marukitano/BEP3.0/BEP31/Foto_bestückter_Print.jpg

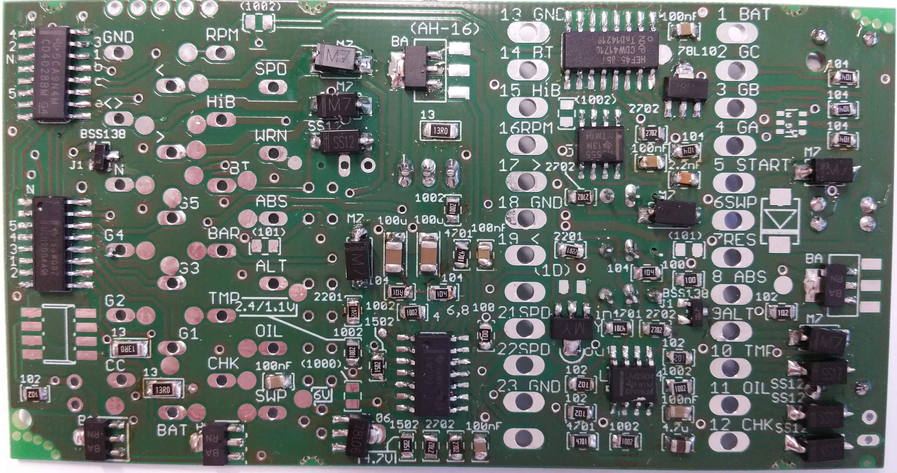
BEP31/Foto_bestückter_Print.jpg
