marukitano/BEP3.0/Liste verbessungen BEP3.pdf

Liste verbessungen BEP3.1 zu BEP3.2:

- ABS abschaltbar machen (zusätzlicher switch)
- Für das neue gehäuse 1mm kürzen (dann passt es ins alte und ins neue gehäuse, siehe bild )

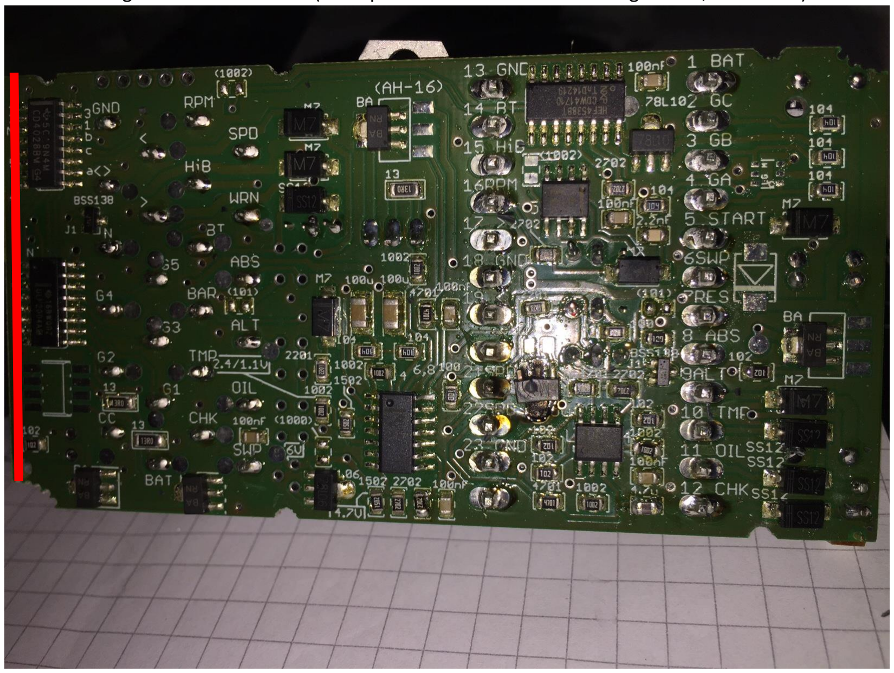
[picture p6: figure]

- Aussparung für Schraube auch an oberer Ecke anbringen (damit passts in beide gehäuse, siehe bild 2). Dafür müsste der 4028 ein stück versetzt werden.
- Beschriftung der schalter vervollständigen

- Stencil bestellen, der die aussparung für die Schutzdiode NICHT hat. Oft sind die Pads gebrückt nach den Lötofen und das gibt kurriose Fehler…

- Abstand Lödpads vergrössern zwischen switch und diode (häufiger fehler nach den Lötofen, siehe bild)
