marukitano/BEP3.0/BEP2 final/BMW_Gerberview.pdf

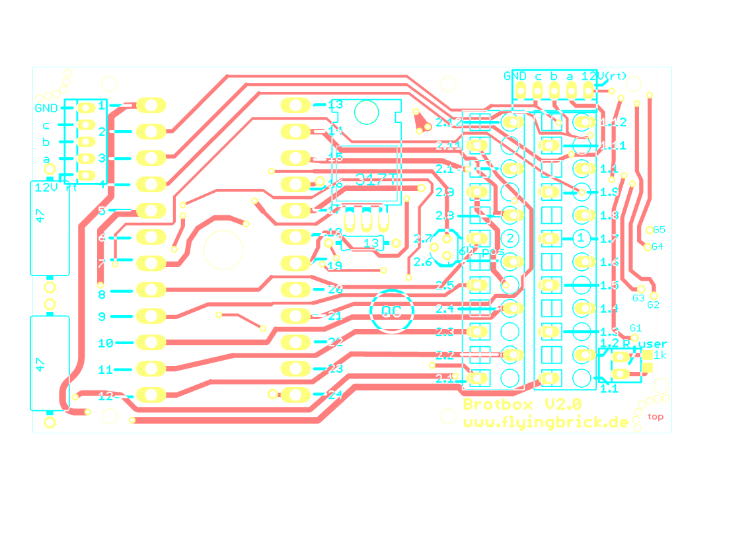
[picture p7: figure]

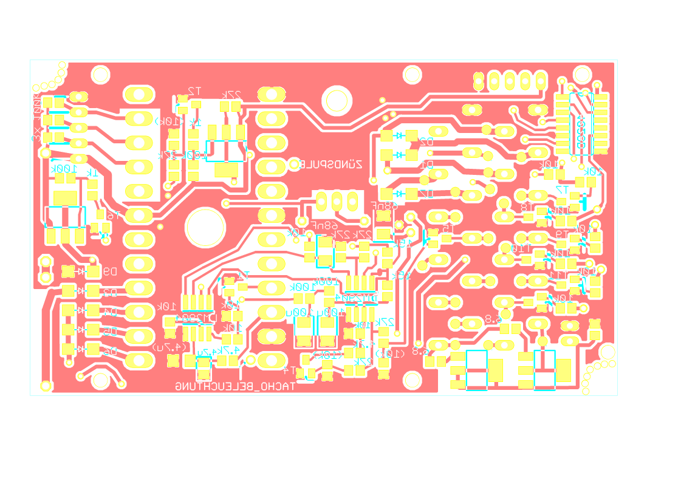
[picture p8: figure]
