marukitano/BEP3.0/BEP2 final/Board und Case BMW.pdf

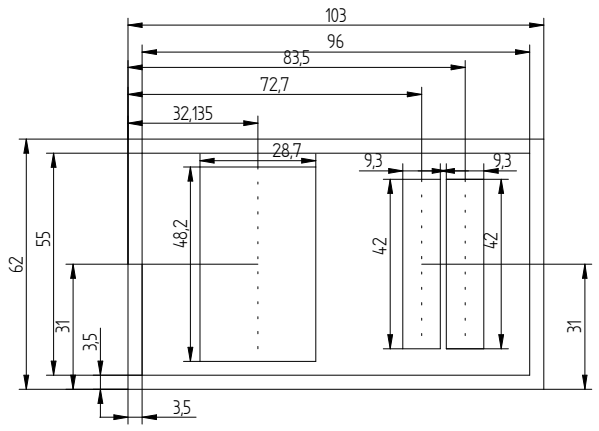
[picture p9: figure]
