marukitano/BEP3.0/BEP2 final/BMW_final_image.png

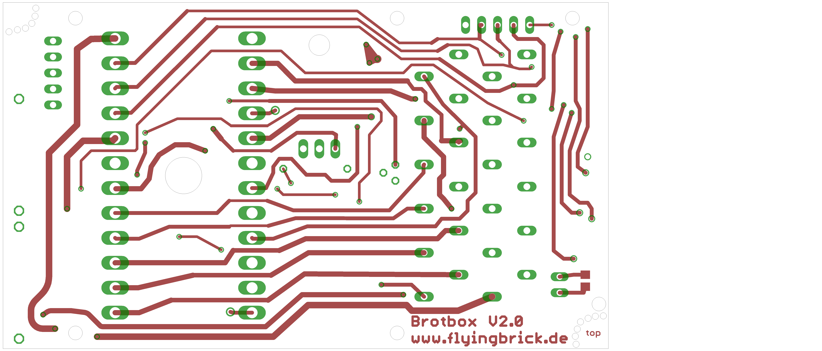
BEP2 final/BMW_final_image.png
