marukitano/BEP3.0/BEP2rev1/BEPrev1_BestückungAnsicht.png

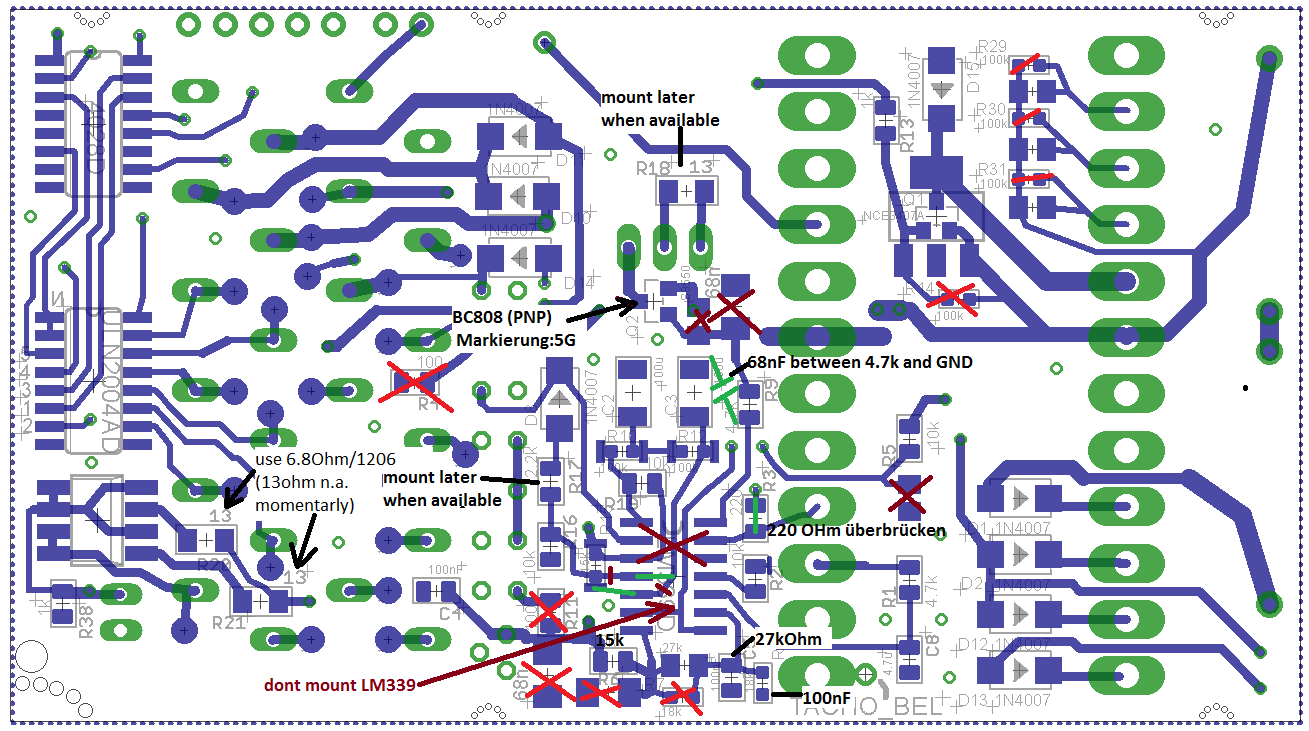
BEP2rev1/BEPrev1_BestückungAnsicht.png
