marukitano/BEP3.0/BEP2rev1/BEPrev_bot.png

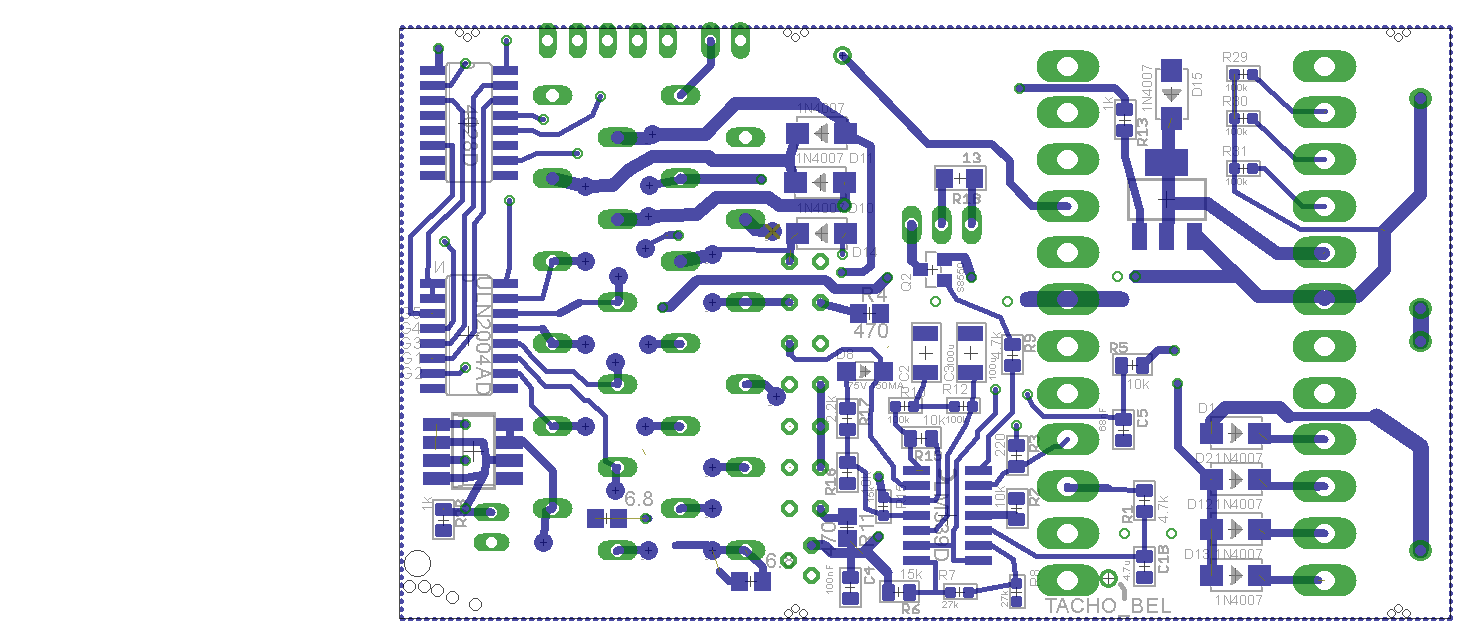
BEP2rev1/BEPrev_bot.png
