marukitano/BEP3.0/BEP2rev1/BEPrev_top.png

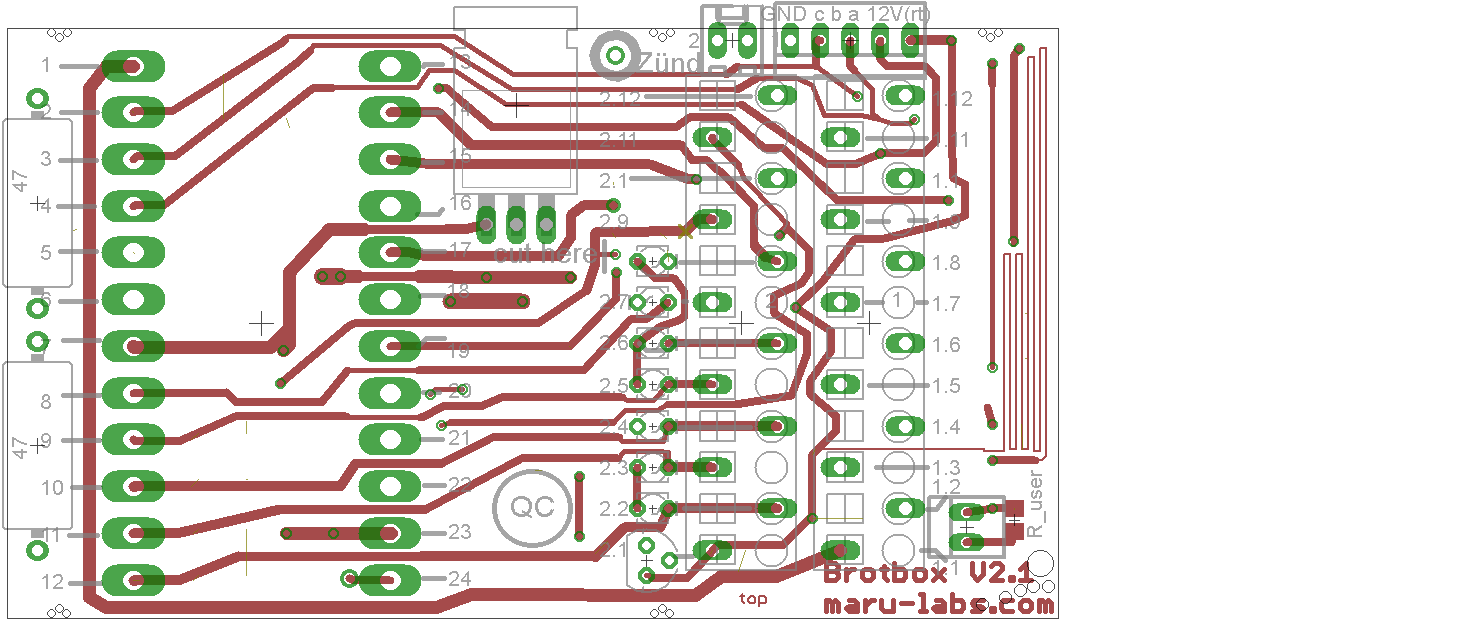
BEP2rev1/BEPrev_top.png
