marukitano/BEP3.0/BEP3/BEP3 Bestückung (weisser Hintergrund).png

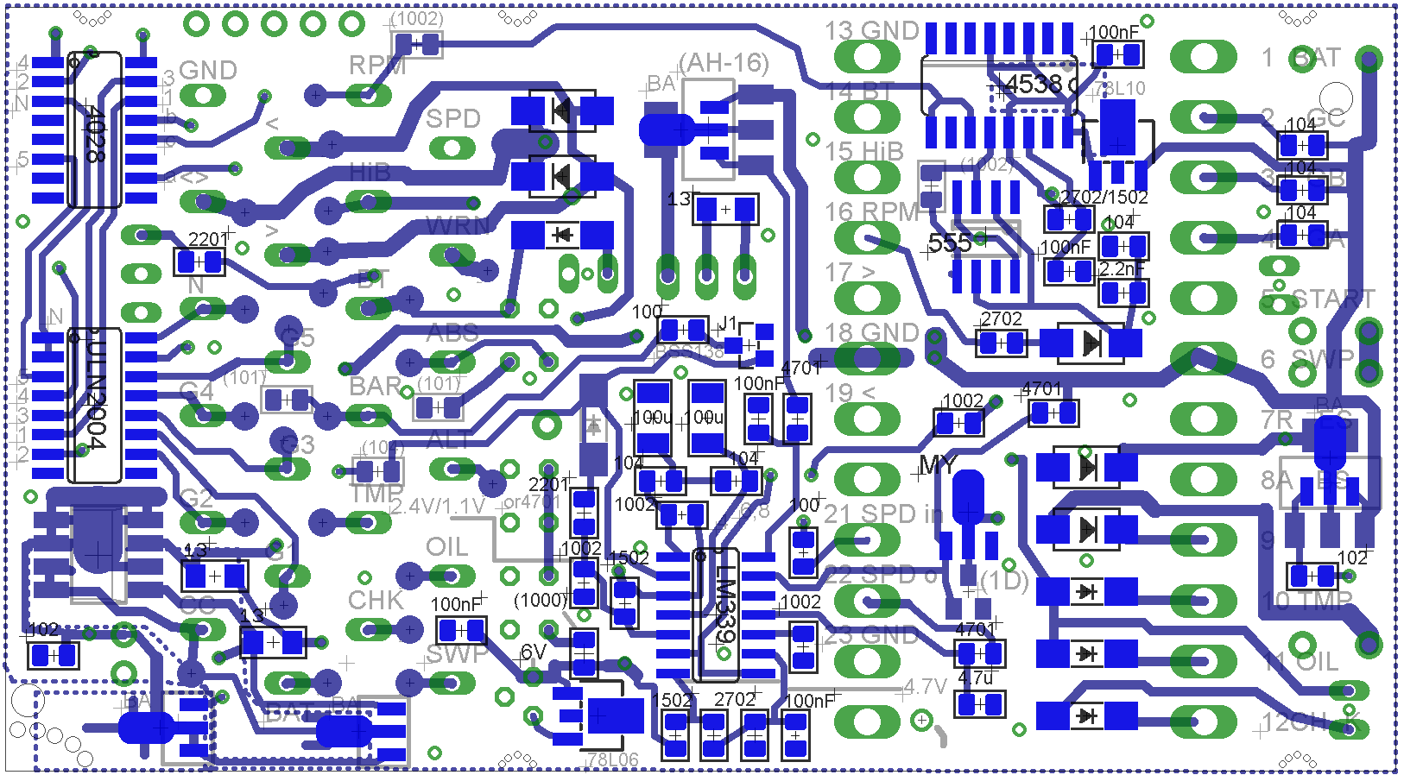
BEP3/BEP3 Bestückung (weisser Hintergrund).png
