marukitano/BEP3.0/BEP3/BEP3 Bestückung.png

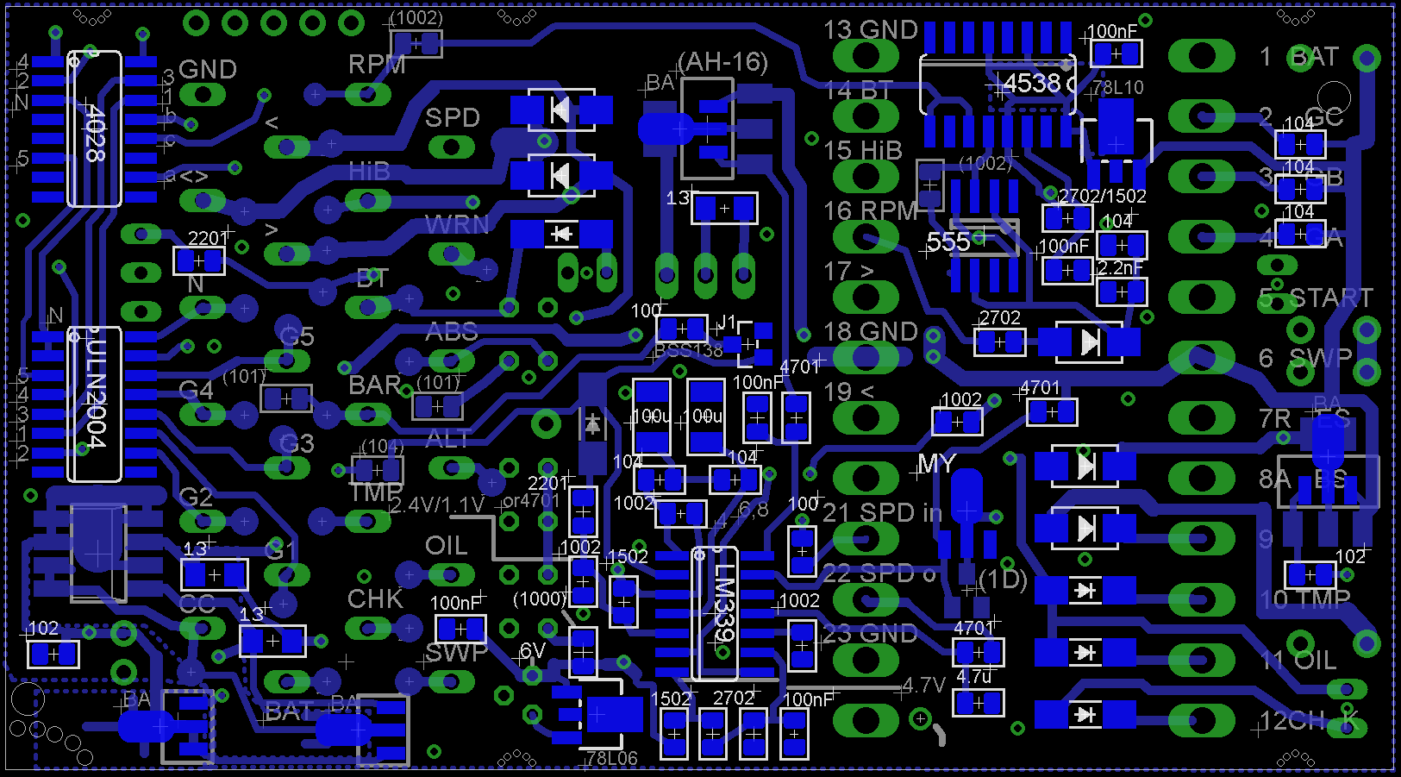
BEP3/BEP3 Bestückung.png
