marukitano/BEP3.0/BEP3/bot.png

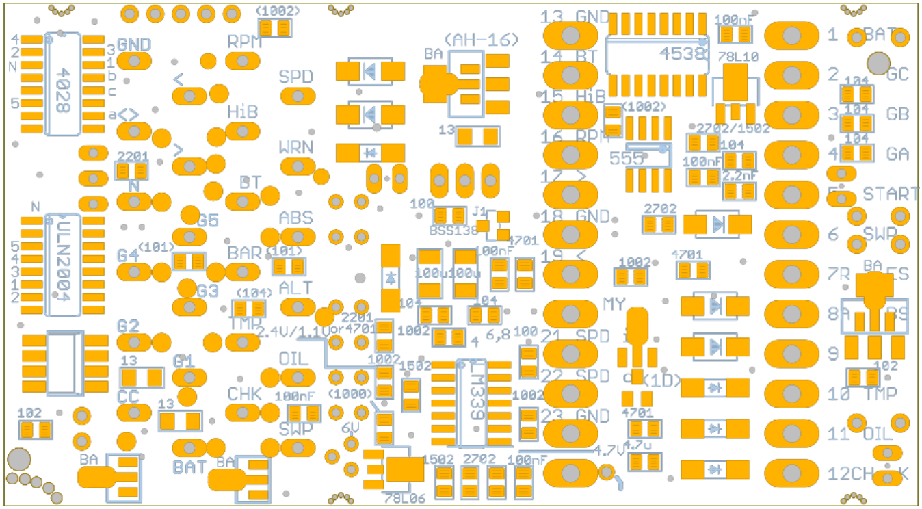
BEP3/bot.png
