marukitano/BEP3.0/BEP3/Schema Bep3.png

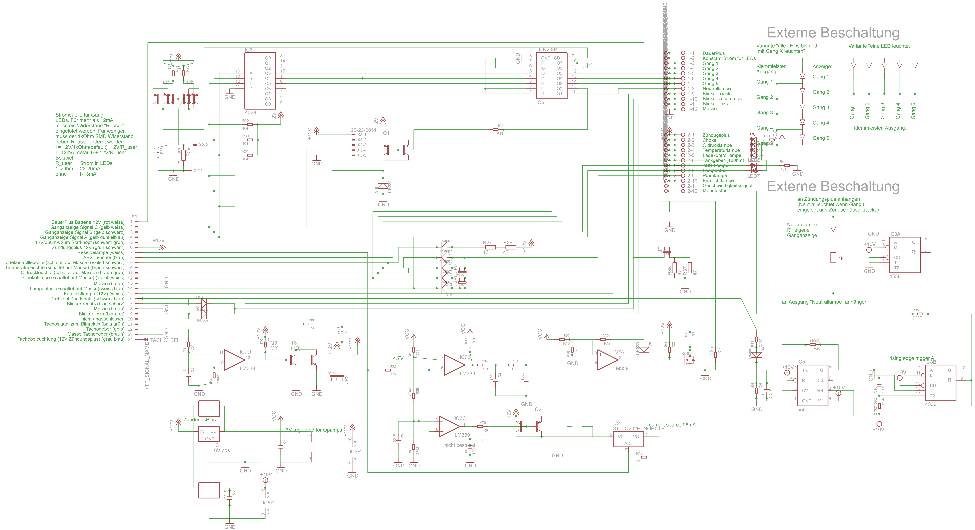
BEP3/Schema Bep3.png
