marukitano/BEP3.0/BEP3/top.png

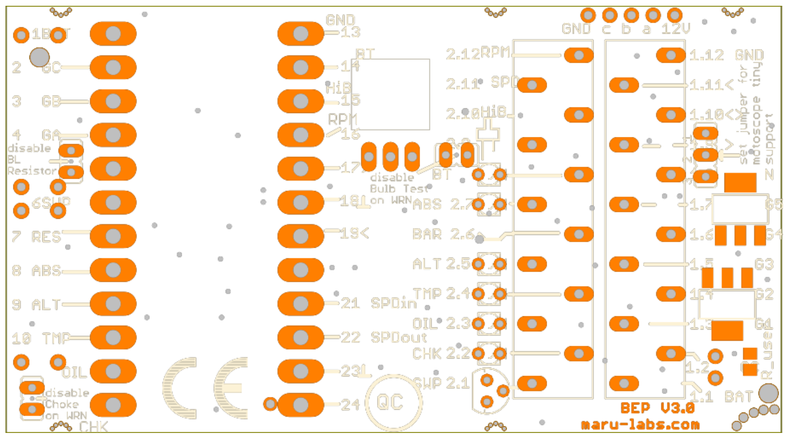
BEP3/top.png
