marukitano/BEP3.0/BEP31/Bestückungs-Plan(gimp)/Leiterbahnen mit SMD.png

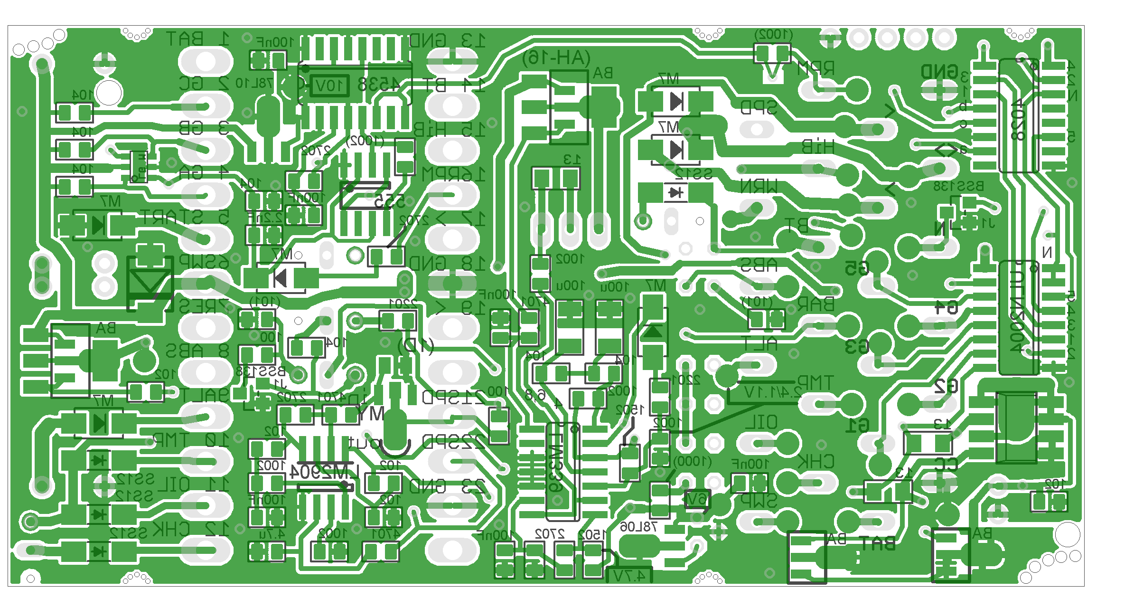
BEP31/Bestückungs-Plan(gimp)/Leiterbahnen mit SMD.png
