marukitano/BEP3.0/BEP31/Bestückungs-Plan(gimp)/SMD Teile.png

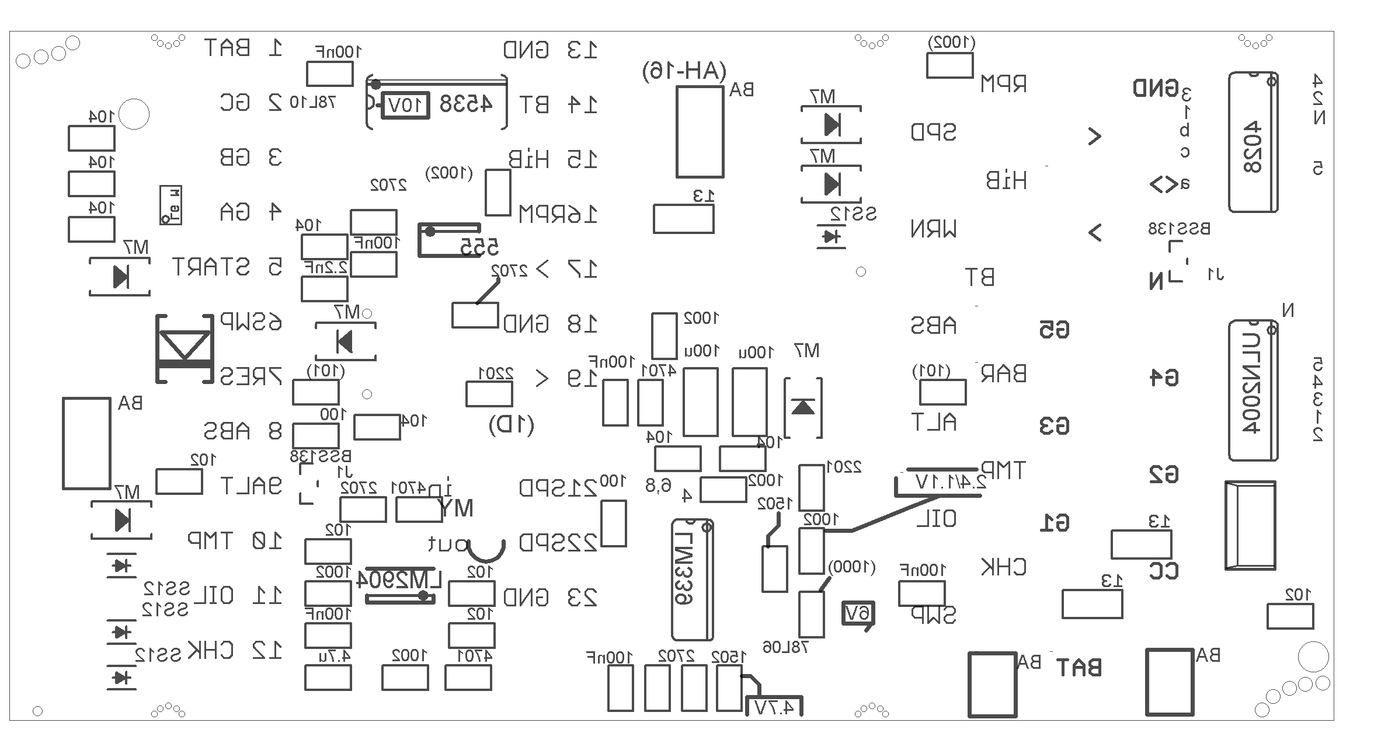
BEP31/Bestückungs-Plan(gimp)/SMD Teile.png
