marukitano/BEP3.0/BEP32/BEP32_6panel_Milling Layer 46 + Vcuts Layer 20 Eagle screenshot.png

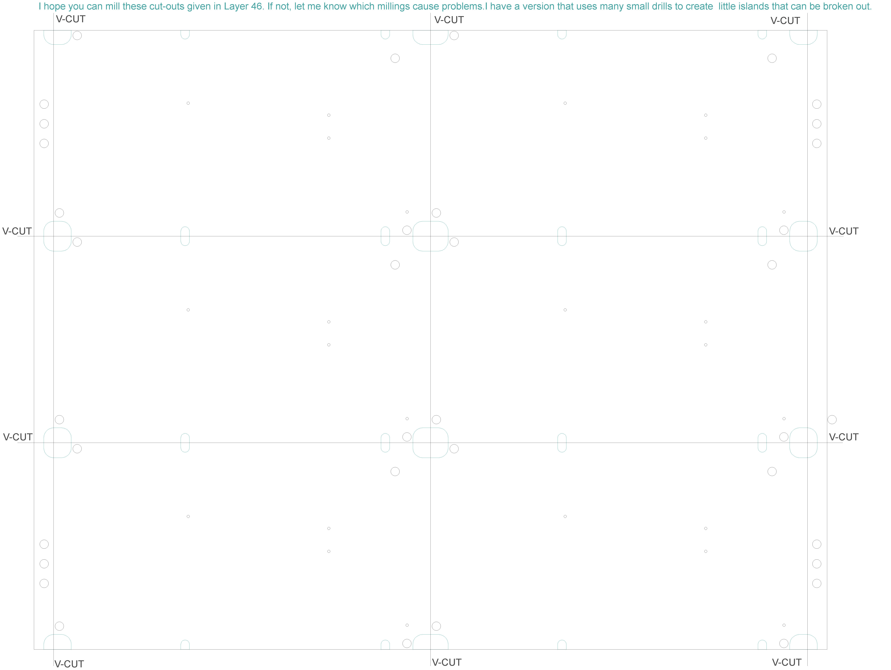
BEP32/BEP32_6panel_Milling Layer 46 + Vcuts Layer 20 Eagle screenshot.png
