marukitano/BEP3.0/BEP32/BEP32_Bestückungsdruck.PNG

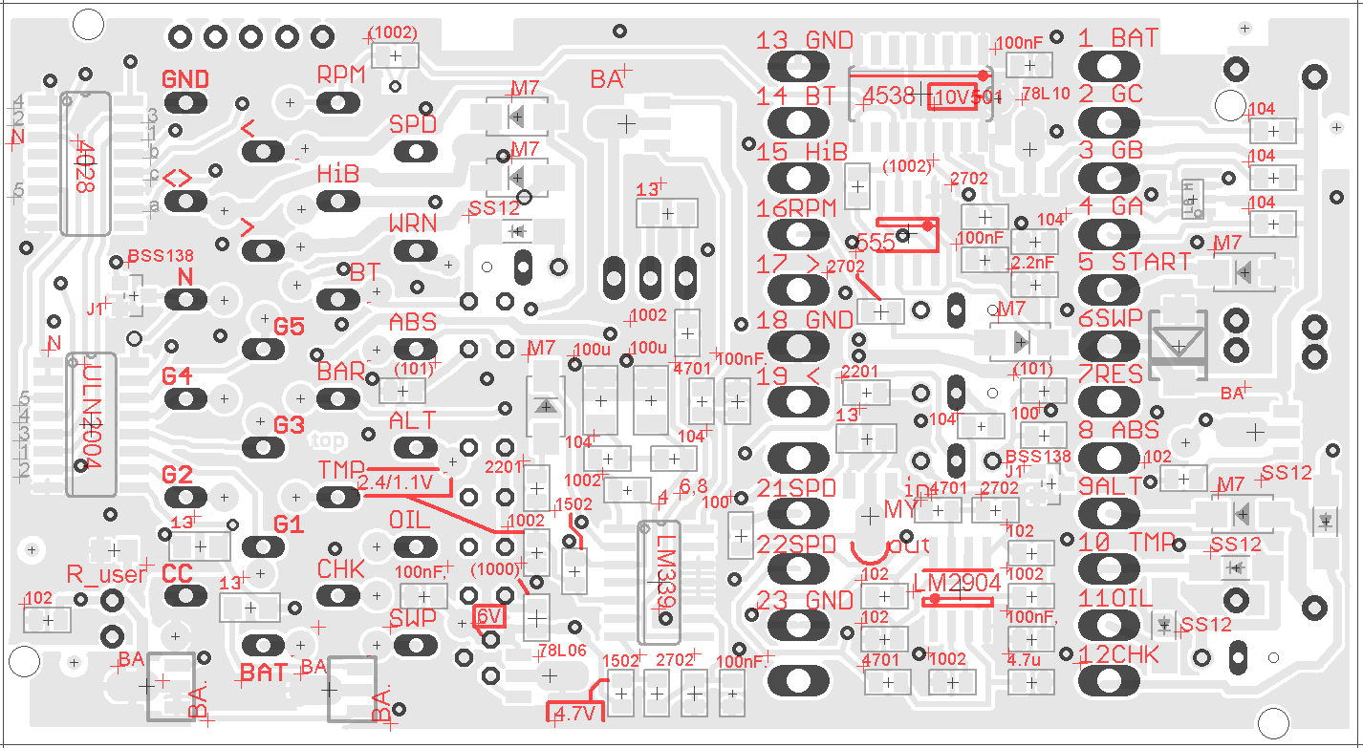
BEP32/BEP32_Bestückungsdruck.PNG
