marukitano/BEP3.0/BEP32/BEP32_Schalterbeschriftung.png

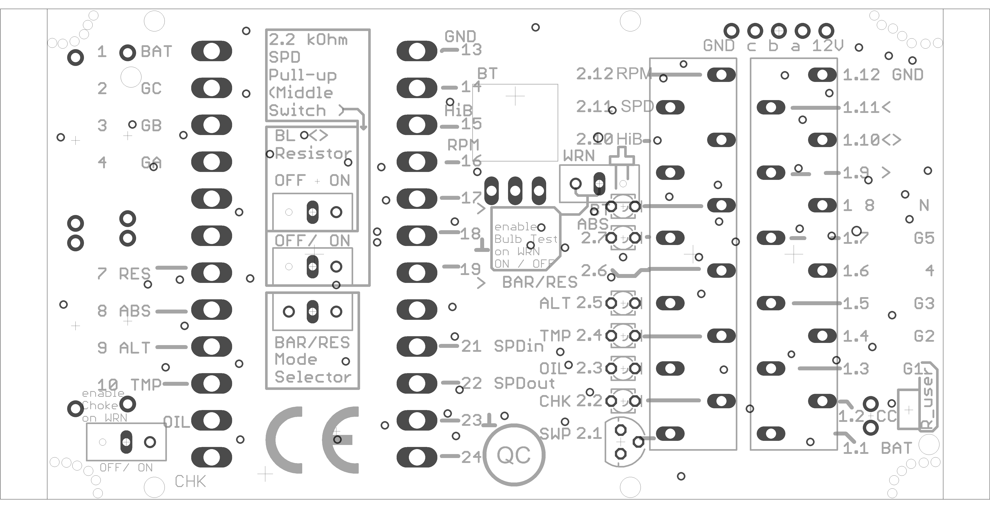
BEP32/BEP32_Schalterbeschriftung.png
