marukitano/BEP3.0/BEP33/BEP33 cream direkt export.png

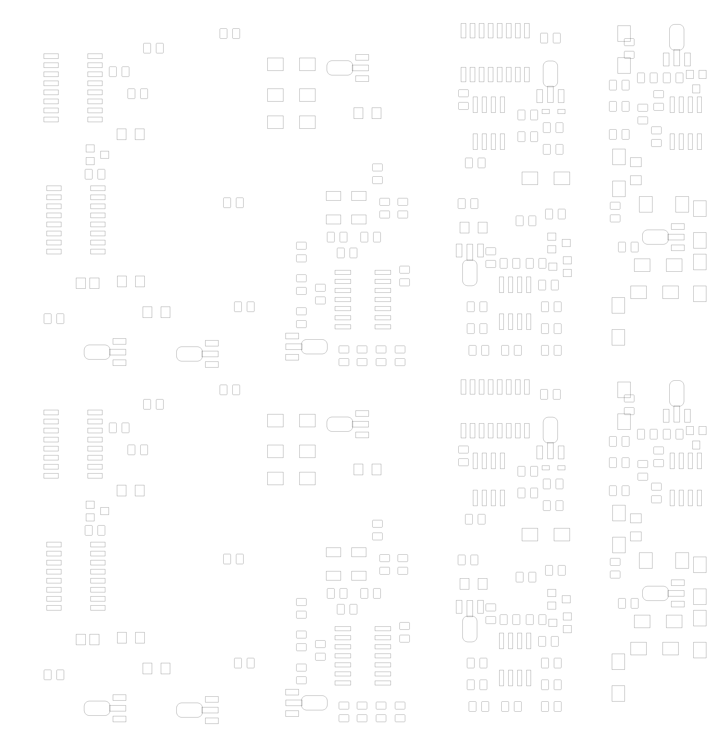
BEP33/BEP33 cream direkt export.png
