marukitano/BEP3.0/BEP33/sht31.png

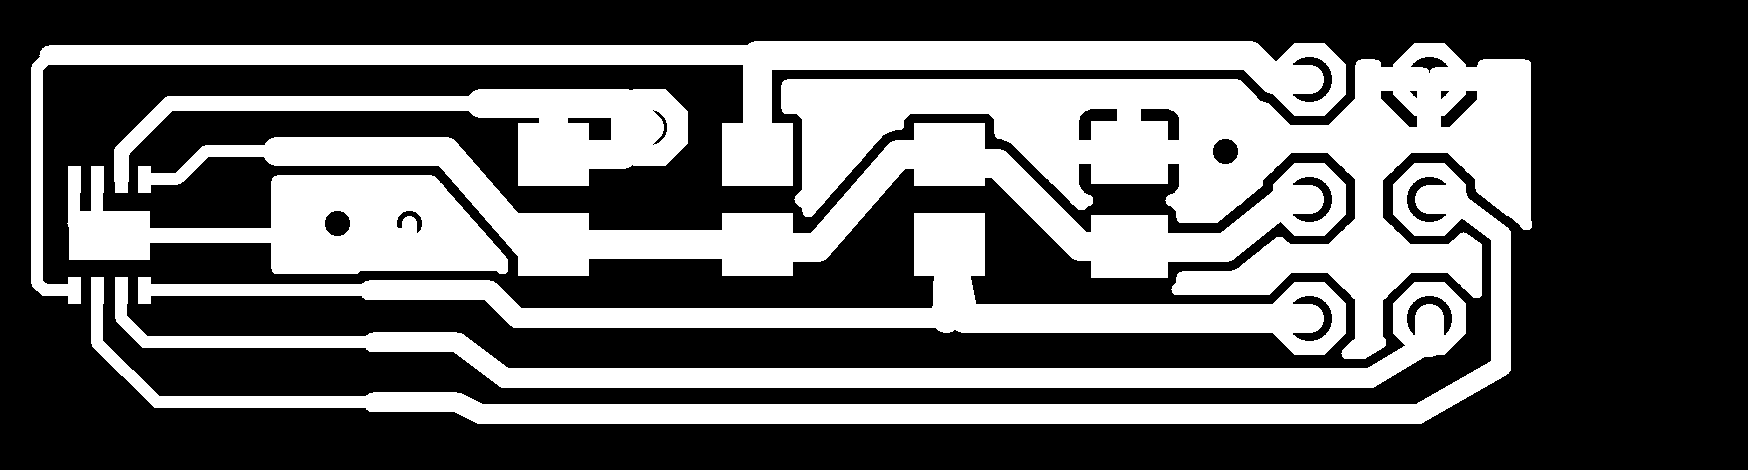
BEP33/sht31.png
