marukitano/BEP3.0/Brotbox original/Ganganzeige/Ganganzeige_nutzen_maske_bearb.png

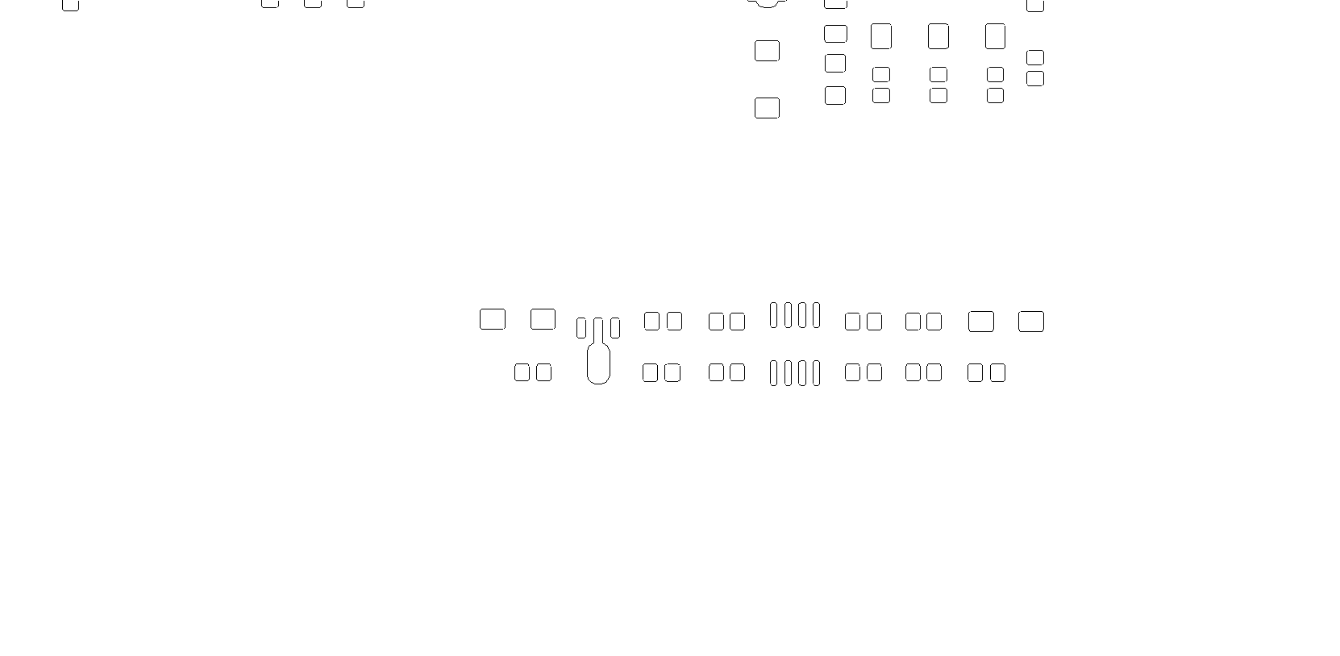
Brotbox original/Ganganzeige/Ganganzeige_nutzen_maske_bearb.png
