marukitano/BEP3.0/Kdiag/Board2.png

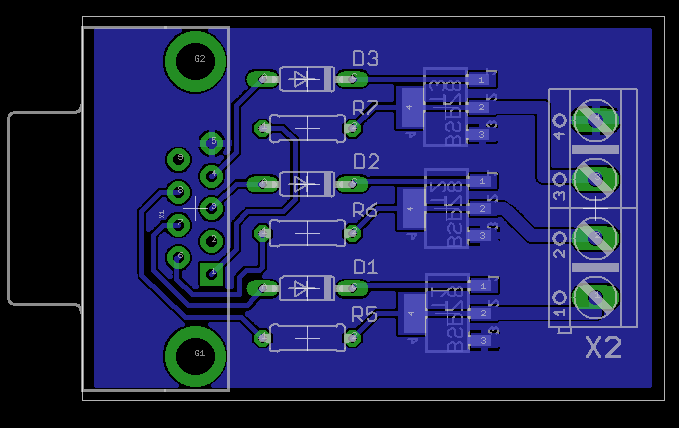
Kdiag/Board2.png
