marukitano/BEP3.0/BEP31/BEP31_final_BOM_ELON-MUSK_Jul-18-161850-2017_Conflict.xlsx

Dimensionen:
Board: | 96mmx50mm. FR4 1.6mm, HASL verzinnt (lead free)
Stückzahl | 500 und 1000
BOM:
SMD Bauteile auf Rückseite:
Qty | Value | Package | Device | Parts | Description |  |  | Farnell | Aliexpress | Preis/Stück in US$ | bei Stück-zahl | Bedarf f.500 Prints | Stock Marulabs | auf Rolle bei Marulabs vorhanden | techn. Anforderung für Alternative | Bemerkung
6 | 100nF | C0805 | CERAMIC-100NF-50V-10%-X7R(0805) | C4, C5, C7, C9, C10, C11 |  |  |  | ? | ? | 0.01 |  | 3000 | 0 | nein | ≥20V | ev. 0603
1 | 2.2nF | C0805 | CERAMIC-100NF-50V-10%-X7R(0805) | C1 |  |  |  |  | 32375506423 (https://www.aliexpress.com/item/Free-shipping-0805-SMD-capacitor-2200P-2-2nf-50V-222K-100PCS/32375506423.html) | 0.0045 | 200 | 500 | 0 | nein | ≥50V | ev. 0603
1 | 4.7u | C0805 | CERAMIC-4.7UF-25V-10%-X5R(0805) | C8 |  |  |  |  | 32376068362 (https://www.aliexpress.com/item/Free-shipping-0805-SMD-capacitor-4-7uf-50V-475Z-100PCS/32376068362.html) | 0.0059 | 200 | 500 | 0 | nein | ≥16V | ev. 0603
2 | 100u | C1206 | CERAMIC-100UF-6.3V-20%-X5R(1206) | C2, C3 |  |  |  |  | 32376068793 (https://www.aliexpress.com/item/Free-shipping-1206-SMD-capacitor-100uf-16V-107Z-100PCS/32376068793.html) | 0.041 | 100 | 1000 | 0 | nein | ≥6V | ev. 0805
6 | 1N4007 | DO-214AC | DIODE-GEN-PURPOSE-1KV-1A(DO-214AC) | D1, D3, D8, D10, D11, D15 |  |  |  |  | 32687291008 (https://www.aliexpress.com/item/3000PCS-1N4007-M7-SMA-DO-214AC-1A-1000-V-SMD-Rectifler-diodos/32687291008.html) | 0.008533333333 | 3000 | 3000 | 4000 | ja(Rolle=2000) | ≥1A,≥100V
4 | 1N5817 | DO-214AC | Schottky Diode | D2, D12, D13, D14 |  |  |  |  | 2024887597 (https://www.aliexpress.com/item/Free-Shipping-1000PCS-SS12-1N5817-1A-20V-SMA-Schottky-diode/2024887597.html) | 0.01 | 1000 | 2000 | ca. 1900 | ja(Rolle=2000) | ≥1A,≥20V | Flussspannung muss <0.25V sein bei 0.19mA Strom
1 | NE555D | SO08 | NE555D | IC5 | TIMER |  |  |  | 32686681723 (https://www.aliexpress.com/item/500PCS-NE555DR-NE555D-NE555-IC-555-SMD-assurance-NEW/32686681723.html) | 0.0264 | 500 | 500 | 0 | nein(Rolle=2500?)
1 | LM2904 | SO08 | LM2904 | IC10 | OP AMP also LM158; LM258; LM2904 |  |  |  | 32518015605 (https://www.aliexpress.com/item/500PCS-LM2904-LM2904DR-LM2904D-SOP-8/32518015605.html) | 0.03 | 500 | 500 | 0 | nein(Rolle=2500?) |  | Alternativ LM358/258/158
1 | LM339 | SO14 | LM339D | IC7 | Low Power Quad Comparators |  |  |  | 1245879199 (https://www.aliexpress.com/item/Free-Shipping-100PCS-LOT-Original-Integrated-circuit-ics-LM339-LM339DR/1245879199.html) | 0.047 | 100 | 500 | 0 | nein(Rolle=2500?) |  | Alternativ LM2901,LM239/139
1 | 4028 | SO16 | 4028D | IC3 | BCD to decimal DECODER |  |  | 2342417RL (http://ch.farnell.com/webapp/wcs/stores/servlet/ProductDisplay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) |  | 0.134 | 1000 | 500 | 500 Freihand | nein(Rolle=?) |  | CD4028BM
1 | 4538 | SO16 | 4538D | IC8 | Dual monostable MULTIVIBRATOR |  |  |  | 32694256723 (https://www.aliexpress.com/item/HEF4538-HEF4538BT-digital-logic-circuit-SOP16-imported-new-original-MHBX2/32694256723.html) | 0.14 | 100 | 500 | 0 | nein(Rolle=2500?) |  | CD14538BM alternativ
1 | ULN2004 | SO16 | ULN2004AD | IC6 | DRIVER ARRAY |  |  |  | 32667261685 (https://www.aliexpress.com/item/Free-shipping-500pcs-lot-ULN2004-ULN2004A-ULN2004ADR-SOP-16/32667261685.html) | 0.1 | 500 | 500 | 0 | nein(Rolle=2500?)
2 | BSS-138 | SOT-23 | SMD-MOSFET-N-CH-50V-200MA-BSS138W-7-F(SOT-23) | Q10, Q11 | BSS138W-7-F |  |  |  | 32316697150 (https://www.aliexpress.com/item/1000-PCS-LBSS138LT1G-SOT-23-BSS138-J1-Power-MOSFET-200-mAmps-50-Volts-N-hannel-SOT/32316697150.html) | 0.011 | 1000 | 1000 | 0 | nein(Rolle=3000) | RDS<6Ω | alternativ anderer SOT89 N Mosfet (Kleinsignal)
4 | BA | SOT89 | PNP-TRANSISTOR_SOT89 | Q1, Q2, Q7, Q8 | PNP TRANSISTOR 2SB1132 1A 32V |  |  |  | 32390023505 (https://www.aliexpress.com/item/Free-shopping-1000-PCS-2SB1132-SOT-89-B1132-PNP-1A-32V/32390023505.html) | 0.02 | 1000 | 2000 | 0 | nein | ≥1A,≥20V,HFE>100 bei 500mA | Exot! Ersatz muss gefunden werden oder wir kaufen mehr bei Aliexpress
1 | MY | SOT89 | NPN-TRANSISTOR_SOT89 | Q9 | NPN TRANSISTOR 2SC2873 2A 50V |  |  |  | 32590988708 (https://www.aliexpress.com/item/2SC2873-Y-2SC2873-MY-SOT89-NPN-Transistor-IC-x-1000PCS/32590988708.html) | 0.022 | 1000 | 500 | 0 | nein | ≥500mA,≥20V | Exot! Ersatz muss gefunden werden oder wir kaufen mehr bei Aliexpress. SOT89 N Mosfet wäre auch möglich
1 | 10V pos | SOT89 | 78L10 | IC2 | VOLTAGE REGULATOR |  |  |  | 32714846870 (https://www.aliexpress.com/item/500pcs-lot-in-stock-CJ78L10-78L10-10V-SOT-89/32714846870.html) | 0.04 | 500 | 500 | 500 | nein(Rolle=1000) |  | vorhande 500 Teile könnten wir auf leere Rolle spannen
1 | 6V pos | SOT89 | 78L06 | IC1 | VOLTAGE REGULATOR |  |  |  | 32716599879 (https://www.aliexpress.com/item/1000PCS-in-stock-78L06-6V-SOT-89/32716599879.html) | 0.02 | 1000 | 500 | 1000 | ja(Rolle=1000)
7 | 104 | R0805 | 100k | R10, R12, R22, R24, R29, R30, R31 |  |  |  | 2498052 (http://ch.farnell.com/walsin/wr08x1003ftl/dicksch-widerstand-100k-1-150v/dp/2498052) |  | 0.0013 | 5000 | 3500 | 5000 | ja |  | durch Zollner Standard 0603 ersetzen ausser zwei 1kOhm Widerständen (144mW Last ist zuviel für 0603)
5 | 2702 | R0805 | 27k | R8, R25, R44,R33,R34 |  |  |  | 2498084 (http://ch.farnell.com/walsin/wr08x2702ftl/dicksch-widerstand-27k-1-150v/dp/2498084) |  | 0.0013 | 5000 | 2500 | 5000 | ja
2 | 1502 | R0805 | 15k | R6, R15 |  |  |  | 2498062 (http://ch.farnell.com/walsin/wr08x1502ftl/dicksch-widerstand-15k-1-150v/dp/2498062) |  | 0.0013 | 5000 | 1000 | 5000 | ja
5 | 1002 | R0805 | 10k | R2, R5, R16, R19, R42 |  |  |  | 2498051 (http://ch.farnell.com/walsin/wr08x1002ftl/dicksch-widerstand-10k-1-150v/dp/2498051) |  | 0.0013 | 5000 | 2500 | 5000 | ja
3 | 4701 | R0805 | 4k7 | R1, R9, R32 |  |  |  | 2498105 (http://ch.farnell.com/walsin/wr08x4701ftl/dicksch-widerstand-4k7-1-150v/dp/2498105) |  | 0.0013 | 5000 | 1500 | 5000 | ja
2 | 2201 | R0805 | 2k2 | R17, R23 |  |  |  | 2498077 (http://ch.farnell.com/webapp/wcs/stores/servlet/ProductDisplay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) |  | 0.0013 | 5000 | 1000 | 5000 | ja
5 | 102 | R0805 | 1k | R13, R38, R43, R45, R46 |  |  |  | 2498050 (http://ch.farnell.com/walsin/wr08x1001ftl/dicksch-widerstand-1k-1-150v-0805/dp/2498050) |  | 0.0013 | 5000 | 2500 | 5000 | ja | >144mW (2 Stück)
2 | 100 | R0805 | 10R | R3,R7 |  |  |  | 2498048 (http://ch.farnell.com/walsin/wr08x10r0ftl/dicksch-widerstand-10r-1-150v/dp/2498048) |  | 0.0013 | 5000 | 1000 | 5000 | ja
3 | 13 | R1206 | 13R | R18, R20, R21 |  |  |  | 2497996 (http://ch.farnell.com/webapp/wcs/stores/servlet/ProductDisplay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) |  | 0.0021 | 5000 | 1500 | 5000 | ja | >120mW | ev 0805 jedoch besser 1206 (therm. Last ist 120mW und krit. Bauteil)
Zwischentotal: |  |  |  |  |  |  |  |  |  | 0.6596
Gehäuse und Platine
1 |  |  |  |  | Gehäuse |  |  |  | Reichelt SP+2000+SW (http://www.reichelt.de/SP-2000-SW/3/index.html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) | 2.343 | 1
1 |  |  |  |  | Platine |  |  |  | Seedstudio | 0.8 | 350
Zwischentotal: |  |  |  |  |  |  |  |  |  | 3.143
THT Bauteile auf vorderseite (wird voraussichtlich von Marulabs bestückt)
1 | LM317 | TO220 |  |  | Spannungsregler |  |  |  | 1246203110 (https://www.aliexpress.com/item/Free-Shipping-50PCS-POWER-TRANSISTORS-LM317-LM317T-TO-220-ST/1246203110.html) | 0.095 | 100
4 | 47 |  |  |  | 2W Leistungswiderstand bedrahtet |  |  |  | 32523580839 (https://www.aliexpress.com/item/Free-Shipping-200pcs-DIP-Resistors-carbon-Resisters-2W-47ohm-5-Carbon-Film-Resistor/32523580839.html) | 0.0375 | 200
2 | 3.96mm Pitch 12P |  |  |  | BMW Pfostenstecker |  |  |  | 888918208 (https://www.aliexpress.com/item/Free-shipping-100Pcs-lot-Wholesale-3-96mm-Pitch-12-Pins-PCB-Male-Box-Header-Bar-Connector/888918208.html) | 0.1728 | 100
5 | L8.5*W3.5MM 3P 2T mini toggle |  |  |  | ON/OFF Umschalter |  |  |  | 1800702995 (https://www.aliexpress.com/item/Free-shipping-1000PCS-L8-5-W3-5MM-3P-2T-mini-toggle-slide-switch-Handle-high-3mm/1800702995.html) | 0.0228 | 1000
2 | WAGO 2081-1132 |  |  |  | Wago Klemmleiste |  |  |  | Wago Schweiz | 2.1 | 500
Zwischentotal: |  |  |  |  |  |  |  |  |  | 4.9046
Optionale Teile (ev. für EMV Verträglichkeit notwendig)
1 | NUP4304SOT457_R | SOT457R_PHILIPS | NUP4304SOT457_R | U$3 |  |  |  |  |  | 0
1 | SM6T | DO214AA | SM6T | D4 | Z DIODE |  |  |  |  | 0
1 | SM6T | DO214AA | SM6T | D5 | Z DIODE |  |  |  |  | 0
Zwischentotal: |  |  |  |  |  |  |  |  |  | 0
Total: |  |  |  |  |  |  |  |  |  | 8.7072
BOM Zusammenfassung (nur SMD Komponenten):
 | Anzahl Bauteile | Anzahl unterschiedliche Werte | Package | Anzahl Pads/Bauteil | totale Anzahl Pads
Resistors | 31 | 8 | 805 | 2 | 62
 | 3 | 1 | 1206 | 2 | 6
Kond | 10 | 4 | 0805/1206 | 2 | 20
Diodes | 10 | 2 | DO-214AC | 2 | 20
IC | 2 | 2 | SO08 | 8 | 16
 | 1 | 1 | SO14 | 14 | 14
 | 3 | 3 | SO16 | 16 | 48
Transistors | 2 | 1 | SOT-23 | 3 | 6
& Regler | 7 | 4 | SOT89 | 4 | 28
Total count | 69 | 26 | 8 |  | 220
optional | 1 | 1 | SOT457 | 6 | 6
 | 1 | 1 | DO214AA | 2 | 2
 | 1 | 1 | DO214AA | 2 | 2
Total count | 3 | 3 | 2 |  | 10
BOM Zusammenfassung (nur SMD Komponenten):
 | Anzahl Bauteile | Anzahl unterschiedliche Werte | Package | 8mm Reel | 12mm Reel | 16mm Reel | Anzahl Pads/Bauteil | totale Anzahl Pads
Resistors | 31 | 8 | 805 | 8 |  |  | 2 | 62
 | 3 | 1 | 1206 | 1 |  |  | 2 | 6
Kond | 10 | 4 | 0805/1206 | 4 |  |  | 2 | 20
Diodes | 10 | 2 | DO-214AC |  | 2 |  | 2 | 20
IC | 2 | 2 | SO08 |  | 2 |  | 8 | 16
 | 1 | 1 | SO14 |  |  | 1 | 14 | 14
 | 3 | 3 | SO16 |  |  | 3 | 16 | 48
Transistors | 2 | 1 | SOT-23 | 1 |  |  | 3 | 6
& Regler | 7 | 4 | SOT89 |  | 4 |  | 4 | 28
Total count | 69 | 26 | 8 | 14 | 8 | 4 |  | 220
optional | 1 | 1 | SOT457 |  | 1 |  | 6 | 6
 | 1 | 1 | DO214AA |  | 1 |  | 2 | 2
 | 1 | 1 | DO214AA |  | 1 |  | 2 | 2
Total count | 3 | 3 | 2 | 0 | 3 | 0 |  | 10
momentan bestellt TVM802B |  |  |  | 25 | 12 | 5
 |  |  |  | 20 | 14 | 6
