marukitano/BEP3.0/BEP2 testboard/BMW_testboard.csv

Qty | Value | Device | Package | Parts | Description | MF | MPN | OC_FARNELL | OC_NEWARK | T | TP_SIGNAL_NAME
3 |  | MMBTA42LT1-NPN-SOT23-BEC | SOT23-BEC | T1, T2, T3 | NPN Transistror |  |  |  |  | SMBTA42
1 | 0 | R-EU_0207/12 | 0207/12 | R27 | RESISTOR, European symbol
1 | 100 | R-EU_0207/12 | 0207/12 | R22 | RESISTOR, European symbol
2 | 10k | R-EU_0207/12 | 0207/12 | R13, R32 | RESISTOR, European symbol
1 | 10k | R-EU_0207/15 | 0207/15 | R33 | RESISTOR, European symbol
6 | 10k | R-EU_R0805 | R0805 | R8, R9, R10, R12, R17, R23 | RESISTOR, European symbol
1 | 10n | C-EU025-024X044 | C025-024X044 | C3 | CAPACITOR, European symbol
2 | 10u | C-EU025-024X044 | C025-024X044 | C1, C2 | CAPACITOR, European symbol
1 | 20k | R-EU_0207/12 | 0207/12 | R14 | RESISTOR, European symbol
1 | 39 | R-EU_0207/12 | 0207/12 | R21 | RESISTOR, European symbol
17 | 390 | R-EU_R0805 | R0805 | R1, R2, R3, R4, R5, R6, R7, R11, R15, R16, R18, R19, R20, R28, R29, R30, R31 | RESISTOR, European symbol
1 | 4020N | 4020N | DIL16 | IC1 | 14-stage binary/ripple COUNTER
1 | BTS141 | BTS141 | TO220-3-45 | IC5 | Smart High-Side Power Switch
4 | DTE6K | DTE6K | DTE6K | S1, S2, S3, S4 | ITT SWITCH
1 | NE555 | NE555 | DIL-08 | IC2 | General purpose bipolar Timer | Arrow Electronics | NE555N | 1467742 | 89K1486
23 | TLLY4400 | TLLY4400 | LED3MM | öLDRUCK_SW2, ABS_BLINK, BEIDE, CHOKE_SW1, DAUERPLUS, FERNLICHT_BLK, GANG_1, GANG_2, GANG_3, GANG_4, GANG_5, GESCHW_WAGO_BLK, LADEKONTROL_BLK, LAMPENTEST_SW4, LINKS, NEUTRAL, RECHT, START/NEUTRAL, TACHSIG_REL_BLK, TANKGEB_SW1-4, TEMP...SW3, WARNLAMPE_SW4, ZüNDUNGSPLUS | Low Current (2mA) LED 3 mm Tinted Diffused Package color YELLOW | VISHAY SEMICONDUCTOR |  | 1612439
44 | TPSPAD1-1.5MM | TPSPAD1-1.5MM | P1-13 | 12V, 12V_, BL, BL-GR, BL-RT, BL-SW, BR, BR-GR, BR-SW, BR_, GB-SW, GB-WS, GE-BL, GND_, GR, GR-SW, SW-GR, TP12, TP13, TP14, TP15, TP20, TP27, TP28, TP29, TP31, TP32, TP33, TP34, TP35, TP36, TP37, TP38, TP39, TP40, TP41, TP42, TP43, TP44, VI-SW, VI-WS, WS, WS-BL, WS_ | TEST PIN
 | davon 22 gefederte Prüfspitzen
