marukitano/BEP3.0/BEP2 final/BEP2 - Ausgaben 2.xlsx

BEP Auslagen
Artikel | Preis | Marcus | Philipp | Richard
Reichelt Januar 2015 | 60 € | 60 €
CNC Juni 2015 | 650 € | 50 € | 600 €
Prüfspitzen August 2015 | 45 € | 45 €
Reichelt August 2015 | 25 € | 25 €
IMBUS M2 Schrauben 1000stk | 55 € | 55 €
Spacer 5mm (Bügelperlen schwarz) | 8 € |  |  | 8 €
EstlCAM (CNC-Software) | 39 € | 39 €
Karton zum Verschicken | 79 € | 79 €
Distrelec 3 Rollen SMD | 34 € |  | 34 €
Reichelt Grossbestellung Aug 2015 | 1095 € |  | 1095 €
Reichelt Verzollung 1. Lieferung | 60 € |  | 60 €
Reichelt Verzollung Nachlieferung
Finierfräser 5 stk | 18 € | 18 €
Filament 3D-Drucker | 100 € | 100 €
Bürklin Stecker Teil 1 | 65 € | 65 €
Bürklin Stecker Teil 2 | 180 € |  | 180 €
Stativ | 89 € | 89 €
Finierfräser 15 stk | 40 € | 40 €
Farnell Ics Sept 2015 | 150 € |  | 150 €
Multi CB Leiterplatten 250 Stück Sept 2015 | 440 € |  | 440 €
 | 3232 € | 665 € | 2559 € | 8 €
