marukitano/BEP3.0/BEP2 final/BEP2 - Ausgaben.xlsx

BEP Auslagen
Artikel | Preis | Marcus | Philipp | Richard
Reichelt Januar 2015 | 60 € | 60 €
CNC Juni 2015 | 650 € | 50 € | 600 €
Prüfspitzen August 2015 | 45 € | 45 €
Reichelt August 2015 | 25 € | 25 €
IMBUS M2 Schrauben 1000stk | 55 € | 55 €
Spacer 5mm (Bügelperlen schwarz) | 8 € |  |  | 8 €
315 grüne BMW-stecker | 220 € | 220 €
EstlCAM (Software) | 39 € | 39 €
AGP-Grafikkarte 512MB | 35 € | 35 €
Karton zum Verschicken | 79 € | 79 €
Distrelec 3 Rollen SMD | 34 € |  | 34 €
Reichelt Grossbestellung | 1095 € |  | 1095 €
Farnell Ics | 150 € |  | 150 €
 | 2495 € | 608 € | 1879 € | 8 €
