marukitano/BEP3.0/BMW_libraries/OPL_eagle_library/Seeed_OPL_List_download-20160229.xlsx

Sheet: OPL on sale list
OPL on sale list. 20160131
Seeed SKU | MPN | Description | Category | Package | Manufacturer | Datasheet | Price（$）/pcs | Pieces/set | Solder points Qty | Assem.Cost/pcs（$） | Image URL | Distributor-URL
306010055 | FC-135 | SMD Crystal 32.768KHz-7pF-20ppm-70k | Crystal Oscillator | 2P-L3.2*W1.5mm | Xinhunjing | http://www.seeedstudio.com/wiki/images/7/78/306010055.pdf | 0.391 | 5 | 4 | 0.40 |  | http://www.seeedstudio.com/depot/OPLopen-parts-library-catalog-c-136_138/#306010055
306010037 | 49S/18PF | DIP Crystal 16MHz-18pF-30ppm-50R | Crystal Oscillator | HC49/US | Xinhunjing | http://www.seeedstudio.com/wiki/images/5/57/306010037.pdf | 0.131 | 10 | 2 | 0.20 |  | http://www.seeedstudio.com/depot/OPLopen-parts-library-catalog-c-136_138/#306010037
306010054 | X053201602002 | SMD Crystal 16MHz-8pF-20ppm-40R | Crystal Oscillator | 2P-SMD-5.0X3.2 | JINGPENGYUAN | http://www.seeedstudio.com/wiki/images/9/9f/0500290P1.pdf | 0.430 | 5 | 2 | 0.20 |  | http://www.seeedstudio.com/depot/OPLopen-parts-library-catalog-c-136_138/#0500290P1
306010047 | 5032/2P | SMD Crystal 12MHz-20pF-20ppm-40R | Crystal Oscillator | 2P-L5.0*W3.2mm | Xinhunjing | http://www.seeedstudio.com/wiki/images/c/c7/306010047.pdf | 0.449 | 5 | 2 | 0.20 |  | http://www.seeedstudio.com/depot/OPLopen-parts-library-catalog-c-136_138/#306010047
305030028 | 2N7002,215 | SMD MOSFET N-CH 60V 300mA | Transistor | SOT-23 | NXP | http://www.seeedstudio.com/wiki/images/c/c6/305030028.pdf | 0.037 | 30 | 3 | 0.30 |  | http://www.seeedstudio.com/depot/OPLopen-parts-library-catalog-c-136_138/#305030028
305030015 | CJ2302 | SMD MOSFET N-CH 20V 2.1A | Transistor | SOT23 | JCET | http://www.seeedstudio.com/wiki/images/e/e7/0440200P1.pdf | 0.090 | 10 | 3 | 0.30 |  | http://www.seeedstudio.com/depot/OPLopen-parts-library-catalog-c-136_138/#0440200P1
305030014 | CJ2305 | SMD MOSFET P-CH 8V 4.1A | Transistor | SOT-23 | JCET | http://www.seeedstudio.com/wiki/images/a/ac/0440210P1.pdf | 0.078 | 10 | 3 | 0.30 |  | http://www.seeedstudio.com/depot/OPLopen-parts-library-catalog-c-136_138/#0440210P1
305010018 | S9013 | SMD Transistors NPN 25V 500mA | Transistor | SOT-23 | JCET | http://www.seeedstudio.com/wiki/images/6/67/0400000P1.pdf | 0.023 | 50 | 3 | 0.30 |  | http://www.seeedstudio.com/depot/OPLopen-parts-library-catalog-c-136_138/#0400000P1
305020006 | S8550 | SMD Transistors PNP 25V 500mA | Transistor | SOT-23 |  | http://www.seeedstudio.com/wiki/images/e/e5/0410030P1.pdf | 0.023 | 50 | 3 | 0.30 |  | http://www.seeedstudio.com/depot/OPLopen-parts-library-catalog-c-136_138/#0410030P1
305010017 | S8050 | SMD Transistors NPN 25V 500mW | Transistor | SOT-23 | JCET | http://www.seeedstudio.com/wiki/images/b/ba/305010017.pdf | 0.023 | 50 | 3 | 0.30 |  | http://www.seeedstudio.com/depot/OPLopen-parts-library-catalog-c-136_138/#305010017
312010004 | KS-12065D03YA | DIP Buzzer 3V/30mA;2700±300Hz | Audio product | 2P-7.6-D12*H6.5mm | Guangjixing | http://www.seeedstudio.com/wiki/images/c/cb/312020003.pdf | 0.504 | 5 | 2 | 0.20 |  | http://www.seeedstudio.com/depot/OPLopen-parts-library-catalog-c-136_138/#312010004
302020027 | TAJD477M006RNJ | SMD CAP Tantalum 470uF-6.3V;D | Capacitor | AVX-D | AVX |  | 0.918 | 5 | 2 | 0.20 |  | http://www.seeedstudio.com/depot/OPLopen-parts-library-catalog-c-136_138/#302020027
302030031 |  | DIP CAP Aluminum 100uF-16V | Capacitor | Radial-D5.0*H7.0mm | JWCO | http://www.seeedstudio.com/wiki/images/1/14/302030031.pdf | 0.015 | 50 | 2 | 0.20 |  | http://www.seeedstudio.com/depot/OPLopen-parts-library-catalog-c-136_138/#302030031
302020025 | TAJC107K010RNJ | SMD CAP Tantalum 100uF-10V 10% | Capacitor | AVX-C | AVX | http://www.seeedstudio.com/wiki/images/a/ae/0130170P1.pdf | 0.281 | 10 | 2 | 0.20 |  | http://www.seeedstudio.com/depot/OPLopen-parts-library-catalog-c-136_138/#0130170P1
302020022 | TAJC476K016RNJ | SMD CAP Tantalum 47uF-16V | Capacitor | AVX-C | AVX | http://www.seeedstudio.com/wiki/images/c/c7/302020022.pdf | 0.300 | 10 | 2 | 0.20 |  | http://www.seeedstudio.com/depot/OPLopen-parts-library-catalog-c-136_138/#302020022
302020020 | TAJB476K010RNJ | SMD CAP Tantalum 47uF-10V 10% | Capacitor | AVX-B | AVX | http://www.seeedstudio.com/wiki/images/f/fb/0130180P1.pdf | 0.157 | 10 | 2 | 0.20 |  | http://www.seeedstudio.com/depot/OPLopen-parts-library-catalog-c-136_138/#0130180P1
302020005 | TAJC476K006RNJ | SMD CAP Tantalum 47uF-6.3V | Capacitor | AVX-A | AVX |  | 0.109 | 20 | 2 | 0.20 |  | http://www.seeedstudio.com/depot/OPLopen-parts-library-catalog-c-136_138/#302020005
302020021 | TAJB226K010RNJ | SMD CAP Tantalum 22uF-10V 10% | Capacitor | AVX-B | AVX | http://www.seeedstudio.com/wiki/images/8/82/0130240P1.pdf | 0.125 | 20 | 2 | 0.20 |  | http://www.seeedstudio.com/depot/OPLopen-parts-library-catalog-c-136_138/#0130240P1
302010171 | CC0805MKX5R5BB226 | SMD CAP Ceramic 22uF-6.3V-20%-X5R; | Capacitor | 0805 | YAGEO |  | 0.055 | 50 | 2 | 0.20 |  | http://www.seeedstudio.com/depot/OPLopen-parts-library-catalog-c-136_138/#302010171
302010181 | CC1206KKX5R8BB106 | SMD CAP Ceramic 10uF-25V-10%-X5R | Capacitor | 1206 | YAGEO |  | 0.091 | 20 | 2 | 0.20 |  | http://www.seeedstudio.com/depot/OPLopen-parts-library-catalog-c-136_138/#302010181
302010178 | CC0805KKX5R8BB106 | SMD CAP Ceramic 10uF-25V-10%-X5R | Capacitor | 0805 | YAGEO | http://www.seeedstudio.com/wiki/images/2/20/0100080P1.pdf | 0.055 | 50 | 2 | 0.20 |  | http://www.seeedstudio.com/depot/OPLopen-parts-library-catalog-c-136_138/#0100080P1
302020019 | TAJB106K016RNJ | SMD CAP Tantalum 10uF-16V 10% | Capacitor | AVX-B | AVX | http://www.seeedstudio.com/wiki/images/f/f6/0130120P1.pdf | 0.109 | 20 | 2 | 0.20 |  | http://www.seeedstudio.com/depot/OPLopen-parts-library-catalog-c-136_138/#0130120P1
302020002 | TAJA106K016RNJ | SMD CAP Tantalum 10uF-16V 10% | Capacitor | AVX-A | AVX | http://www.seeedstudio.com/wiki/images/1/1b/0130050P1.pdf | 0.098 | 20 | 2 | 0.20 |  | http://www.seeedstudio.com/depot/OPLopen-parts-library-catalog-c-136_138/#0130050P1
302020011 | TAJA106K010RNJ | SMD CAP Tantalum 10uF-10V 10% | Capacitor | AVX-A | AVX | http://www.seeedstudio.com/wiki/images/5/59/0130040P1.pdf (http://www.seeedstudio.com/wiki/images/0/0d/302010146.pdf) | 0.105 | 20 | 2 | 0.20 |  | http://www.seeedstudio.com/depot/OPLopen-parts-library-catalog-c-136_138/#0130040P1
302010146 | CC0805KKX5R8BB475 | SMD CAP Ceramic 4.7uF-25V-10%-X5R;0805 | Capacitor | C0805 | YAGEO | http://www.seeedstudio.com/wiki/images/0/0d/302010146.pdf | 0.041 | 50 | 2 | 0.20 |  | http://www.seeedstudio.com/depot/OPLopen-parts-library-catalog-c-136_138/#302010146
302010111 | CC0603KRX5R6BB475 | SMD CAP Ceramic 4.7uF-10V-10%-X5R; | Capacitor | 0603 | YAGEO |  | 0.023 | 50 | 2 | 0.20 |  | http://www.seeedstudio.com/depot/OPLopen-parts-library-catalog-c-136_138/#302010111
302010019 | CC0402MRX5R5BB475 | SMD CAP Ceramic 4.7uF-6.3V-20%-X5R | Capacitor | 0402 | YAGEO |  | 0.016 | 10 | 2 | 0.20 |  | http://www.seeedstudio.com/depot/OPLopen-parts-library-catalog-c-136_138/#302010019
302010148 | CC0805KKX7R8BB225 | SMD CAP Ceramic 2.2uF-25V-10%-X7R;0805 | Capacitor | C0805 | YAGEO | http://www.seeedstudio.com/wiki/images/a/ac/302010056.pdf | 0.042 | 50 | 2 | 0.20 |  | http://www.seeedstudio.com/depot/OPLopen-parts-library-catalog-c-136_138/#302010148
302010179 | CC0805KKX7R8BB105 | SMD CAP Ceramic 1uF-25V-10%-X7R | Capacitor | 0805 | YAGEO | http://www.seeedstudio.com/wiki/images/8/89/0100440P1.pdf (http://www.seeedstudio.com/wiki/images/a/ac/302010056.pdf) | 0.014 | 50 | 2 | 0.20 |  | http://www.seeedstudio.com/depot/OPLopen-parts-library-catalog-c-136_138/#0100440P1
302010139 | CC0603KRX7R8BB105 | SMD CAP Ceramic 1uF-25V-10%-X7R | Capacitor | 0603 | YAGEO | http://www.seeedstudio.com/wiki/images/a/af/0100340P1.pdf (http://www.seeedstudio.com/wiki/File:302010056.pdf) | 0.010 | 100 | 2 | 0.20 |  | http://www.seeedstudio.com/depot/OPLopen-parts-library-catalog-c-136_138/#0100340P1
302010040 | CC0402KRX5R6BB105 | SMD CAP Ceramic 1uF-10V-10%-X5R | Capacitor | 0402 | YAGEO |  | 0.010 | 100 | 2 | 0.20 |  | http://www.seeedstudio.com/depot/OPLopen-parts-library-catalog-c-136_138/#302010040
302010073 | CC0603KRX7R8BB224 | SMD CAP Ceramic 220nF-25V-10%-X7R;0603 | Capacitor | 0603 | YAGEO | http://www.seeedstudio.com/wiki/images/a/ac/302010056.pdf | 0.014 | 100 | 2 | 0.20 |  | http://www.seeedstudio.com/depot/OPLopen-parts-library-catalog-c-136_138/#302010073
302010165 | CC0805KRX7R9BB104 | SMD CAP Ceramic 100nF-50V-10%-X7R; | Capacitor | 0805 | YAGEO | http://www.seeedstudio.com/wiki/File:302010056.pdf (http://www.seeedstudio.com/wiki/images/a/ac/302010056.pdf) | 0.010 | 100 | 2 | 0.20 |  | http://www.seeedstudio.com/depot/OPLopen-parts-library-catalog-c-136_138/#302010165
302010138 | CC0603KRX7R9BB104 | SMD CAP Ceramic 100nF-50V-10%-X7R | Capacitor | 0603 | YAGEO | http://www.seeedstudio.com/wiki/images/3/35/0100020P1.pdf | 0.010 | 100 | 2 | 0.20 |  | http://www.seeedstudio.com/depot/OPLopen-parts-library-catalog-c-136_138/#0100020P1
302010024 | CC0402KRX7R8BB104 | SMD CAP Ceramic 100nF-25V-10%-X7R | Capacitor | 0402 | YAGEO | http://www.seeedstudio.com/wiki/images/a/ac/302010056.pdf | 0.010 | 100 | 2 | 0.20 |  | http://www.seeedstudio.com/depot/OPLopen-parts-library-catalog-c-136_138/#302010024
302010002 | CC0402KRX7R8BB473 | SMD CAP Ceramic 47nF-25V-10%-X7R; | Capacitor | 0402 | YAGEO |  | 0.010 | 100 | 2 | 0.20 |  | http://www.seeedstudio.com/depot/OPLopen-parts-library-catalog-c-136_138/#302010002
302010088 | CC0603KRX7R9BB333 | SMD CAP Ceramic 33nF-50V-10%-X7R;0603 | Capacitor | 0603 | YAGEO | http://www.seeedstudio.com/wiki/images/a/ac/302010056.pdf | 0.010 | 100 | 2 | 0.20 |  | http://www.seeedstudio.com/depot/OPLopen-parts-library-catalog-c-136_138/#302010088
302010095 | CC0603KRX7R9BB223 | SMD CAP Ceramic 22nF-50V-10%-X7R;0603 | Capacitor | C0603 | YAGEO | http://www.seeedstudio.com/wiki/images/a/ac/302010056.pdf | 0.010 | 100 | 2 | 0.20 |  | http://www.seeedstudio.com/depot/OPLopen-parts-library-catalog-c-136_138/#302010095
302010202 |  | DIP CAP Ceramic Disc 10nF-50V-Y5V | Capacitor | Radial-Disc-2.5-D4.0mm |  |  | 0.020 | 100 | 2 | 0.20 |  | http://www.seeedstudio.com/depot/OPLopen-parts-library-catalog-c-136_138/#302010202
302010140 | CC0603KRX7R9BB103 | SMD CAP Ceramic 10nF-50V-10%-X7R | Capacitor | 0603 | YAGEO | http://www.seeedstudio.com/wiki/images/e/eb/0100350P1.pdf (http://www.seeedstudio.com/wiki/images/f/f0/302010067.pdf%20302010094) | 0.010 | 100 | 2 | 0.20 |  | http://www.seeedstudio.com/depot/OPLopen-parts-library-catalog-c-136_138/#0100350P1
302010006 | CC0402KRX7R9BB103 | SMD CAP Ceramic 10nF-50V-10%-X7R | Capacitor | 0402 | YAGEO | http://www.seeedstudio.com/wiki/images/f/f0/302010067.pdf | 0.010 | 100 | 2 | 0.20 |  | http://www.seeedstudio.com/depot/OPLopen-parts-library-catalog-c-136_138/#302010006
302010144 | CC0603KRX7R9BB472 | SMD CAP Ceramic 4.7nF-50V-10%-X7R | Capacitor | 0603 | YAGEO | http://www.seeedstudio.com/wiki/images/f/fd/0130360P1.pdf | 0.010 | 100 | 2 | 0.20 |  | http://www.seeedstudio.com/depot/OPLopen-parts-library-catalog-c-136_138/#0100850P1
302010141 | CC0603KRX7R9BB102 | SMD CAP Ceramic 1nF-50V-10%-X7R | Capacitor | 0603 | YAGEO | http://www.seeedstudio.com/wiki/images/c/cf/0100370P1.pdf | 0.010 | 100 | 2 | 0.20 |  | http://www.seeedstudio.com/depot/OPLopen-parts-library-catalog-c-136_138/#0100370P1
302010005 | CC0402KRX7R9BB102 | SMD CAP Ceramic 1nF-50V-10%-X7R; | Capacitor | 0402 | YAGEO |  | 0.010 | 50 | 2 | 0.20 |  | http://www.seeedstudio.com/depot/OPLopen-parts-library-catalog-c-136_138/#302010005
302010013 | CC0402JRNPO9BN221 | SMD CAP Ceramic 220pF-50V-5%-NPO | Capacitor | 0402 | YAGEO | http://www.seeedstudio.com/wiki/images/f/f0/302010067.pdf | 0.012 | 50 | 2 | 0.20 |  | http://www.seeedstudio.com/depot/OPLopen-parts-library-catalog-c-136_138/#302010013
302010076 | CC0603JRNPO9BN101 | SMD CAP Ceramic 100pF-50V-5%-NPO;0603 | Capacitor | 0603 | YAGEO | http://www.seeedstudio.com/wiki/images/f/f0/302010067.pdf | 0.010 | 100 | 2 | 0.20 |  | http://www.seeedstudio.com/depot/OPLopen-parts-library-catalog-c-136_138/#302010076
302010126 | CC0603JRNPO9BN390 | SMD CAP Ceramic 39pF-50V-5%-NPO;0603 | Capacitor | C0603 | YAGEO | http://www.seeedstudio.com/wiki/images/f/f0/302010067.pdf (http://www.seeedstudio.com/wiki/images/0/03/0100230P1.pdf) | 0.010 | 100 | 2 | 0.20 |  | http://www.seeedstudio.com/depot/OPLopen-parts-library-catalog-c-136_138/#302010126
302010142 | CC0603JRNPO9BN270 | SMD CAP Ceramic 27pF-50V-5%-NPO | Capacitor | 0603 | YAGEO | http://www.seeedstudio.com/wiki/images/0/01/0100410P1.pdf (http://www.seeedstudio.com/wiki/images/b/be/320020004.png) | 0.010 | 100 | 2 | 0.20 |  | http://www.seeedstudio.com/depot/OPLopen-parts-library-catalog-c-136_138/#0100410P1
302010027 | CC0402JRNPO9BN270 | SMD CAP Ceramic 27pF-50V-5%-NPO | Capacitor | 0402 | YAGEO | http://www.seeedstudio.com/wiki/images/b/be/320020004.png | 0.010 | 100 | 2 | 0.20 |  | http://www.seeedstudio.com/depot/OPLopen-parts-library-catalog-c-136_138/#302010027
302010143 | CC0603JRNPO9BN220 | SMD CAP Ceramic 22pF-50V-5%-NPO | Capacitor | 0603 | YAGEO | http://www.seeedstudio.com/wiki/images/7/73/0100620P1.pdf | 0.010 | 100 | 2 | 0.20 |  | http://www.seeedstudio.com/depot/OPLopen-parts-library-catalog-c-136_138/#0100620P1
302010018 | CC0402JRNPO9BN220 | SMD CAP Ceramic 22pF-50V-5%-NPO | Capacitor | 0402 | YAGEO | http://www.seeedstudio.com/wiki/File:302010067.pdf (http://www.seeedstudio.com/wiki/images/b/be/320020004.png) | 0.010 | 100 | 2 | 0.20 |  | http://www.seeedstudio.com/depot/OPLopen-parts-library-catalog-c-136_138/#302010018
302010016 | CC0402JRNPO9BN180 | SMD CAP Ceramic 18pF-50V-5%-NPO | Capacitor | 0402 | YAGEO |  | 0.010 | 100 | 2 | 0.20 |  | http://www.seeedstudio.com/depot/OPLopen-parts-library-catalog-c-136_138/#302010016
302010067 | CC0603JRNPO9BN120 | SMD CAP Ceramic 12pF-50V-5%-NP0 | Capacitor | 0603 | YAGEO | http://www.seeedstudio.com/wiki/images/f/f0/302010067.pdf | 0.010 | 100 | 2 | 0.20 |  | http://www.seeedstudio.com/depot/OPLopen-parts-library-catalog-c-136_138/#302010067
302010097 | CC0603JRNPO9BN100 | SMD CAP Ceramic 10pF-50V-5%-NPO | Capacitor | 0603 | YAGEO | http://www.seeedstudio.com/wiki/images/b/be/320020004.png | 0.010 | 100 | 2 | 0.20 |  | http://www.seeedstudio.com/depot/OPLopen-parts-library-catalog-c-136_138/#302010097
302010001 | CC0402JRNPO9BN100 | SMD CAP Ceramic 10pF-50V-5%-NPO | Capacitor | 0402 | YAGEO |  | 0.010 | 100 | 2 | 0.20 |  | http://www.seeedstudio.com/depot/OPLopen-parts-library-catalog-c-136_138/#302010001
302010223 | CC0402CRNPO9BN2R2 | SMD CAP Ceramic 2.2pF-50V-0.25PF-NPO | Capacitor | 0402 | YAGEO | http://www.seeedstudio.com/wiki/images/b/be/320020004.png | 0.010 | 100 | 2 | 0.20 |  | http://www.seeedstudio.com/depot/OPLopen-parts-library-catalog-c-136_138/#302010223
320020037 | P125-1102A0BS116A3 | DIP White Male Header VERT | Connector | 1*2P-2.54-2.54-11.6/3.0mm | YXCON | http://www.seeedstudio.com/wiki/images/b/be/320020004.png (http://www.seeedstudio.com/wiki/images/c/cb/320020019.png) | 0.013 | 20 | 2 | 0.20 |  | http://www.seeedstudio.com/depot/OPLopen-parts-library-catalog-c-136_138/#320020037
320020016 | P125-1102A0BS116A1 | DIP Black Male Header VERT | Connector | 1*2P-2.54-2.54-11.6/3.0mm | YXCON | http://www.seeedstudio.com/wiki/images/b/be/320020004.png | 0.010 | 20 | 2 | 0.20 |  | http://www.seeedstudio.com/depot/OPLopen-parts-library-catalog-c-136_138/#320020016
320020079 |  | DIP Black Male Header VERT | Connector | 1X3P-2.54-2.54-11.6/3.0 | YXCON | http://www.seeedstudio.com/wiki/images/0/02/3460810P1.pdf (http://www.seeedstudio.com/wiki/images/b/be/320020004.png) | 0.019 | 20 | 3 | 0.30 |  | http://www.seeedstudio.com/depot/OPLopen-parts-library-catalog-c-136_138/#3460810P1
320020061 | P125-1103A0BR138A1 | DIP Black Male Header R/A | Connector | 1*3P-2.54-2.54-6.0mm-90D-1 | YXCON |  | 0.039 | 20 | 3 | 0.30 |  | http://www.seeedstudio.com/depot/OPLopen-parts-library-catalog-c-136_138/#320020061
320020077 | P125-12A1BS116A1 | SMD Crystal 32.768KHz-7pF-20ppm-70k | Connector | 2X3P-2.54-2.54-11.6/3.0 | YXCON | http://www.seeedstudio.com/wiki/images/7/72/3460180P1.pdf (http://www.seeedstudio.com/wiki/images/8/8b/320020018.png) | 0.059 | 20 | 6 | 0.60 |  | http://www.seeedstudio.com/depot/OPLopen-parts-library-catalog-c-136_138/#3460180P1
320020027 | P125-1203A0BS116A2 | DIP Yellow Male Header VERT | Connector | 2*3P-2.54-2.54-11.6/3.0mm | YXCON | http://www.seeedstudio.com/wiki/images/7/77/320020027.png | 0.086 | 20 | 6 | 0.60 |  | http://www.seeedstudio.com/depot/OPLopen-parts-library-catalog-c-136_138/#320020027
320020017 | P125-1104A0BS116A1 | DIP Black Male Header VERT | Connector | 1*4P-2.54-2.54-11.6/3.0mm | YXCON | http://www.seeedstudio.com/wiki/images/f/fb/320020089.png | 0.026 | 20 | 4 | 0.40 |  | http://www.seeedstudio.com/depot/OPLopen-parts-library-catalog-c-136_138/#320020017
320020078 | P125-1106A1BS116A1 | SMD Crystal 32.768KHz-7pF-20ppm-70k | Connector | 1X6P-2.54-2.54-11.6/3.0mm | YXCON | http://www.seeedstudio.com/wiki/images/2/2d/3460650P1.pdf | 0.026 | 20 | 6 | 0.60 |  | http://www.seeedstudio.com/depot/OPLopen-parts-library-catalog-c-136_138/#3460650P1
320020019 | P125-1106A0BR138A1 | DIP Black Short Male Header R/A | Connector | 1X6P-2.54-2.54-6.0mm-90D-1 | YXCON | http://www.seeedstudio.com/wiki/images/c/cb/320020019.png (http://www.seeedstudio.com/wiki/images/a/a7/320030035.png) | 0.035 | 20 | 6 | 0.60 |  | http://www.seeedstudio.com/depot/OPLopen-parts-library-catalog-c-136_138/#320020019
320020080 | P125-1108A1BS116A1 | DIP Black Male Header VERT | Connector | 1X8P-2.54-2.54-11.6/3.0 | YXCON | http://www.seeedstudio.com/wiki/images/b/b5/3461050P1.pdf (http://www.seeedstudio.com/wiki/images/0/0d/320030039.pdf) | 0.034 | 20 | 8 | 0.80 |  | http://www.seeedstudio.com/depot/OPLopen-parts-library-catalog-c-136_138/#3461050P1
320020010 |  | DIP Black Male Header VERT | Connector | 1*40P-2.54-2.54-11.6/3.0mm | YXCON | http://www.seeedstudio.com/wiki/images/2/25/320020010.pdf | 0.172 | 5 | 40 | 4.00 |  | http://www.seeedstudio.com/depot/OPLopen-parts-library-catalog-c-136_138/#320020010
320030017 | F185-1104A1BSYA1 | DIP Black Female Header VERT | Connector | 1*4P-2.54-8.5mm | YXCON | http://www.seeedstudio.com/wiki/images/0/0d/320030039.pdf (http://www.seeedstudio.com/wiki/images/c/c9/320030076.png) | 0.084 | 10 | 4 | 0.40 |  | http://www.seeedstudio.com/depot/OPLopen-parts-library-catalog-c-136_138/#320030017
320030066 |  | DIP Long Blue Female Header | Connector | 2X3P-2.54-8.5+1.5-12.3 | YXCON | http://www.seeedstudio.com/wiki/images/0/01/3461240P1.pdf (http://www.seeedstudio.com/wiki/images/7/70/320030001.pdf) | 0.208 | 10 | 6 | 0.60 |  | http://www.seeedstudio.com/depot/OPLopen-parts-library-catalog-c-136_138/#3461240P1
320030019 | F185-1106A1BSYA3 | DIP Yellow Female Header VERT | Connector | 1*6P-2.54-8.5mm | YXCON | http://www.seeedstudio.com/wiki/images/0/0d/320030039.pdf | 0.168 | 10 | 6 | 0.60 |  | http://www.seeedstudio.com/depot/OPLopen-parts-library-catalog-c-136_138/#320030019
320030012 | F185-1106A1BSYA2 | DIP Long Black Female Header VERT | Connector | 1*6P-2.54-8.5mm | YXCON | http://www.seeedstudio.com/wiki/images/0/0d/320030039.pdf (http://www.seeedstudio.com/wiki/images/f/f2/3460170P1.pdf) | 0.202 | 10 | 6 | 0.60 |  | http://www.seeedstudio.com/depot/OPLopen-parts-library-catalog-c-136_138/#320030012
320030060 | F185-1106A1BSYC1 | DIP Black Female Header VERT | Connector | 1X6P-2.54-8.5 | YXCON | http://www.seeedstudio.com/wiki/images/b/b1/3460270P1.pdf (http://www.seeedstudio.com/wiki/images/6/6e/320030009.png) | 0.101 | 20 | 6 | 0.60 |  | http://www.seeedstudio.com/depot/OPLopen-parts-library-catalog-c-136_138/#3460270P1
320030067 |  | DIP Long Blue Female Header | Connector | 1X6P-2.54-8.5+2.5-12.3 | YXCON | http://www.seeedstudio.com/wiki/images/0/0d/3461250P1.pdf | 0.184 | 10 | 6 | 0.60 |  | http://www.seeedstudio.com/depot/OPLopen-parts-library-catalog-c-136_138/#3461250P1
320030068 |  | DIP Long Blue Female Header | Connector | 1X8P-2.54-8.5+2.5-12.3 | YXCON | http://www.seeedstudio.com/wiki/images/4/49/3461260P1.pdf (http://www.seeedstudio.com/wiki/images/5/5d/320070002%26320070007.pdf) | 0.245 | 10 | 8 | 0.80 |  | http://www.seeedstudio.com/depot/OPLopen-parts-library-catalog-c-136_138/#3461260P1
320030065 | F185-1108A1BSYC1 | DIP Yellow Female Header | Connector | 1X8P-2.54-8.5 | YXCON | http://www.seeedstudio.com/wiki/images/1/18/3460590P1.pdf (http://www.seeedstudio.com/wiki/images/5/5d/320070002%26320070007.pdf) | 0.202 | 10 | 8 | 0.80 |  | http://www.seeedstudio.com/depot/OPLopen-parts-library-catalog-c-136_138/#3460590P1
320030061 | F185-1108A1BSYC1 | DIP Black Female Header VERT | Connector | 1X8P-2.54-8.5 | YXCON | http://www.seeedstudio.com/wiki/images/2/27/3460290P1.pdf | 0.143 | 10 | 8 | 0.80 |  | http://www.seeedstudio.com/depot/OPLopen-parts-library-catalog-c-136_138/#3460290P1
320030013 | F185-2108A1BSYA1 | DIP Long Black Female Header VERT | Connector | 1*8P-2.54-(8.5+1.5)mm-10.5 | YXCON | http://www.seeedstudio.com/wiki/images/2/2d/320030013.png | 0.269 | 10 | 8 | 0.80 |  | http://www.seeedstudio.com/depot/OPLopen-parts-library-catalog-c-136_138/#320030013
320030001 | F185-2110A0ASYA1 | DIP Long Blue Female Header | Connector | 1*10P-2.54-8.5+2.5-12.3mm | YAGEO | http://www.seeedstudio.com/wiki/images/7/70/320030001.pdf | 0.283 | 10 | 10 | 1.00 |  | http://www.seeedstudio.com/depot/OPLopen-parts-library-catalog-c-136_138/#320030001
320030039 | F185-1110A1BSYA1 | DIP Long Black Female Header VERT | Connector | 1*10P-2.54-8.5mm | YAGEO | http://www.seeedstudio.com/wiki/images/0/0d/320030039.pdf | 0.337 | 10 | 10 | 1.00 |  | http://www.seeedstudio.com/depot/OPLopen-parts-library-catalog-c-136_138/#320030039
320030059 | F185-1110A1BSYC1 | DIP Yellow Female Header VERT | Connector | 1*10P-2.54-8.5mm | YXCON | http://www.seeedstudio.com/wiki/images/f/f2/3460170P1.pdf | 0.211 | 10 | 10 | 1.00 |  | http://www.seeedstudio.com/depot/OPLopen-parts-library-catalog-c-136_138/#320030059
320030009 | F243-1110A1BSUA1 | DIP Black Female Header VERT; | Connector | 1*10P-2.0-4.3mm | YXCON | http://www.seeedstudio.com/wiki/images/6/6e/320030009.png | 0.253 | 10 | 10 | 1.00 |  | http://www.seeedstudio.com/depot/OPLopen-parts-library-catalog-c-136_138/#320030009
320190003 |  | DIP Black Jumper;2P-2.54 | Connector | 2P-2.54 | TAIFENG | http://www.seeedstudio.com/wiki/images/e/ee/3460440P1.pdf | 0.010 | 50 | 0 | 0.00 |  | http://www.seeedstudio.com/depot/OPLopen-parts-library-catalog-c-136_138/#3460440P1
320090000 | ST-TF-003A | SMD Micro SD Card Socket | Connector | 9P-SMD-W/-RING | SUNTECH | http://www.seeedstudio.com/wiki/images/3/3e/3300060P1.PDF | 0.508 | 10 | 13 | 1.30 |  | http://www.seeedstudio.com/depot/OPLopen-parts-library-catalog-c-136_138/#3300060P1
320090008 |  | SMD Micro SD Card Socket | Connector | TF-01 | BEST | http://www.seeedstudio.com/wiki/images/2/22/320090008.pdf | 0.246 | 10 | 10 | 1.00 |  | http://www.seeedstudio.com/depot/OPLopen-parts-library-catalog-c-136_138/#320090008
320010007 | ST-USB-003A | DIP USB-A-Famale | Connector | 4P-2.0-90D | suntech |  | 0.207 | 10 | 4 | 0.40 |  | http://www.seeedstudio.com/depot/OPLopen-parts-library-catalog-c-136_138/#320010007
320010000 | ST-USB-001G | SMD Micro USB-B-W/P | Connector | 5+4-0.65-L7.4*W5.0*H2.35mm | SUNTECH |  | 0.265 | 10 | 8 | 0.80 |  | http://www.seeedstudio.com/depot/OPLopen-parts-library-catalog-c-136_138/#320010000
320010014 | ST-USB-013A | DIP Mini USB-B | Connector | MINI-B-5P-SMD | SUNTECH | http://www.seeedstudio.com/wiki/images/6/68/3400030P1.pdf | 0.177 | 10 | 9 | 0.90 |  | http://www.seeedstudio.com/depot/OPLopen-parts-library-catalog-c-136_138/#3400030P1
320110031 |  | DIP Green Screw Terminal;2P-5.0 | Connector | 2P-5.0 | GOOSVN | http://www.seeedstudio.com/wiki/images/e/ee/3470110P1.pdf (http://www.seeedstudio.com/wiki/images/c/c0/320140010.pdf) | 0.155 | 10 | 2 | 0.20 |  | http://www.seeedstudio.com/depot/OPLopen-parts-library-catalog-c-136_138/#3470110P1
320110028 |  | DIP Green Screw Terminal;2P-3.5 | Connector | 2P-3.5 | GOOSVN | http://www.seeedstudio.com/wiki/images/4/49/3470070P1.pdf | 0.155 | 10 | 2 | 0.20 |  | http://www.seeedstudio.com/depot/OPLopen-parts-library-catalog-c-136_138/#3470070P1
320110029 |  | DIP Green Screw Terminal;3P-5.0 | Connector | 3P-5.0 | GOOSVN | http://www.seeedstudio.com/wiki/images/f/f0/3470080P1.pdf | 0.232 | 10 | 3 | 0.30 |  | http://www.seeedstudio.com/depot/OPLopen-parts-library-catalog-c-136_138/#3470080P1
320120003 | DC-005 | DIP Black DC Jack;2.1MM | Connector | PW-3P-2.1 | BEST | http://www.seeedstudio.com/wiki/images/1/15/3410020P1.pdf | 0.107 | 10 | 3 | 0.30 |  | http://www.seeedstudio.com/depot/OPLopen-parts-library-catalog-c-136_138/#3410020P1
320120002 |  | DIP Black DC Jack;2.1MM; | Connector | PW-3P-2.1 | BEST | http://www.seeedstudio.com/wiki/images/c/c0/3410010P1.pdf (http://www.seeedstudio.com/wiki/images/5/5a/304090041.pdf) | 0.206 | 10 | 3 | 0.30 |  | http://www.seeedstudio.com/depot/OPLopen-parts-library-catalog-c-136_138/#3410010P1
320110027 |  | DIP White Male JST connector;2P-2.0 | Connector | 2P-2.0-90D |  | http://www.seeedstudio.com/wiki/images/e/e8/3410070P1.pdf (http://www.seeedstudio.com/wiki/images/5/5d/304090059.pdf) | 0.013 | 50 | 2 | 0.20 |  | http://www.seeedstudio.com/depot/OPLopen-parts-library-catalog-c-136_138/#3410070P1
320110026 |  | SMD White Male JST connector;2P-2.0 | Connector | 2P-SMD-2.0-90D |  | http://www.seeedstudio.com/wiki/images/f/f3/3410050P1.pdf (http://www.seeedstudio.com/wiki/images/5/56/304090057.pdf) | 0.109 | 20 | 2 | 0.20 |  | http://www.seeedstudio.com/depot/OPLopen-parts-library-catalog-c-136_138/#3410050P1
320110030 | 1125S-SMT-4P | SMD White Male Header VERT;4Pin-2.0 | Connector | 4P-SMD-2.0 | TAIFENG | http://www.seeedstudio.com/wiki/images/d/d5/3470090P1.pdf | 0.209 | 10 | 4 | 0.40 |  | http://www.seeedstudio.com/depot/OPLopen-parts-library-catalog-c-136_138/#3470090P1
320110032 | 1125R-SMT-4P | SMD White Male Header VERT;4Pin-2.0 | Connector | 4P-SMD-2.0-90D | TAIFENG | http://www.seeedstudio.com/wiki/images/e/e0/3470120P1.pdf (http://www.seeedstudio.com/wiki/images/d/d1/304090040.pdf) | 0.183 | 10 | 4 | 0.40 |  | http://www.seeedstudio.com/depot/OPLopen-parts-library-catalog-c-136_138/#3470120P1
320110034 | 1125R-4P | DIP White Male Header 90D;4Pin-2.0 | Connector | 4P-2.0-90D | TAIFENG | http://www.seeedstudio.com/wiki/images/4/40/3470140P1.pdf (http://www.seeedstudio.com/wiki/images/8/87/304090038.pdf) | 0.028 | 30 | 4 | 0.40 |  | http://www.seeedstudio.com/depot/OPLopen-parts-library-catalog-c-136_138/#3470140P1
320110033 | 1125S-4P | DIP White Male Header VERT;4Pin-2.0 | Connector | 4P-2.0 | TAIFENG | http://www.seeedstudio.com/wiki/images/6/69/3470130P1.pdf (http://www.seeedstudio.com/wiki/images/5/53/304090039.pdf) | 0.024 | 30 | 4 | 0.40 |  | http://www.seeedstudio.com/depot/OPLopen-parts-library-catalog-c-136_138/#3470130P1
320110048 |  | SMD I-PEX MFH1 Connector | Connector | U-FL | I-PEX | http://www.seeedstudio.com/wiki/images/e/ee/3450020P1.pdf | 0.410 | 10 | 4 | 0.40 |  | http://www.seeedstudio.com/depot/OPLopen-parts-library-catalog-c-136_138/#3450020P1
320140004 | MJ88-BX11-RVSL2 | DIP RJ45 Connector;8P-R/A-With LED | Connector | 8P-R/A | Heling Electronic | http://www.seeedstudio.com/wiki/images/f/f7/3420050P1.pdf | 0.927 | 3 | 14 | 1.40 |  | http://www.seeedstudio.com/depot/OPLopen-parts-library-catalog-c-136_138/#3420050P1
304090042 | 19-217-R6C-AL1M2VY-3T | LED-SMD Red Diffused | LED | 0603 | Everlight | http://www.seeedstudio.com/wiki/images/e/ef/0330020P1.pdf (http://www.seeedstudio.com/wiki/images/1/15/304090054.pdf) | 0.031 | 50 | 2 | 0.20 |  | http://www.seeedstudio.com/depot/OPLopen-parts-library-catalog-c-136_138/#0330020P1
304090046 | 17-215SURC/S530-A2/TR8 | SMD LED Clear-Red | LED | 0805 | Everlight | http://www.seeedstudio.com/wiki/images/1/13/304090046.pdf (http://www.seeedstudio.com/wiki/images/7/72/304090016.pdf) | 0.059 | 25 | 2 | 0.20 |  | http://www.seeedstudio.com/depot/OPLopen-parts-library-catalog-c-136_138/#304090046
304090041 |  | DIP LED Red-Red | LED | Radial-2P-2.54-3mm | Chengguangxing | http://www.seeedstudio.com/wiki/images/5/5a/304090041.pdf (http://www.seeedstudio.com/wiki/File:304090051.pdf) | 0.034 | 50 | 2 | 0.20 |  | http://www.seeedstudio.com/depot/OPLopen-parts-library-catalog-c-136_138/#304090041
304090059 | UR502DC | DIP LED Vaporous-Red-Red | LED | Radial-2P-2.54-5mm | Chengguangxing | http://www.seeedstudio.com/wiki/images/5/5d/304090059.pdf | 0.039 | 30 | 2 | 0.20 |  | http://www.seeedstudio.com/depot/OPLopen-parts-library-catalog-c-136_138/#304090059
304090057 | 17-215SYGC/S530-E2/TR8 | SMD LED Clear-Green | LED | 0805 | Everlight | http://www.seeedstudio.com/wiki/images/5/56/304090057.pdf (http://www.seeedstudio.com/wiki/images/0/05/304090053.pdf) | 0.059 | 25 | 2 | 0.20 |  | http://www.seeedstudio.com/depot/OPLopen-parts-library-catalog-c-136_138/#304090057
304090043 | 19-217-G7C-AN1P2-3T | SMD LED Clear-Green | LED | 0603 | Everlight | http://www.seeedstudio.com/wiki/images/f/f9/0330010P1.pdf | 0.031 | 50 | 2 | 0.20 |  | http://www.seeedstudio.com/depot/OPLopen-parts-library-catalog-c-136_138/#0330010P1
304090040 |  | DIP LED Green-Green | LED | Radial-2P-2.54-3.0mm | Chengguangxing | http://www.seeedstudio.com/wiki/images/d/d1/304090040.pdf | 0.037 | 50 | 3 | 0.30 |  | http://www.seeedstudio.com/depot/OPLopen-parts-library-catalog-c-136_138/#304090040
304090038 | G502DC | DIP LED Green-Green | LED | Radial-2P-2.54-5mm | Chengguangxing | http://www.seeedstudio.com/wiki/images/8/87/304090038.pdf (http://www.seeedstudio.com/wiki/images/4/4d/304060001.pdf) | 0.041 | 30 | 4 | 0.40 |  | http://www.seeedstudio.com/depot/OPLopen-parts-library-catalog-c-136_138/#304090038
304090039 | 17-215UYC/S530-A3/TR8 | SMD LED Clear-Yellow | LED | 0805 | Everlight | http://www.seeedstudio.com/wiki/images/5/53/304090039.pdf (http://www.seeedstudio.com/wiki/images/0/06/304060003.pdf) | 0.059 | 25 | 2 | 0.20 |  | http://www.seeedstudio.com/depot/OPLopen-parts-library-catalog-c-136_138/#304090039
304090044 | 19-217-Y5C-AM1N1VY-3T | SMD LED Clear-Yellow | LED | 0603 | Everlight | http://www.seeedstudio.com/wiki/File:0330050P1.PDF | 0.031 | 50 | 2 | 0.20 |  | http://www.seeedstudio.com/depot/OPLopen-parts-library-catalog-c-136_138/#0330050P1
304090071 | ADL-0603W | SMD LED Yellow-White | LED | 0603 | Chengguangxing | http://www.seeedstudio.com/wiki/images/9/9b/304090071.pdf | 0.107 | 25 | 2 | 0.20 |  | http://www.seeedstudio.com/depot/OPLopen-parts-library-catalog-c-136_138/#304090071
304090065 | CZXR-80RGB03-A | DIP LED RGB Common Anode | LED | Radial-4P-2.0-8mm | Chengguangxing | http://www.seeedstudio.com/wiki/images/3/3a/304090065.pdf (http://www.seeedstudio.com/wiki/images/0/08/304050003.pdf) | 0.339 | 10 | 4 | 0.40 |  | http://www.seeedstudio.com/depot/OPLopen-parts-library-catalog-c-136_138/#304090065
304090045 | 19-217-BHC-ZL1M2RY-3T | SMD LED Clear-Blue | LED | 0603 | Everlight | http://www.seeedstudio.com/wiki/images/1/1b/0330060P1.pdf (http://www.seeedstudio.com/wiki/images/2/20/304020016.pdf) | 0.031 | 50 | 2 | 0.20 |  | http://www.seeedstudio.com/depot/OPLopen-parts-library-catalog-c-136_138/#0330060P1
304090075 | BL-HB337A-AV-TRB | SMD LED Clear-Blue | LED | 0402 | Bright | http://www.seeedstudio.com/wiki/images/a/a0/304090075.pdf (http://www.seeedstudio.com/wiki/images/e/ed/304020028.pdf) | 0.066 | 25 | 2 | 0.20 |  | http://www.seeedstudio.com/depot/OPLopen-parts-library-catalog-c-136_138/#304090075
304090062 | 504BW | DIP LED Blue-Blue | LED | Radial-2P-2.54-5mm |  | http://www.seeedstudio.com/wiki/images/b/ba/304020034.pdf | 0.073 | 30 | 2 | 0.20 |  | http://www.seeedstudio.com/depot/OPLopen-parts-library-catalog-c-136_138/#304090062
304090016 | 16-219A/T2D-AR2T1QY/3T | SMD LED Yellow-Diffused-Pure White | LED | 0402 | Everlight | http://www.seeedstudio.com/wiki/images/7/72/304090016.pdf (http://www.seeedstudio.com/wiki/File:0310130P1.pdf) | 0.102 | 25 | 2 | 0.20 |  | http://www.seeedstudio.com/depot/OPLopen-parts-library-catalog-c-136_138/#304090016
304090058 | 504WC | DIP LED Transparent-White | LED | Radial-2P-2.54-5mm | Chengguangxing | http://www.seeedstudio.com/wiki/images/5/55/304090058.pdf | 0.059 | 30 | 2 | 0.20 |  | http://www.seeedstudio.com/depot/OPLopen-parts-library-catalog-c-136_138/#304090058
304060001 | CESD5V0D1 | SMD Diode ESD 6.2V-250mW | Diode | SOD-123 | JCET | http://www.seeedstudio.com/wiki/images/4/4d/304060001.pdf (http://www.seeedstudio.com/wiki/images/f/ff/307010010.pdf) | 0.039 | 50 | 2 | 0.20 |  | http://www.seeedstudio.com/depot/OPLopen-parts-library-catalog-c-136_138/#304060001
304010008 | 1N4004 | DIP Diode Rectifier 400V-1A | Diode | DO-41 | MIC |  | 0.015 | 100 | 2 | 0.20 |  | http://www.seeedstudio.com/depot/OPLopen-parts-library-catalog-c-136_138/#304010008
304040011 | LL4148ST | SMD Diode Switching 75V-200mA | Diode | LL-34 | ST | http://www.seeedstudio.com/wiki/images/7/7f/1030060P1.pdf | 0.011 | 100 | 2 | 0.20 |  | http://www.seeedstudio.com/depot/OPLopen-parts-library-catalog-c-136_138/#304040011
304050003 | CESD5V0AP | SMD Diode TVS 5V-225mW | Diode | SOT-23 | JCET | http://www.seeedstudio.com/wiki/images/0/08/304050003.pdf | 0.072 | 25 | 3 | 0.30 |  | http://www.seeedstudio.com/depot/OPLopen-parts-library-catalog-c-136_138/#304050003
304020028 | MBR0520LT1G | SMD Diode Schottky 20V-500mA | Diode | SOD-123 | ON Semiconductor | http://www.seeedstudio.com/wiki/images/e/ed/304020028.pdf | 0.066 | 25 | 2 | 0.20 |  | http://www.seeedstudio.com/depot/OPLopen-parts-library-catalog-c-136_138/#304020028
304020034 | B5819W | SMD Diode Schottky 20V-1A | Diode | SOD-123 | Micro Commercial Components | http://www.seeedstudio.com/wiki/images/b/ba/304020034.pdf (http://www.seeedstudio.com/wiki/images/4/42/310010023.pdf) | 0.053 | 25 | 2 | 0.20 |  | http://www.seeedstudio.com/depot/OPLopen-parts-library-catalog-c-136_138/#304020034
304020027 | 1N5819 | SMD Diode Schottky 40V-1A | Diode | DO-214AC |  | http://www.seeedstudio.com/wiki/images/4/45/0300070P1.pdf (http://www.seeedstudio.com/wiki/images/c/c1/310010053.pdf) | 0.028 | 50 | 2 | 0.20 |  | http://www.seeedstudio.com/depot/OPLopen-parts-library-catalog-c-136_138/#0300070P1
304020021 | SS54B | SMD Diode Schottky 28V-5A | Diode | SMB | JCET | http://www.seeedstudio.com/wiki/File:0310130P1.pdf (http://www.seeedstudio.com/wiki/images/0/0b/310030121.pdf) | 0.293 | 10 | 2 | 0.20 |  | http://www.seeedstudio.com/depot/OPLopen-parts-library-catalog-c-136_138/#0310130P1
304010013 | 1N4007 | SMD Diode Rectifier 1KV-1A | Diode | DO-214AC | JCET | http://www.seeedstudio.com/wiki/images/2/24/0300040P1.PDF (http://www.seeedstudio.com/wiki/images/6/69/310030009.pdf) | 0.020 | 100 | 2 | 0.20 |  | http://www.seeedstudio.com/depot/OPLopen-parts-library-catalog-c-136_138/#0300040P1
304040016 | 1N4148 | SMD Diode Switching 53V-300mA | Diode | LL-34 | JCET | http://www.seeedstudio.com/wiki/images/6/67/0300060P1.pdf | 0.011 | 100 | 2 | 0.20 |  | http://www.seeedstudio.com/depot/OPLopen-parts-library-catalog-c-136_138/#0300060P1
304020032 | SS0520-7-F | SMD Diode Schottky 20V-500mA | Diode | SOD-123 |  | http://www.seeedstudio.com/wiki/images/b/bb/0390030P1.pdf | 0.123 | 20 | 2 | 0.20 |  | http://www.seeedstudio.com/depot/OPLopen-parts-library-catalog-c-136_138/#0390030P1
307010001 | KT8-1000SMD1206 | SMD PPTC 1A-15V | Fuse | 1206 | TIANRUI | http://www.seeedstudio.com/wiki/images/0/0c/0900020P1.pdf (http://www.seeedstudio.com/wiki/images/d/d3/1310480P1.pdf) | 0.102 | 20 | 2 | 0.20 |  | http://www.seeedstudio.com/depot/OPLopen-parts-library-catalog-c-136_138/#0900020P1
307010013 | KT13-0750SMD | SMD PPTC 750mA-13.2V | Fuse | 1206 | Bourns | http://www.seeedstudio.com/wiki/images/3/30/307010013.pdf (http://www.seeedstudio.com/wiki/images/a/a7/310030006.pdf) | 0.109 | 10 | 2 | 0.20 |  | http://www.seeedstudio.com/depot/OPLopen-parts-library-catalog-c-136_138/#307010013
307010002 |  | SMD PPTC 750mA-16V | Fuse | 1206 | TIANRUI | http://www.seeedstudio.com/wiki/images/5/51/0900030P1.pdf (http://www.seeedstudio.com/wiki/images/9/99/1310170P1.pdf) | 0.113 | 20 | 2 | 0.20 |  | http://www.seeedstudio.com/depot/OPLopen-parts-library-catalog-c-136_138/#0900030P1
310010049 | ATMEGA328P-AU | SMD IC MCU;AVR;8-Bit;32KB;16MHz;1.8-5.5V | IC | 32-TQFP | Atmel | http://www.seeedstudio.com/wiki/images/7/7f/1030060P1.pdf | 2.500 | 1 | 32 | 3.20 |  | http://www.seeedstudio.com/depot/OPLopen-parts-library-catalog-c-136_138/#1030060P1
310010051 | ATMEGA328P-PU | DIP IC MCU;AVR;8-Bit;32KB;16MHz;1.8-5.5V | IC | 28-DIP | Atmel | http://www.seeedstudio.com/wiki/images/0/0e/1030050P1.pdf | 3.000 | 1 | 28 | 2.80 |  | http://www.seeedstudio.com/depot/OPLopen-parts-library-catalog-c-136_138/#1030050P1
310010010 | ATMEGA32U4-AU | SMD IC MCU;AVR;USB;8-Bit;32KB;16MHz;1.8-5.5V | IC | TQFP-44 | Atmel | http://www.seeedstudio.com/wiki/images/f/f7/310010010.pdf (http://www.seeedstudio.com/wiki/File:1320040P1.pdf) | 5.400 | 1 | 10 | 1.00 |  | http://www.seeedstudio.com/depot/OPLopen-parts-library-catalog-c-136_138/#310010010
310010006 | ATMEGA2560-16AU | SMD IC MCU;AVR;8-Bit;256KB;16MHz;1.8-5.5V | IC | TQFP-100 | Atmel | http://www.seeedstudio.com/wiki/images/e/e3/310010006.pdf | 12.000 | 1 | 25 | 2.50 |  | http://www.seeedstudio.com/depot/OPLopen-parts-library-catalog-c-136_138/#310010006
310010053 | LPC11U35FHI33/501 | SMD IC MCU;ARM MCU 32Bit;Cortex-M0 64KB;3.3V | IC | HVQFN-32 | NXP | http://www.seeedstudio.com/wiki/images/c/c1/310010053.pdf (http://www.seeedstudio.com/wiki/images/0/04/310050042.pdf) | 4.000 | 1 | 10 | 1.00 |  | http://www.seeedstudio.com/depot/OPLopen-parts-library-catalog-c-136_138/#310010053
310030121 | MP1496DJ | SMD PMIC;DC-DC;Vin 4.5-16V;Adj;2A;500K;N-Sync;Buck;1-Ch | IC | TSOT23-8 | Monolithic Power Systems | http://www.seeedstudio.com/wiki/images/0/0b/310030121.pdf (http://www.seeedstudio.com/wiki/images/9/93/310040002.pdf) | 0.500 | 5 | 8 | 0.80 |  | http://www.seeedstudio.com/depot/OPLopen-parts-library-catalog-c-136_138/#310030121
310030009 | XC6206P302MR | SMD PMIC;LDO;Vin 6V;3.0V;200mA;Without En;1-Ch | IC | SOT-23 | Torex | http://www.seeedstudio.com/wiki/images/6/69/310030009.pdf (http://www.seeedstudio.com/wiki/images/4/4d/310040021.pdf) | 0.150 | 10 | 3 | 0.30 |  | http://www.seeedstudio.com/depot/OPLopen-parts-library-catalog-c-136_138/#310030009
310030014 | XC6206P252MR-G | SMD PMIC;LDO;Vin 6V;2.5V;200mA;Without En;1-Ch | IC | SOT-23 | Torex | http://www.seeedstudio.com/wiki/images/6/69/310030009.pdf | 0.150 | 10 | 3 | 0.30 |  | http://www.seeedstudio.com/depot/OPLopen-parts-library-catalog-c-136_138/#310030014
310030099 | XC6206P332MR-G | SMD PMIC;LDO;Vin 6V;3.3V;200mA;Without En;1-Ch | IC | SOT-23 | TOREX | http://www.seeedstudio.com/wiki/images/7/71/1300260P1.pdf | 0.120 | 20 | 3 | 0.30 |  | http://www.seeedstudio.com/depot/OPLopen-parts-library-catalog-c-136_138/#1300260P1
310030046 | XC6204B332MR | SMD PMIC;LDO;Vin 10V;3.3V;150mA;With En;1-Ch | IC | SOT-25 | Torex Semiconductor Ltd | http://www.seeedstudio.com/wiki/images/d/d3/1310480P1.pdf | 0.160 | 10 | 5 | 0.50 |  | http://www.seeedstudio.com/depot/OPLopen-parts-library-catalog-c-136_138/#131048001
310030148 | ETA3406S2F-T | SMD PMIC;DC-DC;Vin 2.6-6V;Adj;1.2A;1.5M;Sync;Buck;1-Ch | IC | SOT23-5 | ETA solution | http://www.seeedstudio.com/wiki/images/4/4f/310030148.pdf (http://www.seeedstudio.com/wiki/images/f/f4/310020016.pdf) | 0.150 | 10 | 5 | 0.50 |  | http://www.seeedstudio.com/depot/OPLopen-parts-library-catalog-c-136_138/#310030148
310030104 | AIC1896GG | SMD PMIC;DC-DC;Vin 2.5-10V;Adj;200mA;1.4M;Boost;1-Ch | IC | SOT23-6 | AIC | http://www.seeedstudio.com/wiki/images/c/ca/310020015.pdf | 0.500 | 3 | 3 | 0.30 |  | http://www.seeedstudio.com/depot/OPLopen-parts-library-catalog-c-136_138/#310030104
310030096 | CJT1117-5.0 | SMD PMIC; LDO;Vin 7V;5V;1A;Without En;1-Ch | IC | SOT-223 | JCET | http://www.seeedstudio.com/wiki/images/9/99/1310170P1.pdf (http://www.seeedstudio.com/wiki/images/1/15/310070024.pdf) | 0.150 | 10 | 4 | 0.40 |  | http://www.seeedstudio.com/depot/OPLopen-parts-library-catalog-c-136_138/#1310170P1
310030097 | CJT1117-3.3 | SMD PMIC; LDO;Vin 5V;3.3V;1A;Without En;1-Ch | IC | SOT-223 | JCET | http://www.seeedstudio.com/wiki/images/a/a5/1310190P1.pdf (http://www.seeedstudio.com/wiki/images/c/ca/310070025.pdf) | 0.150 | 10 | 4 | 0.40 |  | http://www.seeedstudio.com/depot/OPLopen-parts-library-catalog-c-136_138/#1310190P1
310030095 | CJA1117B-3.3 | SMD PMIC; LDO;Vin 5.3V;3.3V;1A;Without En;1-Ch | IC | SOT-89 | JCET | http://www.seeedstudio.com/wiki/images/b/b9/1310120P1.pdf (http://www.seeedstudio.com/wiki/images/4/46/1720010P1.pdf) | 0.150 | 10 | 4 | 0.40 |  | http://www.seeedstudio.com/depot/OPLopen-parts-library-catalog-c-136_138/#1310120P1
310030101 | CN3065 | SMD PMIC;Liner;Li-Ion/Pol;Charge;4.2V;1-cell | IC | 8-DFN | CONSONANCE | http://www.seeedstudio.com/wiki/File:1320040P1.pdf | 0.700 | 3 | 16 | 1.60 |  | http://www.seeedstudio.com/depot/OPLopen-parts-library-catalog-c-136_138/#1320040P1
310030100 | CJ78M05 | SMD PMIC;LDO;Vin 25V;5V;0.5A;Without En;1-Ch | IC | TO-252 | JCET | http://www.seeedstudio.com/wiki/images/a/a7/1300040P1.pdf (http://www.seeedstudio.com/wiki/images/1/1d/310110008.pdf) | 0.150 | 10 | 3 | 0.30 |  | http://www.seeedstudio.com/depot/OPLopen-parts-library-catalog-c-136_138/#1300040P1
310050042 | 74VHC125MTCX | SMD IC Logic;4-bit CMOS Buffer;VCC 2V-6V | IC | TSSOP-14 | Fairchild | http://www.seeedstudio.com/wiki/images/0/04/310050042.pdf | 0.200 | 10 | 5 | 0.50 |  | http://www.seeedstudio.com/depot/OPLopen-parts-library-catalog-c-136_138/#310050042
310040018 | L298P | SMD IC Driver;Motor Driver;2-CH;VM≤46V;Imout 4A;VC 1.5V-7V | IC | PowerSO-20 | ST | http://www.seeedstudio.com/wiki/images/6/66/310040018.pdf (http://www.seeedstudio.com/wiki/images/d/d4/315030000.pdf) | 5.000 | 1 | 10 | 1.00 |  | http://www.seeedstudio.com/depot/OPLopen-parts-library-catalog-c-136_138/#310040018
310020021 | LM358DR | SMD IC Amplifier;2-CH;GBW 1MHz;Io 30mA;3V-32V;±1V-18V | IC | 8-SOIC | Texas Instruments | http://www.seeedstudio.com/wiki/images/1/1a/1110010P1.pdf (http://www.seeedstudio.com/wiki/images/0/06/301010000.pdf) | 0.160 | 20 | 8 | 0.80 |  | http://www.seeedstudio.com/depot/OPLopen-parts-library-catalog-c-136_138/#1110010P1
310020002 | LMV358ID | SMD IC Amplifier;DUAL;1MHz;2.7 V-5.5 V | IC | SOIC-8 | TI | http://www.seeedstudio.com/wiki/images/e/e3/310020002.pdf (http://www.seeedstudio.com/wiki/images/0/06/301010000.pdf) | 0.250 | 10 | 3 | 0.30 |  | http://www.seeedstudio.com/depot/OPLopen-parts-library-catalog-c-136_138/#310020002
310020016 | LM293D | SMD IC Amplifier;2-CH;2V-36V;±1V-18V | IC | SOIC-8 | TI | http://www.seeedstudio.com/wiki/images/f/f4/310020016.pdf (http://www.seeedstudio.com/wiki/images/2/28/301010113.pdf) | 0.180 | 10 | 3 | 0.30 |  | http://www.seeedstudio.com/depot/OPLopen-parts-library-catalog-c-136_138/#310020016
310020015 | LM2904DR | SMD IC Amplifier;2-CH;GPW 0.7MHz;Io 30mA;3V-26V;±1.5V-13V | IC | SOIC-8 | TI | http://www.seeedstudio.com/wiki/images/c/ca/310020015.pdf (http://www.seeedstudio.com/wiki/images/2/28/301010113.pdf) | 0.230 | 10 | 3 | 0.30 |  | http://www.seeedstudio.com/depot/OPLopen-parts-library-catalog-c-136_138/#310020015
310070022 | FT232RL | SMD IC Interface;USB to UART;Speed 300b-3Mbaud;VCC 1.8V-5.25V | IC | 28-SSOP | FTDI | http://www.seeedstudio.com/wiki/images/4/46/1720010P1.pdf | 3.500 | 1 | 28 | 2.80 |  | http://www.seeedstudio.com/depot/OPLopen-parts-library-catalog-c-136_138/#1720010P1
303010016 | CSAB0630-100M | SMD Inductor 10uH-20%-5A | Inductor | SMD-2P-L6.0*W6.0*H3.0mm | CODACA | http://www.seeedstudio.com/wiki/images/8/81/303010016.pdf (http://www.seeedstudio.com/wiki/images/6/63/PYu-RC0805_51_RoHS_L_v5.pdf) | 0.447 | 5 | 2 | 0.20 |  | http://www.seeedstudio.com/depot/OPLopen-parts-library-catalog-c-136_138/#303010016
303030001 | BLM18AG121SN1D | SMD FERRITE CHIP 120R 500mA | Inductor | 0603 | Murata | http://www.seeedstudio.com/wiki/images/e/ea/0900120P1.pdf | 0.016 | 100 | 2 | 0.20 |  | http://www.seeedstudio.com/depot/OPLopen-parts-library-catalog-c-136_138/#0900120P1
315030000 | HLS8L-DC5V-S-C | DIP Power Relay 5V-7A | Relay | 5P-L19.0*W15.0*H15.0mm | HELISHUN | http://www.seeedstudio.com/wiki/images/d/d4/315030000.pdf (http://www.seeedstudio.com/wiki/images/6/63/PYu-RC0805_51_RoHS_L_v5.pdf) | 0.547 | 5 | 8 | 0.80 |  | http://www.seeedstudio.com/depot/OPLopen-parts-library-catalog-c-136_138/#315030000
301010292 | RC0603JR-070RL | SMD RES 0R-5%-1/10W | Resistor | 0603 | YAGEO | http://www.seeedstudio.com/wiki/images/0/01/0010070P1.pdf | 0.010 | 100 | 2 | 0.20 |  | http://www.seeedstudio.com/depot/OPLopen-parts-library-catalog-c-136_138/#0010070P1
301010000 | RC0402JR-070RL | SMD RES 0R-5%-1/16W | Resistor | 0402 | YAGEO | http://www.seeedstudio.com/wiki/images/0/06/301010000.pdf | 0.010 | 100 | 2 | 0.20 |  | http://www.seeedstudio.com/depot/OPLopen-parts-library-catalog-c-136_138/#301010000
301010096 | RC0603JR-0710RL | SMD RES 10R-5%-1/10W | Resistor | 0603 | YAGEO | http://www.seeedstudio.com/wiki/images/2/28/301010113.pdf (http://www.seeedstudio.com/wiki/images/6/63/PYu-RC0805_51_RoHS_L_v5.pdf) | 0.010 | 50 | 2 | 0.20 |  | http://www.seeedstudio.com/depot/OPLopen-parts-library-catalog-c-136_138/#301010096
301010185 | RC0603FR-0710RL | SMD RES 10R-1%-1/10W | Resistor | 0603 | YAGEO | http://www.seeedstudio.com/wiki/images/2/28/301010113.pdf | 0.010 | 100 | 2 | 0.20 |  | http://www.seeedstudio.com/depot/OPLopen-parts-library-catalog-c-136_138/#301010185
301010405 | RC1206JR-0713RL | SMD RES 13R-5%-1/4W | Resistor | 1206 | YAGEO | http://www.seeedstudio.com/wiki/images/6/67/301010405.pdf | 0.010 | 100 | 2 | 0.20 |  | http://www.seeedstudio.com/depot/OPLopen-parts-library-catalog-c-136_138/#301010405
301010289 | RC0603JR-0722RL | SMD RES 22R-5%-1/10W | Resistor | 0603 | YAGEO | http://www.seeedstudio.com/wiki/images/9/99/0010010P1.pdf | 0.010 | 100 | 2 | 0.20 |  | http://www.seeedstudio.com/depot/OPLopen-parts-library-catalog-c-136_138/#0010010P1
301010329 | RC0805JR-0722RL | SMD RES 22R-5%-1/8W | Resistor | 0805 | YAGEO | http://www.seeedstudio.com/wiki/images/6/63/PYu-RC0805_51_RoHS_L_v5.pdf | 0.010 | 100 | 2 | 0.20 |  | http://www.seeedstudio.com/depot/OPLopen-parts-library-catalog-c-136_138/#301010329
301010296 | RC0603FR-0749R9L | SMD RES 49.9R-1%-1/10W | Resistor | 0603 | YAGEO | http://www.seeedstudio.com/wiki/images/5/56/001057001.pdf (http://www.seeedstudio.com/wiki/images/2/28/301010113.pdf) | 0.010 | 100 | 2 | 0.20 |  | http://www.seeedstudio.com/depot/OPLopen-parts-library-catalog-c-136_138/#0010570P1
301010412 | RC1206JR-07100RL | SMD RES 100R-5%-1/4W | Resistor | 1206 | YAGEO | http://www.seeedstudio.com/wiki/images/f/f8/0030110P1.pdf (http://www.seeedstudio.com/wiki/images/0/06/301010000.pdf) | 0.010 | 100 | 2 | 0.20 |  | http://www.seeedstudio.com/depot/OPLopen-parts-library-catalog-c-136_138/#0030110P1
301010319 | RC0805JR-07100RL | SMD RES 100R-5%-1/8W | Resistor | 0805 | YAGEO | http://www.seeedstudio.com/wiki/images/6/63/PYu-RC0805_51_RoHS_L_v5.pdf (http://www.seeedstudio.com/wiki/images/3/38/301030012.pdf) | 0.010 | 100 | 2 | 0.20 |  | http://www.seeedstudio.com/depot/OPLopen-parts-library-catalog-c-136_138/#301010319
301010090 | RC0603JR-07100RL | SMD RES 100R-5%-1/10W | Resistor | 0603 | YAGEO | http://www.seeedstudio.com/wiki/images/a/a6/301040009.pdf | 0.010 | 100 | 2 | 0.20 |  | http://www.seeedstudio.com/depot/OPLopen-parts-library-catalog-c-136_138/#301010090
301010028 | RC0402JR-07100RL | SMD RES 100R-5%-1/16W | Resistor | 0402 | YAGEO | http://www.seeedstudio.com/wiki/images/0/06/301010000.pdf (http://www.seeedstudio.com/wiki/images/2/28/301010113.pdf) | 0.010 | 100 | 2 | 0.20 |  | http://www.seeedstudio.com/depot/OPLopen-parts-library-catalog-c-136_138/#301010028
301010315 | RC0805JR-07220RL | SMD RES 220R-5%-1/8W | Resistor | 0805 | YAGEO | http://www.seeedstudio.com/wiki/images/6/63/PYu-RC0805_51_RoHS_L_v5.pdf | 0.010 | 100 | 2 | 0.20 |  | http://www.seeedstudio.com/depot/OPLopen-parts-library-catalog-c-136_138/#301010315
301010163 | RC0603JR-07220RL | SMD RES 220R-5%-1/10W | Resistor | 0603 | YAGEO | http://www.seeedstudio.com/wiki/images/2/28/301010113.pdf | 0.010 | 100 | 2 | 0.20 |  | http://www.seeedstudio.com/depot/OPLopen-parts-library-catalog-c-136_138/#301010163
301010300 | RC0603FR-07330RL | SMD RES 330R-1%-1/10W | Resistor | 0603 | YAGEO | http://www.seeedstudio.com/wiki/images/0/03/001133001.pdf (http://www.seeedstudio.com/wiki/images/6/63/PYu-RC0805_51_RoHS_L_v5.pdf) | 0.010 | 100 | 2 | 0.20 |  | http://www.seeedstudio.com/depot/OPLopen-parts-library-catalog-c-136_138/#0011330P1
301010297 | RC0603JR-07390RL | SMD RES 390R-5%-1/10W | Resistor | 0603 | YAGEO | http://www.seeedstudio.com/wiki/images/2/23/001060001.pdf (http://www.seeedstudio.com/wiki/images/6/63/PYu-RC0805_51_RoHS_L_v5.pdf) | 0.010 | 100 | 2 | 0.20 |  | http://www.seeedstudio.com/depot/OPLopen-parts-library-catalog-c-136_138/#0010600P1
301010088 | RC0603JR-07470RL | SMD RES 470R-5%-1/10W;0603 | Resistor | 0603 | YAGEO | http://www.seeedstudio.com/wiki/images/6/63/PYu-RC0805_51_RoHS_L_v5.pdf | 0.010 | 100 | 2 | 0.20 |  | http://www.seeedstudio.com/depot/OPLopen-parts-library-catalog-c-136_138/#301010088
301010157 | RC0603JR-07510RL | SMD RES 510R-5%-1/10W | Resistor | 0603 | YAGEO | http://www.seeedstudio.com/wiki/images/2/28/301010113.pdf | 0.010 | 50 | 2 | 0.20 |  | http://www.seeedstudio.com/depot/OPLopen-parts-library-catalog-c-136_138/#301010157
301010210 | RC0603JR-07620RL | SMD RES 620R-5%-1/10W | Resistor | 0603 | YAGEO | http://www.seeedstudio.com/wiki/images/2/28/301010113.pdf (http://www.seeedstudio.com/wiki/images/6/63/PYu-RC0805_51_RoHS_L_v5.pdf) | 0.010 | 50 | 2 | 0.20 |  | http://www.seeedstudio.com/depot/OPLopen-parts-library-catalog-c-136_138/#301010210
301010311 | RC0805JR-071KL | SMD RES 1K-5%-1/8W | Resistor | 0805 | YAGEO | http://www.seeedstudio.com/wiki/images/6/63/PYu-RC0805_51_RoHS_L_v5.pdf (http://www.seeedstudio.com/wiki/images/2/28/301010113.pdf) | 0.010 | 100 | 2 | 0.20 |  | http://www.seeedstudio.com/depot/OPLopen-parts-library-catalog-c-136_138/#301010311
301010298 | RC0603FR-071KL | SMD RES 1K-1%-1/10W | Resistor | 0603 | YAGEO | http://www.seeedstudio.com/wiki/images/c/c7/001109001.pdf (http://www.seeedstudio.com/wiki/images/0/06/301010000.pdf) | 0.010 | 100 | 2 | 0.20 |  | http://www.seeedstudio.com/depot/OPLopen-parts-library-catalog-c-136_138/#0011090P1
301010006 | RC0402JR-071KL | SMD RES 1K-5%-1/16W | Resistor | 0402 | YAGEO | http://www.seeedstudio.com/wiki/images/0/06/301010000.pdf | 0.010 | 100 | 2 | 0.20 |  | http://www.seeedstudio.com/depot/OPLopen-parts-library-catalog-c-136_138/#301010006
301030012 | Chip Array Series 1%,5% | SMD RES Array 1k-4R | Resistor | 1206-8 | Royalohm | http://www.seeedstudio.com/wiki/images/3/38/301030012.pdf | 0.010 | 100 | 2 | 0.20 |  | http://www.seeedstudio.com/depot/OPLopen-parts-library-catalog-c-136_138/#301030012
301040014 | SX3362P | DIP VR Top Adj 1K-3362P | Resistor | 3P-L7.0*W7.0*H5.0mm | BEST | http://www.seeedstudio.com/wiki/images/a/a6/301040009.pdf (http://www.seeedstudio.com/wiki/images/6/63/PYu-RC0805_51_RoHS_L_v5.pdf) | 0.254 | 5 | 3 | 0.30 |  | http://www.seeedstudio.com/depot/OPLopen-parts-library-catalog-c-136_138/#301040014
301010189 | RC0603FR-071K5L | SMD RES 1.5K-1%-1/10W | Resistor | 0603 | YAGEO | http://www.seeedstudio.com/wiki/images/2/28/301010113.pdf (http://www.seeedstudio.com/wiki/images/6/63/PYu-RC0805_51_RoHS_L_v5.pdf) | 0.010 | 100 | 2 | 0.20 |  | http://www.seeedstudio.com/depot/OPLopen-parts-library-catalog-c-136_138/#301010189
301010254 | RC0603FR-071K8L | SMD RES 1.8K-1%-1/10W | Resistor | 0603 | YAGEO | http://www.seeedstudio.com/wiki/images/2/28/301010113.pdf (http://www.seeedstudio.com/wiki/images/0/06/301010000.pdf) | 0.010 | 100 | 2 | 0.20 |  | http://www.seeedstudio.com/depot/OPLopen-parts-library-catalog-c-136_138/#301010254
301010318 | RC0805JR-072KL | SMD RES 2K-5%-1/8W | Resistor | 0805 | YAGEO | http://www.seeedstudio.com/wiki/images/6/63/PYu-RC0805_51_RoHS_L_v5.pdf | 0.010 | 100 | 2 | 0.20 |  | http://www.seeedstudio.com/depot/OPLopen-parts-library-catalog-c-136_138/#301010318
301010333 | RC0805JR-072K2L | SMD RES 2.2K-5%-1/8W | Resistor | 0805 | YAGEO | http://www.seeedstudio.com/wiki/images/6/63/PYu-RC0805_51_RoHS_L_v5.pdf (http://www.seeedstudio.com/wiki/images/a/a6/301040009.pdf) | 0.010 | 100 | 2 | 0.20 |  | http://www.seeedstudio.com/depot/OPLopen-parts-library-catalog-c-136_138/#301010333
301010170 | RC0603FR-073KL | SMD RES 3K-1%-1/10W | Resistor | 0603 | YAGEO | http://www.seeedstudio.com/wiki/images/2/28/301010113.pdf | 0.010 | 100 | 2 | 0.20 |  | http://www.seeedstudio.com/depot/OPLopen-parts-library-catalog-c-136_138/#301010170
301010251 | RC0603FR-073K3L | SMD RES 3.3K-1%-1/10W;0603 | Resistor | 0603 | YAGEO | http://www.seeedstudio.com/wiki/images/2/28/301010113.pdf (http://www.seeedstudio.com/wiki/images/6/63/PYu-RC0805_51_RoHS_L_v5.pdf) | 0.010 | 100 | 2 | 0.20 |  | http://www.seeedstudio.com/depot/OPLopen-parts-library-catalog-c-136_138/#301010251
301010035 | RC0402JR-073K3L | SMD RES 3.3K-5%-1/16W | Resistor | 0402 | YAGEO | http://www.seeedstudio.com/wiki/images/0/06/301010000.pdf (http://www.seeedstudio.com/wiki/images/2/28/301010113.pdf) | 0.010 | 100 | 2 | 0.20 |  | http://www.seeedstudio.com/depot/OPLopen-parts-library-catalog-c-136_138/#301010035
301010101 | RC0603JR-073K9L | SMD RES 3.9K-5%-1/10W; | Resistor | 0603 | YAGEO | http://www.seeedstudio.com/wiki/images/2/28/301010113.pdf | 0.010 | 100 | 2 | 0.20 |  | http://www.seeedstudio.com/depot/OPLopen-parts-library-catalog-c-136_138/#301010101
301010290 | RC0603JR-074K7L | SMD RES 4.7K-5%-1/10W | Resistor | 0603 | YAGEO | http://www.seeedstudio.com/wiki/images/c/ce/0010030P1.pdf (http://www.seeedstudio.com/wiki/images/2/28/301010113.pdf) | 0.010 | 100 | 2 | 0.20 |  | http://www.seeedstudio.com/depot/OPLopen-parts-library-catalog-c-136_138/#0010030P1
301010306 | RC0805JR-074K7L | SMD RES 4.7K-5%-1/8W | Resistor | 0805 | YAGEO | http://www.seeedstudio.com/wiki/images/6/63/PYu-RC0805_51_RoHS_L_v5.pdf | 0.010 | 100 | 2 | 0.20 |  | http://www.seeedstudio.com/depot/OPLopen-parts-library-catalog-c-136_138/#301010306
301010361 | RC0805FR-0710KL | SMD RES 10K-1%-1/8W | Resistor | 0805 | YAGEO | http://www.seeedstudio.com/wiki/images/6/63/PYu-RC0805_51_RoHS_L_v5.pdf | 0.010 | 100 | 2 | 0.20 |  | http://www.seeedstudio.com/depot/OPLopen-parts-library-catalog-c-136_138/#301010361
301010299 | RC0603FR-0710KL | SMD RES 10K-1%-1/10W | Resistor | 0603 | YAGEO | http://www.seeedstudio.com/wiki/images/a/ad/001124001.pdf | 0.010 | 100 | 2 | 0.20 |  | http://www.seeedstudio.com/depot/OPLopen-parts-library-catalog-c-136_138/#0011240P1
301010004 | RC0402JR-0710KL | SMD RES 10K-5%-1/16W | Resistor | 0402 | YAGEO | http://www.seeedstudio.com/wiki/images/0/06/301010000.pdf (http://www.seeedstudio.com/wiki/images/2/28/301010113.pdf) | 0.010 | 100 | 2 | 0.20 |  | http://www.seeedstudio.com/depot/OPLopen-parts-library-catalog-c-136_138/#301010004
301040009 | SX3362P | DIP VR Top Adj 10K-3362P | Resistor | 3P-L7.0*W7.0*H5.0mm | BEST | http://www.seeedstudio.com/wiki/images/a/a6/301040009.pdf (http://www.seeedstudio.com/wiki/images/2/28/301010113.pdf) | 0.246 | 5 | 3 | 0.30 |  | http://www.seeedstudio.com/depot/OPLopen-parts-library-catalog-c-136_138/#301040009
301010102 | RC0603FR-0712KL | SMD RES 12K-1%-1/10W | Resistor | 0603 | YAGEO | http://www.seeedstudio.com/wiki/images/2/28/301010113.pdf | 0.010 | 100 | 2 | 0.20 |  | http://www.seeedstudio.com/depot/OPLopen-parts-library-catalog-c-136_138/#301010102
301010103 | RC0603JR-0715KL | SMD RES 15K-5%-1/10W | Resistor | 0603 | YAGEO | http://www.seeedstudio.com/wiki/images/2/28/301010113.pdf (http://www.seeedstudio.com/wiki/images/a/a6/301040009.pdf) | 0.010 | 50 | 2 | 0.20 |  | http://www.seeedstudio.com/depot/OPLopen-parts-library-catalog-c-136_138/#301010103
301010288 | RC0603FR-0720KL | SMD RES 20K-1%-1/10W | Resistor | 0603 | YAGEO | http://www.seeedstudio.com/wiki/images/2/28/301010113.pdf | 0.010 | 100 | 2 | 0.20 |  | http://www.seeedstudio.com/depot/OPLopen-parts-library-catalog-c-136_138/#301010288
301010132 | RC0603JR-0722KL | SMD RES 22K-5%-1/10W | Resistor | 0603 | YAGEO | http://www.seeedstudio.com/wiki/images/2/28/301010113.pdf (http://www.seeedstudio.com/wiki/images/f/f5/301040037.pdf) | 0.010 | 50 | 2 | 0.20 |  | http://www.seeedstudio.com/depot/OPLopen-parts-library-catalog-c-136_138/#301010132
301010202 | RC0603FR-0730KL | SMD RES 30K-1%-1/10W | Resistor | 0603 | YAGEO | http://www.seeedstudio.com/wiki/images/2/28/301010113.pdf | 0.010 | 100 | 2 | 0.20 |  | http://www.seeedstudio.com/depot/OPLopen-parts-library-catalog-c-136_138/#301010202
301010084 | RC0603JR-0747KL | SMD RES 47K-5%-1/10W | Resistor | 0603 | YAGEO | http://www.seeedstudio.com/wiki/images/2/28/301010113.pdf | 0.010 | 100 | 2 | 0.20 |  | http://www.seeedstudio.com/depot/OPLopen-parts-library-catalog-c-136_138/#301010084
301010145 | RC0603JR-0751KL | SMD RES 51K-5%-1/10W | Resistor | 0603 | YAGEO | http://www.seeedstudio.com/wiki/images/2/28/301010113.pdf | 0.010 | 50 | 2 | 0.20 |  | http://www.seeedstudio.com/depot/OPLopen-parts-library-catalog-c-136_138/#301010145
301010169 | RC0603FR-0768KL | SMD RES 68K-1%-1/10W | Resistor | 0603 | YAGEO | http://www.seeedstudio.com/wiki/images/2/28/301010113.pdf | 0.010 | 100 | 2 | 0.20 |  | http://www.seeedstudio.com/depot/OPLopen-parts-library-catalog-c-136_138/#301010169
301010196 | RC0603FR-07100KL | SMD RES 100K-1%-1/10W;0603 | Resistor | 0603 | YAGEO | http://www.seeedstudio.com/wiki/images/2/28/301010113.pdf | 0.010 | 100 | 2 | 0.20 |  | http://www.seeedstudio.com/depot/OPLopen-parts-library-catalog-c-136_138/#301010196
301010133 | RC0603JR-07150KL | SMD RES 150K-5%-1/10W | Resistor | 0603 | YAGEO | http://www.seeedstudio.com/wiki/images/2/28/301010113.pdf (http://www.seeedstudio.com/wiki/images/b/b4/314020024.pdf) | 0.010 | 50 | 2 | 0.20 |  | http://www.seeedstudio.com/depot/OPLopen-parts-library-catalog-c-136_138/#301010133
301010205 | RC0603FR-07150KL | SMD RES 150K-1%-1/10W;0603 | Resistor | 0603 | YAGEO | http://www.seeedstudio.com/wiki/images/2/28/301010113.pdf (http://www.seeedstudio.com/wiki/images/a/a8/314020023.pdf) | 0.010 | 100 | 2 | 0.20 |  | http://www.seeedstudio.com/depot/OPLopen-parts-library-catalog-c-136_138/#301010205
301010212 | RC0603JR-07200KL | SMD RES 200K-5%-1/10W;0603 | Resistor | 0603 | YAGEO | http://www.seeedstudio.com/wiki/images/2/28/301010113.pdf | 0.010 | 100 | 2 | 0.20 |  | http://www.seeedstudio.com/depot/OPLopen-parts-library-catalog-c-136_138/#301010212
301010151 | RC0603FR-071ML | SMD RES 1M-1%-1/10W;0603 | Resistor | 0603 | YAGEO | http://www.seeedstudio.com/wiki/images/2/28/301010113.pdf | 0.010 | 100 | 2 | 0.20 |  | http://www.seeedstudio.com/depot/OPLopen-parts-library-catalog-c-136_138/#301010151
301010154 | RC0603FR-072ML | SMD RES 2M-1%-1/10W;0603 | Resistor | 0603 | YAGEO | http://www.seeedstudio.com/wiki/images/2/28/301010113.pdf | 0.010 | 100 | 2 | 0.20 |  | http://www.seeedstudio.com/depot/OPLopen-parts-library-catalog-c-136_138/#301010154
301010213 | RC0603JR-074M7L | SMD RES 4.7M-5%-1/10W;0603 | Resistor | 0603 | YAGEO | http://www.seeedstudio.com/wiki/images/2/28/301010113.pdf | 0.010 | 100 | 2 | 0.20 |  | http://www.seeedstudio.com/depot/OPLopen-parts-library-catalog-c-136_138/#301010213
301010153 | RC0603FR-0710ML | SMD RES 10M-1%-1/10W;0603 | Resistor | 0603 | YAGEO | http://www.seeedstudio.com/wiki/images/2/28/301010113.pdf | 0.010 | 100 | 2 | 0.20 |  | http://www.seeedstudio.com/depot/OPLopen-parts-library-catalog-c-136_138/#301010153
314020017 | Photoresistor-5528 | DIP RES Photoresistor 10K;2P-3.0 | Sensor | 2P-3.0 | Keyue |  | 0.053 | 20 | 3 | 0.30 |  | http://www.seeedstudio.com/depot/OPLopen-parts-library-catalog-c-136_138/#314020017
314010001 | AM2302 | DIP Tem-Hum Sensor | Sensor | 4P-2.54 |  |  | 7.031 | 1 | 6 | 0.60 |  | http://www.seeedstudio.com/depot/OPLopen-parts-library-catalog-c-136_138/#314010001
314010000 | DHT11 | DIP Tem-Hum Sensor | Sensor | 4P-2.54-L15.5*W12.0*H5.5mm |  |  | 1.758 | 2 | 4 | 0.40 |  | http://www.seeedstudio.com/depot/OPLopen-parts-library-catalog-c-136_138/#314010000
314020022 | LTH1550-01 | DIP Optical Sensor | Sensor | 4P-L8.7*W4.5*H5.8mm | Lite-On Technology Corporation | http://www.seeedstudio.com/wiki/images/8/89/305010013.pdf | 0.594 | 3 | 6 | 0.60 |  | http://www.seeedstudio.com/depot/OPLopen-parts-library-catalog-c-136_138/#314020022
314020020 | TM2291 | SMD IC Sensor;PIR Motion Sensor processor;3V-5V | Sensor | SOP-16 | Titanmec | datasheet 是中文 (http://www.seeedstudio.com/wiki/images/1/1f/314080008.pdf) | 0.238 | 10 | 4 | 0.40 |  | http://www.seeedstudio.com/depot/OPLopen-parts-library-catalog-c-136_138/#314020020
314990002 | LHI778 | DIP PIR Motion Sensor | Sensor | 3P-D8.1X4.2Hmm | PreKinElmer | http://www.seeedstudio.com/wiki/images/6/66/314990002.pdf (http://www.seeedstudio.com/wiki/images/7/7f/310010001.pdf) | 1.182 | 2 | 3 | 0.30 |  | http://www.seeedstudio.com/depot/OPLopen-parts-library-catalog-c-136_138/#314990002
314110002 |  | DIP Thermistor-503;2P-2.54 | Resistor | 2P-2.54 | Shuoye |  | 0.058 | 20 | 3 | 0.30 |  | http://www.seeedstudio.com/depot/OPLopen-parts-library-catalog-c-136_138/#314110002
311030004 |  | DIP Toggle Switch;SPDT;200gf | Switch | 6P-2.54-L9.0*W3.5*H3.2mm |  |  | 0.153 | 20 | 6 | 0.60 |  | http://www.seeedstudio.com/depot/OPLopen-parts-library-catalog-c-136_138/#311030004
311030005 |  | SMD Switch ;SPDT;150gf | Switch | 6P-2.54-L7.0*W3.5*H1.5mm |  |  | 0.230 | 20 | 6 | 0.60 |  | http://www.seeedstudio.com/depot/OPLopen-parts-library-catalog-c-136_138/#311030005
311020025 | TS-1101F | DIP Button Side Plast;SPST;180gf | Switch | 2P-L6.0*W3.0*H4.3mm-90D | Baisite | http://www.seeedstudio.com/wiki/images/2/2c/311020025.pdf | 0.059 | 30 | 3 | 0.30 |  | http://www.seeedstudio.com/depot/OPLopen-parts-library-catalog-c-136_138/#311020025
311020023 | TS-1188E | SMD Button Side Plast;SPST;180gf | Switch | 4P-SMD-7.0X3.5X3.5H-90D | BEST | http://www.seeedstudio.com/wiki/images/0/08/3100060P1.pdf | 0.143 | 20 | 4 | 0.40 |  | http://www.seeedstudio.com/depot/OPLopen-parts-library-catalog-c-136_138/#3100060P1
311020004 | DTSM-62K-S-V-T/R(SN431) | SMD Button ;SPST;100gf | Switch | 4P-SMD-6.0X6.0X5.0H | DIPTRONICS | http://www.seeedstudio.com/wiki/images/d/d3/3100010P1.pdf | 0.114 | 20 | 4 | 0.40 |  | http://www.seeedstudio.com/depot/OPLopen-parts-library-catalog-c-136_138/#3100010P1
311020024 | TS-1109 | DIP Button;SPST;160gf | Switch | 4P-6.0X6.0X5.0H | BEST | http://www.seeedstudio.com/wiki/images/2/20/3110040P1.pdf | 0.035 | 30 | 4 | 0.40 |  | http://www.seeedstudio.com/depot/OPLopen-parts-library-catalog-c-136_138/#3110040P1
311010004 | MS-22D18 G2 ROHS | DIP Switch;SPDT;200gf | Switch | 6P-2CH-2.54-9.1X3.5X3.2+2H | Deyilong | http://www.seeedstudio.com/wiki/images/0/03/3010010P1.pdf | 0.131 | 20 | 6 | 0.60 |  | http://www.seeedstudio.com/depot/OPLopen-parts-library-catalog-c-136_138/#3010010P1
305010013 | MMBT3904LT1G | SMD Transistors NPN 40V 200mA | Transistor | SOT-23 | ON Semiconductor | http://www.seeedstudio.com/wiki/images/8/89/305010013.pdf | 0.020 | 50 | 2 | 0.20 |  | http://www.seeedstudio.com/depot/OPLopen-parts-library-catalog-c-136_138/#305010013
314080008 | ADXL345BCCZ-RL | SMD Digital 3-Axis-Accelerometers Sensor;±16g | Sensor | 14-LGA | Analog Devices Inc | http://www.seeedstudio.com/wiki/images/1/1f/314080008.pdf | 1.867 | 2 | 14 | 1.40 |  | http://www.seeedstudio.com/depot/OPLopen-parts-library-catalog-c-136_138/#314080008
315030009 | HLS8L-DC3V-S-C | DIP Power Relay 3V-7A | Relay | 5P-L19.0*W15.0*H15.0mm | HELISHUN |  | 0.508 | 5 | 5 | 0.50 |  | http://www.seeedstudio.com/depot/OPLopen-parts-library-catalog-c-136_138/#315030009
318020019 | 3020-1766 | PCB External 2.4 Antenna;With I-PEX Cable | Antenna | L40.5*W5.0*H1.2mm | FEIYUXIN |  | 0.859 | 3 | 8 | 0.80 |  | http://www.seeedstudio.com/depot/OPLopen-parts-library-catalog-c-136_138/#318020019
318020014 | IPEX-PCB-113-L42 | PCB External GSM Antenna;4-Band 850/900/1800/1900;With I-PEX Cable | Antenna | 18*40*42mm | FEIYUXIN |  | 1.094 | 3 | 0 | 0.00 |  | http://www.seeedstudio.com/depot/OPLopen-parts-library-catalog-c-136_138/#318020014
314110001 | NCP18WF104F03RC | SMD RES Thermistor NTC 100K-1%; | Resistor | 0603 | Murata |  | 0.050 | 20 | 2 | 0.20 |  | http://www.seeedstudio.com/depot/OPLopen-parts-library-catalog-c-136_138/#314110001
310070026 | CH340T | SMD IC Interface;USB to UART;Speed 2400b-112.5Kbps;VCC 3.3V-5V | IC | SSOP-20 | WCH |  | 0.600 | 5 | 8 | 0.80 |  | http://www.seeedstudio.com/depot/OPLopen-parts-library-catalog-c-136_138/#310070026
310060026 | nRF51822; | SMD IC RF;2.4G RF & Cortex M0 MCU;QFAA 256KB Flash;16KB RAM;VCC 1.8V-3.6V | IC | QFN-48 | Nordic Semiconductor |  | 3.000 | 1 | 12 | 1.20 |  | http://www.seeedstudio.com/depot/OPLopen-parts-library-catalog-c-136_138/#310060026
301010198 | RC0603FR-076K8L | SMD RES 6.8K-1%-1/10W | Resistor | 0603 | YAGEO |  | 0.010 | 100 | 2 | 0.20 |  | http://www.seeedstudio.com/depot/OPLopen-parts-library-catalog-c-136_138/#301010198
301010456 | RC0402FR-07100KL | SMD RES 100K-1%-1/16W | Resistor | 0402 | YAGEO |  | 0.010 | 100 | 2 | 0.20 |  | http://www.seeedstudio.com/depot/OPLopen-parts-library-catalog-c-136_138/#301010456
301010069 | RC0402FR-07470KL | SMD RES 470K-1%-1/16W | Resistor | 0402 | YAGEO |  | 0.010 | 100 | 2 | 0.20 |  | http://www.seeedstudio.com/depot/OPLopen-parts-library-catalog-c-136_138/#301010069
304090073 | Y502DC | DIP LED Yellow-Yellow | LED | Radial-2P-2.54-5mm | CHENGGUNAGXING |  | 0.043 | 30 | 1.5 | 0.20 |  | http://www.seeedstudio.com/depot/OPLopen-parts-library-catalog-c-136_138/#304090073
310070030 | FT230XS-R | SMD IC Interface;USB to UART;Speed 300b-3Mbaud;VCC 2.97V-5.5V | IC | SSOP-16 | FTDI |  | 3.500 | 1 | 16 | 1.60 |  | http://www.seeedstudio.com/depot/OPLopen-parts-library-catalog-c-136_138/#310070030
312030029 | EAO-9745-PFA-C1033-28-008 | DIP Analog microphone;SN58dB;SPL110dB;50-16KHZ | Microphones | 2P-ROUND-9.7*4.5mm | Guangjixing |  | 0.270 | 5 | 2 | 0.20 |  | http://www.seeedstudio.com/depot/OPLopen-parts-library-catalog-c-136_138/#312030029
304080005 | SYD3642ASR | LED Red 4-DIG 7-SEG Display | Display | 7-4-BYTE-SEG-2.54-30*14*7.3H | FANGZHOU |  | 0.687 | 3 | 12 | 1.20 |  | http://www.seeedstudio.com/depot/OPLopen-parts-library-catalog-c-136_138/#304080005
301040022 | WH09-2-103 | DIP VR Top Adj 10k; | Resistor | 3P-2.5-L20 | BAISITE |  | 0.174 | 10 | 2 | 0.20 |  | http://www.seeedstudio.com/depot/OPLopen-parts-library-catalog-c-136_138/#301040022
303010086 | LQM2MPN2R2MG0 | SMD Inductor;2.2uH-20%-1.2A | Inductor | 0805 | AVX |  | 0.117 | 10 | 2 | 0.20 |  | http://www.seeedstudio.com/depot/OPLopen-parts-library-catalog-c-136_138/#303010086
301010001 | RC0402JR-071K5L | SMD RES 1.5K-5%-1/16W | Resistor | 0402 | YAGEO |  | 0.010 | 100 | 2 | 0.20 |  | http://www.seeedstudio.com/depot/OPLopen-parts-library-catalog-c-136_138/#301010001
301010264 | RL0805JR-070R1L | SMD RES 0.1R-5%-1/8W | Resistor | 0805 | YAGEO |  | 0.010 | 50 | 2 | 0.20 |  | http://www.seeedstudio.com/depot/OPLopen-parts-library-catalog-c-136_138/#301010264
304090086 | 504RGBW-K | DIP LED Vaporous-RGB | LED | Radial-2P-2.54-5mm | chengguangxing |  | 0.086 | 20 | 2 | 0.20 |  | http://www.seeedstudio.com/depot/OPLopen-parts-library-catalog-c-136_138/#304090086
320170002 |  | DIP CR1220 Cell Battery Holder | Connector | Metal CR1220-D13.5*H5.0mm |  |  | 0.018 | 50 | 2 | 0.20 |  | http://www.seeedstudio.com/depot/OPLopen-parts-library-catalog-c-136_138/#320170002
323050000 |  | Folding Clasps | Connector | D11.5*H6.0mm | JJWJ |  | 0.032 | 50 | 1 | 0.10 |  | http://www.seeedstudio.com/depot/OPLopen-parts-library-catalog-c-136_138/#323050000
304080004 | SP400561N | LED 10 SEG Gauge Bar | Display | 33.02*15.24mm | SP400561N |  | 0.516 | 1 | 20 | 2.00 |  | http://www.seeedstudio.com/depot/OPLopen-parts-library-catalog-c-136_138/#304080004
320030097 | FBM1211-1001A01B1AF | SMD Black Female Header | Connector | 1*10P-2.0-L20.5*W2.5*H2.4-R/A | YXCON |  | 0.199 | 10 | 10 | 1.00 |  | http://www.seeedstudio.com/depot/OPLopen-parts-library-catalog-c-136_138/#320030097
310010016 | ATMEGA32U4-MUR | SMD IC MCU;AVR;USB;8-Bit;32KB;16MHz;1.8-5.5V | IC | VQFN-44 | Atmel |  | 6.500 | 1 | 44 | 4.40 |  | http://www.seeedstudio.com/depot/OPLopen-parts-library-catalog-c-136_138/#310010016
303030006 | BLM21PG331SN1D | SMD Ferrite Bead 330R-1500mA | Inductor | 0805 | Murata |  | 0.031 | 50 | 2 | 0.20 |  | http://www.seeedstudio.com/depot/OPLopen-parts-library-catalog-c-136_138/#303030006
310030105 | TD1410 | SMD IC PMIC;Vin 3.6V-20V;Vout 1.325V-18V;Iout 2A;With-EN | IC | SOP8 | Techcode |  | 0.400 | 5 | 8 | 0.80 |  | http://www.seeedstudio.com/depot/OPLopen-parts-library-catalog-c-136_138/#310030105
310030161 | ETA3410D2I-T | SMD PMIC;DC-DC;Vin 2.6-5.5V,Adj;2A;3MHz;Sync;Buck;1-Ch | IC | DFN(2*2)-8 | ETA |  | 0.300 | 5 | 8 | 0.80 |  | http://www.seeedstudio.com/depot/OPLopen-parts-library-catalog-c-136_138/#310030161
310030153 | ETA1036-50S2F-T | SMD PMIC;DC-DC;Vin 0.6-4.5V;3W;2MHz;Boost;1-Ch | IC | SOT23-5 | ETA |  | 0.350 | 5 | 5 | 0.50 |  | http://www.seeedstudio.com/depot/OPLopen-parts-library-catalog-c-136_138/#310030153
301020003 | FHCFR-1/4W-331J | DIP RES 330R-5%-1/4W;Axial-D2.3*L6.5mm | Resistor | Axial-D2.3*L6.5mm | Fenghua |  | 0.010 | 100 | 2 | 0.20 |  | http://www.seeedstudio.com/depot/OPLopen-parts-library-catalog-c-136_138/#301020003
301020029 | FHCFR-1/4W-471J | DIP RES 470R-5%-1/4W;Axial-D2.3*L6.5mm | Resistor | Axial-D2.3*L6.5mm | Fenghua |  | 0.010 | 100 | 2 | 0.20 |  | http://www.seeedstudio.com/depot/OPLopen-parts-library-catalog-c-136_138/#301020029
301020000 | FHCFR-1/4W-102J | DIP RES 1K-5%-1/4W;Axial-D2.3*L6.5mm | Resistor | Axial-D2.3*L6.5mm | Fenghua |  | 0.010 | 100 | 2 | 0.20 |  | http://www.seeedstudio.com/depot/OPLopen-parts-library-catalog-c-136_138/#301020000
301020001 | FHCFR-1/4W-103J | DIP RES 10K-5%-1/4W;Axial-D2.3*L6.5mm | Resistor | Axial-D2.3*L6.5mm | Fenghua |  | 0.010 | 100 | 2 | 0.20 |  | http://www.seeedstudio.com/depot/OPLopen-parts-library-catalog-c-136_138/#301020001
302010022 | CC0402KRX7R9BB222 | SMD CAP Ceramic 2.2nF-50V-10%-X7R | Capacitor | 0402 | YAGEO |  | 0.010 | 100 | 2 | 0.20 |  | http://www.seeedstudio.com/depot/OPLopen-parts-library-catalog-c-136_138/#302010022
301010466 | RC0402FR-07330RL | SMD RES 330R-1%-1/16W;0402 | Resistor | 0402 | YAGEO |  | 0.010 | 100 | 2 | 0.20 |  | http://www.seeedstudio.com/depot/OPLopen-parts-library-catalog-c-136_138/#301010466
301010052 | RC0402FR-0722RL | SMD RES 22R-1%-1/16W | Resistor | 0402 | YAGEO |  | 0.010 | 100 | 2 | 0.20 |  | http://www.seeedstudio.com/depot/OPLopen-parts-library-catalog-c-136_138/#301010052
301010010 | RC0402JR-074K7L | SMD RES 4.7K-5%-1/16W | Resistor | 0402 | YAGEO |  | 0.010 | 100 | 2 | 0.20 |  | http://www.seeedstudio.com/depot/OPLopen-parts-library-catalog-c-136_138/#301010010
301010005 | RC0402JR-0747KL | SMD RES 47K-5%-1/16W | Resistor | 0402 | YAGEO |  | 0.010 | 100 | 2 | 0.20 |  | http://www.seeedstudio.com/depot/OPLopen-parts-library-catalog-c-136_138/#301010005
314020026 | GUVA-S12SD | SMD UV Sensor | Sensor | SMD3528 | GENICOM |  | 3.180 | 1 | 4 | 0.40 |  | http://www.seeedstudio.com/depot/OPLopen-parts-library-catalog-c-136_138/#314020026
301010009 | RC0402JR-071ML | SMD RES 1M-5%-1/16W | Resistor | 0402 | YAGEO |  | 0.010 | 100 | 2 | 0.20 |  | http://www.seeedstudio.com/depot/OPLopen-parts-library-catalog-c-136_138/#301010009
301010124 | RC0603JR-072K2L | SMD RES 2.2K-5%-1/10W | Resistor | 0603 | YAGEO |  | 0.010 | 100 | 2 | 0.20 |  | http://www.seeedstudio.com/depot/OPLopen-parts-library-catalog-c-136_138/#301010124
301010158 | RC0603FR-0716KL | SMD RES 16K-1%-1/10W | Resistor | 0603 | YAGEO |  | 0.010 | 100 | 2 | 0.20 |  | http://www.seeedstudio.com/depot/OPLopen-parts-library-catalog-c-136_138/#301010158
301010221 | RC0603FR-072KL | SMD RES 2K-1%-1/10W | Resistor | 0603 | YAGEO |  | 0.010 | 100 | 2 | 0.20 |  | http://www.seeedstudio.com/depot/OPLopen-parts-library-catalog-c-136_138/#301010221
302010012 | CC0402JRNPO9BN101 | SMD CAP Ceramic 100pF-50V-5%-NPO | Capacitor | 0402 | YAGEO |  | 0.010 | 100 | 2 | 0.20 |  | http://www.seeedstudio.com/depot/OPLopen-parts-library-catalog-c-136_138/#302010012
302010021 | CC0402BRNPO9BN1R0 | SMD CAP Ceramic 1pF-50V-0.1pF-NPO | Capacitor | 0402 | YAGEO |  | 0.010 | 100 | 2 | 0.20 |  | http://www.seeedstudio.com/depot/OPLopen-parts-library-catalog-c-136_138/#302010021
302010023 | CC0402BRNPO9BN1R5 | SMD CAP Ceramic 1.5pF-50V-0.1pF-NPO | Capacitor | 0402 | YAGEO |  | 0.010 | 100 | 2 | 0.20 |  | http://www.seeedstudio.com/depot/OPLopen-parts-library-catalog-c-136_138/#302010023
302010041 | GRM1555C1H150JA01D | SMD CAP Ceramic 15pF-50V-5%-NPO | Capacitor | 0402 | Murata |  | 0.010 | 100 | 2 | 0.20 |  | http://www.seeedstudio.com/depot/OPLopen-parts-library-catalog-c-136_138/#302010041
302010049 | CC0402JRNPO9BN120 | SMD CAP Ceramic 12pF-50V-5%-NPO; | Capacitor | 0402 | YAGEO |  | 0.010 | 100 | 2 | 0.20 |  | http://www.seeedstudio.com/depot/OPLopen-parts-library-catalog-c-136_138/#302010049
302010054 | CC0603KRX7R6BB225 | SMD CAP Ceramic 2.2uF-10V-10%-X7R; | Capacitor | 0603 | YAGEO |  | 0.037 | 50 | 2 | 0.20 |  | http://www.seeedstudio.com/depot/OPLopen-parts-library-catalog-c-136_138/#302010054
302010103 | CC0603KRX5R6BB106 | SMD CAP Ceramic 10uF-10V-10%-X5R | Capacitor | 0603 | YAGEO |  | 0.101 | 20 | 2 | 0.20 |  | http://www.seeedstudio.com/depot/OPLopen-parts-library-catalog-c-136_138/#302010103
302010158 | CC0805ZKY5V6BB106 | SMD CAP Ceramic 10uF-10V-(-20%～+80%)-Y5V | Capacitor | 0805 | YAGEO; |  | 0.037 | 50 | 2 | 0.20 |  | http://www.seeedstudio.com/depot/OPLopen-parts-library-catalog-c-136_138/#302010158
302020006 | TAJA475K016RNJ | SMD CAP Tantalum 4.7uF-16V;A | Capacitor | AVX-A | AVX |  | 0.112 | 20 | 2 | 0.20 |  | http://www.seeedstudio.com/depot/OPLopen-parts-library-catalog-c-136_138/#302020006
302020008 | TAJA226K010RNJ | SMD CAP Tantalum 22uF-10V | Capacitor | AVX-A | AVX |  | 0.098 | 20 | 2 | 0.20 |  | http://www.seeedstudio.com/depot/OPLopen-parts-library-catalog-c-136_138/#302020008
302020013 | TAJB226K016RNJ | SMD CAP Tantalum 22uF-16V | Capacitor | AVX-B | AVX |  | 0.180 | 20 | 2 | 0.20 |  | http://www.seeedstudio.com/depot/OPLopen-parts-library-catalog-c-136_138/#302020013
302020015 | TAJB107M010RNJ | SMD CAP Tantalum 100uF-10V | Capacitor | AVX-B | AVX |  | 0.352 | 10 | 2 | 0.20 |  | http://www.seeedstudio.com/depot/OPLopen-parts-library-catalog-c-136_138/#302020015
302030053 | CS1E221M-CRE77 | SMD CAP Aluminum 220uF-16V; | Capacitor | D6.3*H7.7mm | SEMTECH |  | 0.061 | 20 | 2 | 0.20 |  | http://www.seeedstudio.com/depot/OPLopen-parts-library-catalog-c-136_138/#302030053
303010037 | LQG15HS4N7S02 | SMD Inductor 4.7nH-0.3nH-300mA | Inductor | 0402 | Murata |  | 0.010 | 100 | 2 | 0.20 |  | http://www.seeedstudio.com/depot/OPLopen-parts-library-catalog-c-136_138/#303010037
303030008 | WLB2012-471T20 | SMD Ferrite Bead 470R-2A | Inductor | 0805 | WELL |  | 0.012 | 100 | 2 | 0.20 |  | http://www.seeedstudio.com/depot/OPLopen-parts-library-catalog-c-136_138/#303030008
304020012 | B0540W | SMD Diode Schottky 40V-500mA | Diode | SOD-123 | JCET |  | 0.062 | 30 | 2 | 0.20 |  | http://www.seeedstudio.com/depot/OPLopen-parts-library-catalog-c-136_138/#304020012
306010020 | FC-12M | SMD Crystal 32.768KHz-12.5pF-20ppm-90k | Crystal Oscillator | 2P-L2.05*W1.2*H0.6mm | Epson |  | 0.742 | 3 | 2 | 0.20 |  | http://www.seeedstudio.com/depot/OPLopen-parts-library-catalog-c-136_138/#306010020
306010053 | CSTCE8M00G55-RO | SMD Crystal 8MHz-0.3%-150R | Crystal Oscillator | 3P-L3.2*W1.3mm | Murata |  | 0.430 | 5 | 2 | 0.20 |  | http://www.seeedstudio.com/depot/OPLopen-parts-library-catalog-c-136_138/#306010053
310020003 | OPA333AIDBVT | SMD IC Amplifier;1-CH;GBW 0.35MHz;Io 3mA;1.8V-5.5V;±0.9V-2.75V | IC | SOT-23-5 | TI |  | 1.800 | 2 | 2 | 0.20 |  | http://www.seeedstudio.com/depot/OPLopen-parts-library-catalog-c-136_138/#310020003
310030016 | XC6206P182MR | SMD PMIC;DC-DC;Vin 2.6-5.5V; Adj;2A;3MHz;Buck;1-Ch | IC | SOT-23 | Torex |  | 0.120 | 10 | 1 | 0.10 |  | http://www.seeedstudio.com/depot/OPLopen-parts-library-catalog-c-136_138/#310030016
310050026 | TXS0108EPWR | SMD IC Logic;8-bit noninverting;VCCA 1.2V-3.6V;VCCB 1.65V-5.5V;Iout 50mA | IC | TSSOP-20 | TI |  | 1.000 | 3 | 5 | 0.50 |  | http://www.seeedstudio.com/depot/OPLopen-parts-library-catalog-c-136_138/#310050026
320110049 | ZB2001-02 | DIP White JST;2Pin-2.0 | Connector | 2.0-2P | ZUANBAO |  | 0.010 | 100 | 2 | 0.20 |  | http://www.seeedstudio.com/depot/OPLopen-parts-library-catalog-c-136_138/#320110049
320110054 | JST 2P-1.0 | SMD White JST;2Pin-1.0 pitch | Connector | 2P-1.0-90D | ZUANBAO | 这部分空的 | 0.054 | 20 | 4 | 0.40 |  | http://www.seeedstudio.com/depot/OPLopen-parts-library-catalog-c-136_138/#320110054
326080002 | R3075 | Rivet;Black-Plastic-R3075 | Rivets | R3075 | HKWASI |  | 0.028 | 50 | 0 | 0.00 |  | http://www.seeedstudio.com/depot/OPLopen-parts-library-catalog-c-136_138/#326080002
326080011 | R2064 | Rivet;Black-Plastic-R2064 | Rivets | R2064 | HKWASI |  | 0.028 | 50 | 0 | 0.00 |  | http://www.seeedstudio.com/depot/OPLopen-parts-library-catalog-c-136_138/#326080011
301010113 | RC0603JR-072KL | SMD RES 2K-5%-1/10W | Resistor | 0603 | YAGEO |  | 0.010 | 100 | 2 | 0.20 |  | http://www.seeedstudio.com/depot/OPLopen-parts-library-catalog-c-136_138/#301010113
302010175 | CC0805JRX7R9BB103 | SMD CAP Ceramic 10nF-50V-5%-X7R | Capacitor | 0805 | YAGEO |  | 0.023 | 50 | 2 | 0.20 |  | http://www.seeedstudio.com/depot/OPLopen-parts-library-catalog-c-136_138/#302010175
302010208 | CC1-F5SL2A101KSPW | DIP CAP Ceramic Disc 100nF-50V-Y5V | Capacitor | Radial-Disc-2.5-D5.0mm |  |  | 0.015 | 50 | 2 | 0.20 |  | http://www.seeedstudio.com/depot/OPLopen-parts-library-catalog-c-136_138/#302010208
302030059 | CS1E470M-CRE54 | SMD CAP Aluminum 47uF-25V | Capacitor | SMD-D6.3*H5.4mm |  |  | 0.054 | 25 | 2 | 0.20 |  | http://www.seeedstudio.com/depot/OPLopen-parts-library-catalog-c-136_138/#302030059
301020040 | FHCFR-1/6W-104J | DIP RES 100K-5%-1/6W; | Resistor | Axial-D1.7*L3.3mm |  |  | 0.010 | 100 | 2 | 0.20 |  | http://www.seeedstudio.com/depot/OPLopen-parts-library-catalog-c-136_138/#301020040
305030010 | NCE3407A | SMD MOSFET P-CH 30V 4.3A | Transistor | SOT-23 | JCET |  | 0.105 | 20 | 3 | 0.30 |  | http://www.seeedstudio.com/depot/OPLopen-parts-library-catalog-c-136_138/#305030010
314130003 | CG0603MLC-05E | SMD Chip Guard;5V-28V | ESD | 0603 | Bourns Inc. |  | 0.215 | 10 | 2 | 0.20 |  | http://www.seeedstudio.com/depot/OPLopen-parts-library-catalog-c-136_138/#314130003
301010043 | RC0402FR-071ML | SMD RES 1M-1%-1/16W; | Resistor | 0402 | YAGEO |  | 0.010 | 100 | 2 | 0.20 |  | http://www.seeedstudio.com/depot/OPLopen-parts-library-catalog-c-136_138/#301010043
303010042 | LQH2MCN100K02L | SMD Inductor 10uH-10%-225mA | Inductor | 0806 | Murata |  | 0.156 | 10 | 2 | 0.20 |  | http://www.seeedstudio.com/depot/OPLopen-parts-library-catalog-c-136_138/#303010042
311020047 | B3U-1000P-2P-SMD | SMD Button;153gf | Switch | L3.0*W2.5*H1.2+0.4mm | omron |  | 0.562 | 5 | 2 | 0.20 |  | http://www.seeedstudio.com/depot/OPLopen-parts-library-catalog-c-136_138/#311020047
320040003 | PJ-3536-L6S | SMD Audio Jack;3.5mm;4 Degree | Connector | 3.5mm-8P | SUNGTECH |  | 0.418 | 5 | 2 | 0.20 |  | http://www.seeedstudio.com/depot/OPLopen-parts-library-catalog-c-136_138/#320040003
311020017 | SKQGADE010 | SMD Button;260gf | Switch | 4P-L5.2*W5.2*H1.5mm | ALPS |  | 0.157 | 10 | 4 | 0.40 |  | http://www.seeedstudio.com/depot/OPLopen-parts-library-catalog-c-136_138/#311020017
311030001 | MK-12C02 G1.5 | SMD Switch ;SPST;150gf | Switch | 7P-L6.7*W2.7*H3.2mm | DYL |  | 0.241 | 10 | 7 | 0.70 |  | http://www.seeedstudio.com/depot/OPLopen-parts-library-catalog-c-136_138/#311030001
311030008 | 3P-2.0-90D-REINFORCE; | DIP Toggle Switch;SPST;250gf | Switch | 3P-L8.7*W4.7*H8.4+4mm | DYL |  | 0.087 | 20 | 3 | 0.30 |  | http://www.seeedstudio.com/depot/OPLopen-parts-library-catalog-c-136_138/#311030008
320010003 | 10118193-0001LF | SMD Micro USB-B | Connector | 5P-90D | FCI |  | 0.829 | 2 | 5 | 0.50 |  | http://www.seeedstudio.com/depot/OPLopen-parts-library-catalog-c-136_138/#320010003
320010005 | ZX62D-B-5P8 | SMD Micro USB-B | Connector | SMD-5P-7.15*5*1.85MM | suntech |  | 0.265 | 10 | 5 | 0.50 |  | http://www.seeedstudio.com/depot/OPLopen-parts-library-catalog-c-136_138/#320010005
320010018 | ST-USB-009A | USB Female Type B Connector | Connector | DIP-2P-17.1*14.6*12.1mm-2mm | suntech |  | 0.300 | 10 | 0 | 0.00 |  | http://www.seeedstudio.com/depot/OPLopen-parts-library-catalog-c-136_138/#320010018
301020017 | FHCFR-1/4W-101J | DIP RES 100R-5%-1/4W | Resistor | Axial-D2.3*L6.5mm | FENGHUA |  | 0.010 | 100 | 2 | 0.20 |  | http://www.seeedstudio.com/depot/OPLopen-parts-library-catalog-c-136_138/#301020017
301020005 | FHCFR-1/4W-105J | DIP RES 1M-5%-1/4W; | Resistor | Axial-D2.3*L6.5mm | FENGHUA |  | 0.010 | 100 | 2 | 0.20 |  | http://www.seeedstudio.com/depot/OPLopen-parts-library-catalog-c-136_138/#301020005
301020010 | FHCFR-1/4W-222J | DIP RES 2.2K-5%-1/4W; | Resistor | Axial-D2.3*L6.5mm | FENGHUA |  | 0.010 | 100 | 2 | 0.20 |  | http://www.seeedstudio.com/depot/OPLopen-parts-library-catalog-c-136_138/#301020010
301020011 | FHCFR-1/4W-221J | DIP RES 220R-5%-1/4W; | Resistor | Axial-D2.3*L6.5mm | FENGHUA |  | 0.010 | 100 | 2 | 0.20 |  | http://www.seeedstudio.com/depot/OPLopen-parts-library-catalog-c-136_138/#301020011
301020042 | FHCFR-1/4W-332J | DIP RES 3.3K-5%-1/4W; | Resistor | Axial-D2.3*L6.5mm | FENGHUA |  | 0.010 | 100 | 2 | 0.20 |  | http://www.seeedstudio.com/depot/OPLopen-parts-library-catalog-c-136_138/#301020042
301020021 | FHCFR-1/4W-334J | DIP RES 330K-5%-1/4W | Resistor | Axial-D2.3*L6.5mm | FENGHUA |  | 0.010 | 100 | 2 | 0.20 |  | http://www.seeedstudio.com/depot/OPLopen-parts-library-catalog-c-136_138/#301020021
301020012 | FHCFR-1/4W-472J | DIP RES 4.7K-5%-1/4W; | Resistor | Axial-D2.3*L6.5mm | FENGHUA |  | 0.010 | 100 | 2 | 0.20 |  | http://www.seeedstudio.com/depot/OPLopen-parts-library-catalog-c-136_138/#301020012
301020014 | FHCFR-1/4W-470J | DIP RES 47R-5%-1/4W; | Resistor | Axial-D2.3*L6.5mm | FENGHUA |  | 0.010 | 100 | 2 | 0.20 |  | http://www.seeedstudio.com/depot/OPLopen-parts-library-catalog-c-136_138/#301020014
301020022 | FHCFR-1/4W-473J | DIP RES 47K-5%-1/4W; | Resistor | Axial-D2.3*L6.5mm | FENGHUA |  | 0.010 | 100 | 2 | 0.20 |  | http://www.seeedstudio.com/depot/OPLopen-parts-library-catalog-c-136_138/#301020022
301020007 | FHCFR-1/4W-681J | DIP RES 680R-5%-1/4W; | Resistor | Axial-D2.3*L6.5mm | FENGHUA |  | 0.010 | 100 | 2 | 0.20 |  | http://www.seeedstudio.com/depot/OPLopen-parts-library-catalog-c-136_138/#301020007
302010341 | GRM1885C1H102JA01D | SMD CAP Ceramic;1nF-50V-5%-C0G | Capacitor | 0603 | Murata |  | 0.051 | 50 | 2 | 0.20 |  | http://www.seeedstudio.com/depot/OPLopen-parts-library-catalog-c-136_138/#302010341
310040007 | TB6612FNG(O,C8,EL) | SMD IC Driver;Motor Driver;2-CH;VM≤6V;Imout 0.8A;VC 3.3V-5V | IC | SSOP-24 | Toshiba |  | 2.800 | 1 | 24 | 2.40 |  | http://www.seeedstudio.com/depot/OPLopen-parts-library-catalog-c-136_138/#310040007
301010041 | RC0402FR-0749R9L | SMD RES 49.9R-1%-1/16W; | Resistor | 0402 | YAGEO |  | 0.010 | 100 | 2 | 0.20 |  | http://www.seeedstudio.com/depot/OPLopen-parts-library-catalog-c-136_138/#301010041
302010183 | GRM31CR60J107ME39L | SMD CAP Ceramic 100uF-6.3V-20%-X5R | Capacitor | 1206 | Murata |  | 0.309 | 10 | 2 | 0.20 |  | http://www.seeedstudio.com/depot/OPLopen-parts-library-catalog-c-136_138/#302010183
320030087 | F185-1208A0BSYA1 | DIP Black Female Header | Connector | 2*4P-2.54-8.5 | YXCON |  | 0.191 | 10 | 8 | 0.80 |  | http://www.seeedstudio.com/depot/OPLopen-parts-library-catalog-c-136_138/#320030087
320040007 | ST-PJ-312 | SMD Audio Jack;3.5mm;3 Degree | Connector | 6P-3.5-14*9mm | suntech |  | 0.398 | 5 | 6 | 0.60 |  | http://www.seeedstudio.com/depot/OPLopen-parts-library-catalog-c-136_138/#320040007
321070005 |  | Grove Cable;24AWG-200mm;4-Wire;Black/Red/White/Yellow | Cable | 4P-2.0-24AWG-200mm | LLD |  | 0.227 | 10 | 4 | 0.40 |  | http://www.seeedstudio.com/depot/OPLopen-parts-library-catalog-c-136_138/#321070005
326010010 | PM3*6 | Screw;Silver-cross-round head | Screw | PM3.0*H6.0mm | QS |  | 0.010 | 20 | 0 | 0.00 |  | http://www.seeedstudio.com/depot/OPLopen-parts-library-catalog-c-136_138/#326010010
326010014 | PM3*5 | Screw;Silver-cross-round head | Screw | PM3.0*H5.0mm | QS |  | 0.010 | 20 | 0 | 0.00 |  | http://www.seeedstudio.com/depot/OPLopen-parts-library-catalog-c-136_138/#326010014
306010014 | HC-49US 16.000MHz | DIP Crystal 16MHz-18pF-30ppm-40R | Crystal Oscillator | HC49/US-H10.85*W4.5*H3.68mm | JING PENGYUAN |  | 0.131 | 10 | 2 | 0.20 |  | http://www.seeedstudio.com/depot/OPLopen-parts-library-catalog-c-136_138/#306010014
306030002 | CSTCE16M0V53-R0 | SMD Crystal 16MHz-15pF-0.5%-40R | Crystal Oscillator | SMD 3P-3.20X1.30X1.0mm | Murata Electronics |  | 0.254 | 4 | 3 | 0.30 |  | http://www.seeedstudio.com/depot/OPLopen-parts-library-catalog-c-136_138/#306030002
305030026 | FDN340P | SMD MOSFET P-CH 20V-2A | Transistor | SOT-23-3 | Fairchild |  | 0.195 | 20 | 3 | 0.30 |  | http://www.seeedstudio.com/depot/OPLopen-parts-library-catalog-c-136_138/#305030026
305020002 | MMBT3906LT3G | SMD Transistors PNP 40V 200mA | Transistor | SOT-23 | ON |  | 0.017 | 50 | 2 | 0.20 |  | http://www.seeedstudio.com/depot/OPLopen-parts-library-catalog-c-136_138/#305020002
310030211 | TPS2051BDGN | SMD IC PMIC;Vin 2.7V-5.5V;Vout 5V;Iout 500mA;With-EN | IC | MSOP-8 | Texas Instruments |  | 1.505 | 1 | 8 | 0.80 |  | http://www.seeedstudio.com/depot/OPLopen-parts-library-catalog-c-136_138/#310030211
314040002 | HMC5883L | SMD 3-Axis Magnetic Sensor | Sensor | QFN-16 | Honeywell |  | 4.043 | 1 | 16 | 1.60 |  | http://www.seeedstudio.com/depot/OPLopen-parts-library-catalog-c-136_138/#314040002
314990005 | MPU-9250 | SMD 9-Axis Gyroscope/Accelerometer/Magnetometer Sensor | Sensor | QFN-24 | InvenSense |  | 5.859 | 1 | 24 | 2.40 |  | http://www.seeedstudio.com/depot/OPLopen-parts-library-catalog-c-136_138/#314990005
320020034 | P125-1116A0BS116AX | DIP Black Male Header VERT | Connector | 1*16P-2.54-2.54-11.6/3.0mm | YXCON |  | 0.069 | 20 | 16 | 1.60 |  | http://www.seeedstudio.com/depot/OPLopen-parts-library-catalog-c-136_138/#320020034
320070000 | ICX-28P | DIP Black IC Socket | Connector | 2*14P-2.54-7.62mm Row Spacing | NANTECH |  | 0.085 | 10 | 28 | 2.80 |  | http://www.seeedstudio.com/depot/OPLopen-parts-library-catalog-c-136_138/#320070000
302010000 | CC0402JRNPO9BN330 | SMD CAP Ceramic 33pF-50V-5%-NPO; | Capacitor | 0402 | YAGEO |  | 0.010 | 100 | 2 | 0.20 |  | http://www.seeedstudio.com/depot/OPLopen-parts-library-catalog-c-136_138/#302010000
304040005 | CD1206-S01575 | SMD Diode Switching 75V-150mA | Diode | 1206 | Bourns |  | 0.043 | 4 | 2 | 0.20 |  | http://www.seeedstudio.com/depot/OPLopen-parts-library-catalog-c-136_138/#304040005
320030050 | RF130-1023ABS0741 | DIP Black Round Female Header VERT | Connector | 1*2P-2.54-3.0mm-7.4 | YXCON |  | 0.126 | 10 | 2 | 0.20 |  | http://www.seeedstudio.com/depot/OPLopen-parts-library-catalog-c-136_138/#320030050
302010053 | CC0402MRX5R5BB106 | SMD CAP Ceramic 10uF-6.3V-20%-X5R; | Capacitor | 0402 | YAGEO |  | 0.046 | 50 | 2 | 0.20 |  | http://www.seeedstudio.com/depot/OPLopen-parts-library-catalog-c-136_138/#302010053
302010048 | CC0402BRNPO9BNR50 | SMD CAP Ceramic 0.5pF-50V-0.1pF-NPO; | Capacitor | 0402 | YAGEO |  | 0.010 | 100 | 2 | 0.20 |  | http://www.seeedstudio.com/depot/OPLopen-parts-library-catalog-c-136_138/#302010048
302020023 | TAJC107K016RNJ | SMD CAP Tantalum 100uF-16V; | Capacitor | AVX-C | AVX |  | 0.578 | 4 | 2 | 0.20 |  | http://www.seeedstudio.com/depot/OPLopen-parts-library-catalog-c-136_138/#302020023
314070001 | 1002794 | DIP Piezo Vibration Sensor | Sensor | L25.0*W15.0*H1.0 | MEAS |  | 4.062 | 1 | 2 | 0.20 |  | http://www.seeedstudio.com/depot/OPLopen-parts-library-catalog-c-136_138/#314070001
306030005 | CSTCE8M00G15L99-R0 | SMD Crystal 8MHz-33pF-0.1% | Crystal Oscillator | W1.3*L3.2*H1.1mm | Murata |  | 0.430 | 2 | 2 | 0.20 |  | http://www.seeedstudio.com/depot/OPLopen-parts-library-catalog-c-136_138/#306030005
305030059 | IRF520NPBF | DIP MOSFET N-CH 100V 9.7A | Transistor | TO-220-3 | IR |  | 0.633 | 1 | 3 | 0.30 |  | http://www.seeedstudio.com/depot/OPLopen-parts-library-catalog-c-136_138/#305030059
314010011 | TMP36 | DIP Low Voltage Temperature Sensor | Sensor | TO-92-3 | Analog Devices Inc |  | 1.324 | 1 | 3 | 0.30 |  | http://www.seeedstudio.com/depot/OPLopen-parts-library-catalog-c-136_138/#314010011
321050033 |  | Power Cable;9V BAT to 2.1mm DC Jack;24AWG-185mm;2-Wire;Red/Black | Cable | 24AWG-185mm | SDD |  | 0.410 | 5 | 0 | 0.00 |  | http://www.seeedstudio.com/depot/OPLopen-parts-library-catalog-c-136_138/#321050033
301010047 | RC0402FR-0710KL | SMD RES 10K-1%-1/16W; | Resistor | 0402 | YAGEO |  | 0.010 | 100 | 2 | 0.20 |  | http://www.seeedstudio.com/depot/OPLopen-parts-library-catalog-c-136_138/#301010047
301010100 | RC0603JR-071ML | SMD RES 1M-5%-1/10W; | Resistor | 0603 | YAGEO |  | 0.010 | 100 | 2 | 0.20 |  | http://www.seeedstudio.com/depot/OPLopen-parts-library-catalog-c-136_138/#301010100
301010104 | RC0603JR-0718KL | SMD RES 18K-5%-1/10W; | Resistor | 0603 | YAGEO |  | 0.010 | 100 | 2 | 0.20 |  | http://www.seeedstudio.com/depot/OPLopen-parts-library-catalog-c-136_138/#301010104
301010138 | RC0603JR-0739RL | SMD RES 39R-5%-1/10W; | Resistor | 0603 | YAGEO |  | 0.010 | 100 | 2 | 0.20 |  | http://www.seeedstudio.com/depot/OPLopen-parts-library-catalog-c-136_138/#301010138
301010140 | RC0603JR-073R6L | SMD RES 3.6R-5%-1/10W; | Resistor | 0603 | YAGEO |  | 0.010 | 100 | 2 | 0.20 |  | http://www.seeedstudio.com/depot/OPLopen-parts-library-catalog-c-136_138/#301010140
301010218 | RC0603JR-07200RL | SMD RES 200R-5%-1/10W; | Resistor | 0603 | YAGEO |  | 0.010 | 100 | 2 | 0.20 |  | http://www.seeedstudio.com/depot/OPLopen-parts-library-catalog-c-136_138/#301010218
301010230 | RC0603JR-07560KL | SMD RES 560K-5%-1/10W; | Resistor | 0603 | YAGEO |  | 0.010 | 100 | 2 | 0.20 |  | http://www.seeedstudio.com/depot/OPLopen-parts-library-catalog-c-136_138/#301010230
301010444 | RC0402FR-0710RL | SMD RES 10R-1%-1/16W; | Resistor | 0402 | YAGEO |  | 0.010 | 100 | 2 | 0.20 |  | http://www.seeedstudio.com/depot/OPLopen-parts-library-catalog-c-136_138/#301010444
301010509 | RC0402FR-0710ML | SMD RES;10M-1%-1/16W | Resistor | 0402 | YAGEO |  | 0.010 | 100 | 2 | 0.20 |  | http://www.seeedstudio.com/depot/OPLopen-parts-library-catalog-c-136_138/#301010509
301010671 | RC0402FR-072K7L | SMD RES 2.7K-1%-1/16W; | Resistor | 402 | YAGEO |  | 0.010 | 100 | 2 | 0.20 |  | http://www.seeedstudio.com/depot/OPLopen-parts-library-catalog-c-136_138/#301010671
302010091 | CC0603CRNPO9BN4R7 | SMD CAP Ceramic 4.7pF-50V-0.25pF-NPO; | Capacitor | 0603 | YAGEO |  | 0.011 | 100 | 2 | 0.20 |  | http://www.seeedstudio.com/depot/OPLopen-parts-library-catalog-c-136_138/#302010091
302010189 | CC1206KKX7RCBB102 | SMD CAP Ceramic 1nF-1KV-10%-X7R; | Capacitor | 1206 | YAGEO |  | 0.037 | 50 | 2 | 0.20 |  | http://www.seeedstudio.com/depot/OPLopen-parts-library-catalog-c-136_138/#302010189
303010027 | LQG15HS15NJ02 | SMD Inductor 15nH-5%-300mA | Inductor | 0402 | Murata |  | 0.010 | 100 | 2 | 0.20 |  | http://www.seeedstudio.com/depot/OPLopen-parts-library-catalog-c-136_138/#303010027
303010056 | LQG15HS3N3S02D | SMD Inductor 3.3nH-0.3nH-300mA | Inductor | 0402 | Murata |  | 0.010 | 100 | 2 | 0.20 |  | http://www.seeedstudio.com/depot/OPLopen-parts-library-catalog-c-136_138/#303010056
303030020 | BLM18BD252SN1D | SMD Ferrite Bead 2.5k-50mA | Inductor | 0603 | Murata |  | 0.013 | 100 | 2 | 0.20 |  | http://www.seeedstudio.com/depot/OPLopen-parts-library-catalog-c-136_138/#303030020
304010007 | MMSD4148 | SMD Diode Switching 100V-200mA | Diode | SOD-123 | Fairchild |  | 0.469 | 50 | 2 | 0.20 |  | http://www.seeedstudio.com/depot/OPLopen-parts-library-catalog-c-136_138/#304010007
302010051 | CC0402KRX7R7BB224 | SMD CAP Ceramic 220nF-16V-10%-X7R; | Capacitor | 0402 | YAGEO |  | 0.020 | 100 | 2 | 0.20 |  | http://www.seeedstudio.com/depot/OPLopen-parts-library-catalog-c-136_138/#302010051
302010007 | CC0402JRNPO9BN470 | SMD CAP Ceramic 47pF-50V-5%-NP0; | Capacitor | 0402 | YAGEO |  | 0.010 | 100 | 2 | 0.20 |  | http://www.seeedstudio.com/depot/OPLopen-parts-library-catalog-c-136_138/#302010007
305030000 | BSS138W-7-F | SMD MOSFET N-CH 50V 200mA | Transistor | SOT-323-3 | Diodes Inc |  | 0.156 | 10 | 5 | 0.50 |  | http://www.seeedstudio.com/depot/OPLopen-parts-library-catalog-c-136_138/#305030000
310010005 | ATMEGA328P-MU | SMD IC MCU;AVR;8-Bit;32KB;16MHz;1.8-5.5V | IC | VFQFN-32 | Atmel |  | 2.166 | 1 | 32 | 3.20 |  | http://www.seeedstudio.com/depot/OPLopen-parts-library-catalog-c-136_138/#310010005
310010072 | ATMEGA168PA-MU | SMD IC MCU;AVR;8-Bit;32KB;16MHz;1.8-5.5V | IC | QFN-32 | Atmel |  | 2.506 | 1 | 32 | 3.20 |  | http://www.seeedstudio.com/depot/OPLopen-parts-library-catalog-c-136_138/#310010072
310020007 | LMV358IDGKR | SMD IC Amplifier;2-CH;GBW 1MHz;Io 60mA;2.7V-5.5V;±1.35V-2.75V | IC | MSOP-8 | TI |  | 0.443 | 5 | 8 | 0.80 |  | http://www.seeedstudio.com/depot/OPLopen-parts-library-catalog-c-136_138/#310020007
310030079 | CJ432 | SMD PMIC;LDO;Vin 18V;Adj;200mA;Without En;1-Ch | IC | SOT-23 | JCET |  | 0.029 | 50 | 3 | 0.30 |  | http://www.seeedstudio.com/depot/OPLopen-parts-library-catalog-c-136_138/#310030079
310040023 | MY9221 | SMD IC Driver;LED matrix Driver;12-CH(R/G/B x 4);Vin 3V-5.5V;Iout 3-60mA | IC | TSSOP-24 | My-Semi |  | 0.800 | 4 | 24 | 2.40 |  | http://www.seeedstudio.com/depot/OPLopen-parts-library-catalog-c-136_138/#310040023
310040027 | TM1637 | SMD IC Driver;Digital Tube Driver;8Seg*6Bit;Vin 0.5V-7V;Iout 200mA | IC | 20-SOP | Titian Mec |  | 0.800 | 10 | 20 | 2.00 |  | http://www.seeedstudio.com/depot/OPLopen-parts-library-catalog-c-136_138/#310040027
310050024 | TXB0108PW | SMD IC Logic;8-bit noninverting;VCCA 1.2V-3.6V;VCCB 1.65V-5.5V;Iout 50mA | IC | TSSOP-20 | TI |  | 1.500 | 1 | 20 | 2.00 |  | http://www.seeedstudio.com/depot/OPLopen-parts-library-catalog-c-136_138/#310050024
311100000 | SW-200D | DIP Tilt Switch | Switch | 2P-L12.0*W3.6mm | QH |  | 0.099 | 30 | 2 | 0.20 |  | http://www.seeedstudio.com/depot/OPLopen-parts-library-catalog-c-136_138/#311100000
314080009 | MMA7660FCR1 | SMD Digital 3-Axis-Accelerometers Sensor;±16g | Sensor | DFN-10 | Freescale Semiconductor |  | 1.094 | 3 | 10 | 1.00 |  | http://www.seeedstudio.com/depot/OPLopen-parts-library-catalog-c-136_138/#314080009
328030005 | QT-CC-20016XX | Black Micro-SD to SD Adapter | Connector | 9P-L32mm*W24mm*H2.1mm | GT |  | 0.391 | 10 | 9 | 0.90 |  | http://www.seeedstudio.com/depot/OPLopen-parts-library-catalog-c-136_138/#328030005
318020010 | RH0111-30002 | SMA External 2.4G Antenna | Antenna | SMA-109mm | DYRH |  | 1.289 | 2 | 2 | 0.20 |  | http://www.seeedstudio.com/depot/OPLopen-parts-library-catalog-c-136_138/#318020010
310060021 | ISD1820P | DIP IC Audio;Recording time 20S;VCC 3.3V-5V; | IC | DIP-14 | ISD |  | 0.863 | 2 | 14 | 1.40 |  | http://www.seeedstudio.com/depot/OPLopen-parts-library-catalog-c-136_138/#310060021
320040009 | PJ-393 | SMD Audio Jack;3.5mm;4 Degree | Connector | 8P-16.4*8.7*5.69mm | BST |  | 0.332 | 5 | 8 | 0.80 |  | http://www.seeedstudio.com/depot/OPLopen-parts-library-catalog-c-136_138/#320040009
304090061 | EL-17-215/BHC-AN1P2/3T | SMD LED Clear-Blue | LED | 0805 | Everlight |  | 0.066 | 30 | 2 | 0.20 |  | http://www.seeedstudio.com/depot/OPLopen-parts-library-catalog-c-136_138/#304090061
301010291 | RC0603JR-071KL | SMD RES 1K-5%-1/10W | Resistor | 0603 | YAGEO; |  | 0.010 | 100 | 2 | 0.20 |  | http://www.seeedstudio.com/depot/OPLopen-parts-library-catalog-c-136_138/#301010291
301010293 | RC0603JR-0710KL | SMD RES 10K-5%-1/10W | Resistor | 0603 | YAGEO |  | 0.010 | 100 | 2 | 0.20 |  | http://www.seeedstudio.com/depot/OPLopen-parts-library-catalog-c-136_138/#301010293
301010089 | RC0603JR-07100KL | SMD RES 100K-5%-1/10W | Resistor | 0603 | YAGEO; |  | 0.010 | 100 | 2 | 0.20 |  | http://www.seeedstudio.com/depot/OPLopen-parts-library-catalog-c-136_138/#301010089
302010286 | CC0603MRX5R5BB106 | SMD CAP Ceramic 10uF-6.3V-20%-X5R | Capacitor | 0603 | YAGEO |  | 0.069 | 40 | 2 | 0.20 |  | http://www.seeedstudio.com/depot/OPLopen-parts-library-catalog-c-136_138/#302010286
301030014 | YC324-JK-0722RL | SMD RES Array 22R-4R | Resistor | 1206-8 | Yageo |  | 0.010 | 10 | 2 | 0.20 |  | http://www.seeedstudio.com/depot/OPLopen-parts-library-catalog-c-136_138/#301030014
301040007 | 3386U-103 | DIP VR Top Adj 10k | Resistor | 3P-2.54-L9.5*W9.5*H5.0mm | BST |  | 0.823 | 2 | 3 | 0.30 |  | http://www.seeedstudio.com/depot/OPLopen-parts-library-catalog-c-136_138/#301040007
305030075 | SSM3J328R,LF | SMD MOSFET P-CH 20V 6A | Transistor | SOT-23F | Toshiba |  | 1.125 | 10 | 3 | 0.30 |  | http://www.seeedstudio.com/depot/OPLopen-parts-library-catalog-c-136_138/#305030075
307010040 | MF-MSMF050-2 | SMD PPTC 500mA-15V | Fuse | L4.73*W3.41*H0.85 | Bourns |  | 0.062 | 5 | 2 | 0.20 |  | http://www.seeedstudio.com/depot/OPLopen-parts-library-catalog-c-136_138/#307010040
310030033 | LP2985-33DBVR | SMD IC PMIC;Vin 2.2V-16V;Vout 3.3V;Iout 150mA;With-EN | IC | SOT-23-5 | TI |  | 0.400 | 5 | 5 | 0.50 |  | http://www.seeedstudio.com/depot/OPLopen-parts-library-catalog-c-136_138/#310030033
302010242 | CC0402KRX7R9BB223 | SMD CAP Ceramic 22nF-50V-10%-X7R | Capacitor | 0402 | YAGEO |  | 0.010 | 100 | 2 | 0.20 |  | http://www.seeedstudio.com/depot/OPLopen-parts-library-catalog-c-136_138/#302010242
301010033 | RC0402JR-07100KL | SMD RES 100K-5%-1/16W | Resistor | 0402 | YAGEO |  | 0.010 | 100 | 2 | 0.20 |  | http://www.seeedstudio.com/depot/OPLopen-parts-library-catalog-c-136_138/#301010033
301010435 | RC0402JR-07910KR | SMD RES 910K-5%-1/16W | Resistor | 0402 | YAGEO |  | 0.010 | 100 | 2 | 0.20 |  | http://www.seeedstudio.com/depot/OPLopen-parts-library-catalog-c-136_138/#301010435
301010013 | RC0402JR-07470RL | SMD RES 470R-5%-1/16W | Resistor | 0402 | YAGEO |  | 0.010 | 100 | 2 | 0.20 |  | http://www.seeedstudio.com/depot/OPLopen-parts-library-catalog-c-136_138/#301010013
301010075 | RC0402JR-0710RL | SMD RES 10R-5%-1/16W | Resistor | 0402 | YAGEO |  | 0.010 | 100 | 2 | 0.20 |  | http://www.seeedstudio.com/depot/OPLopen-parts-library-catalog-c-136_138/#301010075
302010261 | CC0402KRX7R9BB472 | SMD CAP Ceramic 4.7nF-50V-10%-X7R | Capacitor | 0402 | YAGEO |  | 0.010 | 100 | 2 | 0.20 |  | http://www.seeedstudio.com/depot/OPLopen-parts-library-catalog-c-136_138/#302010261
302010260 | CC0402KRX7R9BB391 | SMD CAP Ceramic 390pF-50V-10%-X7R | Capacitor | 0402 | YAGEO |  | 0.010 | 100 | 2 | 0.20 |  | http://www.seeedstudio.com/depot/OPLopen-parts-library-catalog-c-136_138/#302010260
310030092 | ISL97516IUZ-TK | SMD IC PMIC;Vin 2.3V-5.5V;Vout up to 25V;Iout 1A;With-EN | IC | MSOP-8 | Intersil |  | 2.500 | 1 | 8 | 0.80 |  | http://www.seeedstudio.com/depot/OPLopen-parts-library-catalog-c-136_138/#310030092
301010241 | RC0603FR-0715KL | SMD RES 15K-1%-1/10W | Resistor | 0603 | YAGEO |  | 0.010 | 100 | 2 | 0.20 |  | http://www.seeedstudio.com/depot/OPLopen-parts-library-catalog-c-136_138/#301010241
302010003 | CC0402KRX5R5BB105 | SMD CAP Ceramic 1uF-6.3V-10%-X5R | Capacitor | 0402 | YAGEO |  | 0.010 | 100 | 2 | 0.20 |  | http://www.seeedstudio.com/depot/OPLopen-parts-library-catalog-c-136_138/#302010003
301010114 | RC0603JR-071K5L | SMD RES 1.5K-5%-1/10W | Resistor | 0603 | YAGEO |  | 0.010 | 100 | 2 | 0.20 |  | http://www.seeedstudio.com/depot/OPLopen-parts-library-catalog-c-136_138/#301010114
302010037 | CC0402KRX5R6BB104 | SMD CAP Ceramic 100nF-10V-10%-X5R; | Capacitor | 0402 | YAGEO |  | 0.010 | 100 | 2 | 0.20 |  | http://www.seeedstudio.com/depot/OPLopen-parts-library-catalog-c-136_138/#302010037
313080037 | SAP050100CN-C | USB Power Adapter;5V/1A | Adapter | 2P-Black-5V-1A(3C) | PENGSHENGYE |  | 4.297 | 1 | 1 | 0.10 |  | http://www.seeedstudio.com/depot/OPLopen-parts-library-catalog-c-136_138/#313080037
306050023 | PZ2012U300-3R0TF | SMD Bead 30R-3A | Crystal Oscillator | 0805 | Sunlord |  | 0.020 | 100 | 2 | 0.20 |  | http://www.seeedstudio.com/depot/OPLopen-parts-library-catalog-c-136_138/#306050023
316030062 | TFK-280SA-22125 | DC Motor 6V;7500±10%rpm;90mA | Motor | D30.4*24+2.0mm | TT MOTOR |  | 3.633 | 1 | 2 | 0.20 |  | http://www.seeedstudio.com/depot/OPLopen-parts-library-catalog-c-136_138/#316030062
310060024 | MAX2659ELT | SMD IC Amplifier;GPS/GNSS LNA;Gain 20.5dB;Frequency 1G-2GHz;1.6V-3.6V | IC | UDFN-6(1.5*1.0mm) | Maxim |  | 0.500 | 3 | 6 | 0.60 |  | http://www.seeedstudio.com/depot/OPLopen-parts-library-catalog-c-136_138/#310060024
306050008 | BLM15BD182SN1 | SMD Bead 1.8k-100mA | Crystal Oscillator | 0402 | Murata |  | 0.011 | 100 | 2 | 0.20 |  | http://www.seeedstudio.com/depot/OPLopen-parts-library-catalog-c-136_138/#306050008
311020045 | DHT-4235A | SMD Button ;SPST;160gf | Switch | Black-4P-L4.7*W3.5*H2.5 | D.O Electronics |  | 0.074 | 10 | 4 | 0.40 |  | http://www.seeedstudio.com/depot/OPLopen-parts-library-catalog-c-136_138/#311020045
302030033 | 100µF/16V 5X7 | DIP CAP Aluminum 47uF-16V; | Capacitor | Radial-D5.0*H7.0mm | JWC |  | 0.016 | 30 | 2 | 0.20 |  | http://www.seeedstudio.com/depot/OPLopen-parts-library-catalog-c-136_138/#302030033
310030010 | L7805CV | DIP PMIC;LDO;Vin xx-35V;5V,Adj;1.5A;Without En;1-Ch | IC | TO220-3 | YA |  | 0.257 | 10 | 3 | 0.30 |  | http://www.seeedstudio.com/depot/OPLopen-parts-library-catalog-c-136_138/#310030010
310030028 | LP2950ACZ-3.3/NOPB | DIP PMIC;LDO;Vin 2.3-30V;3.3V;Adj;100mA;Without En;1-Ch | IC | TO-92 | TI |  | 0.755 | 3 | 3 | 0.30 |  | http://www.seeedstudio.com/depot/OPLopen-parts-library-catalog-c-136_138/#310030028
310010018 | ATMEGA16U2-MU | SMD IC MCU;AVR;8-bit;16KB;16MHz;2.7-5.5V | IC | 32QFN | Atmel |  | 2.800 | 1 | 32 | 3.20 |  | http://www.seeedstudio.com/depot/OPLopen-parts-library-catalog-c-136_138/#310010018
304990003 | WS2812B | WS2812B RGB LED with Integrated Driver Chip | Diode | 5050 | worldsemi |  | 0.211 | 10 | 4.00 | 0.40 |  | http://www.seeedstudio.com/depot/OPLopen-parts-library-catalog-c-136_138/#304990003

Sheet: OPL deleted list
OPL deleted list. 20160131
Seeed SKU | MPN | Description | Category | Package | Manufacturer | Datasheet | Price（$）/pcs | Pieces/set | Solder points Qty | Assem.Cost/pcs（$） | Image URL | Distributor-URL
306010005 | 49S | DIP Crystal 25MHz-20pF-20ppm;HC49US | Crystal Oscillator | HC49US | Xinhunjing |  | 0.15 | 10 | 2 | 0.2 |  | http://www.seeedstudio.com/depot/OPLopen-parts-library-catalog-c-136_138/#306010005
306010004 | 5032/4P | SMD Crystal 8MHz-20pF-20ppm; | Crystal Oscillator | 2P-L5.0*W3.2mm | Xinhunjing |  | 0.45 | 5 | 2 | 0.2 |  | http://www.seeedstudio.com/depot/OPLopen-parts-library-catalog-c-136_138/#306010004
306010033 | 49S8M | DIP Crystal 8MHz-20pF-20ppm-60R; | Crystal Oscillator | HC49S | Xinhunjing |  | 0.15 | 10 | 2 | 0.2 |  | http://www.seeedstudio.com/depot/OPLopen-parts-library-catalog-c-136_138/#306010033
305030018 | Si2343CDS | SMD MOSFET P-CH 30V-5.9A | Transistor | SOT-23 | Vishay Siliconix |  | 0.7 | 5 | 3 | 0.3 |  | http://www.seeedstudio.com/depot/OPLopen-parts-library-catalog-c-136_138/#305030018
305010022 | S9014J6 | SMD Transistor NPN 50V-100mA; | Transistor | SOT-23 | Changjiang |  | 0.05 | 30 | 3 | 0.3 |  | http://www.seeedstudio.com/depot/OPLopen-parts-library-catalog-c-136_138/#305010022
302020026 | TAJC226K025RNJ | SMD CAP Tantalum 22uF-25V 10% 2312 | Capacitor | AVX-C | AVX |  | 0.37 | 10 | 2 | 0.2 |  | http://www.seeedstudio.com/depot/OPLopen-parts-library-catalog-c-136_138/#0130360P1
302010243 | CC1206KKX5R9BB475 | SMD CAP Ceramic 4.7uF-50V-10%-X5R; | Capacitor | 1206 | YAGEO |  | 0.25 | 10 | 2 | 0.2 |  | http://www.seeedstudio.com/depot/OPLopen-parts-library-catalog-c-136_138/#302010243
302010056 | CC0603KRX7R9BB222 | SMD CAP Ceramic 2.2nF-50V-10%-X7R | Capacitor | 0603 | YAGEO |  | 0.01 | 100 | 2 | 0.2 |  | http://www.seeedstudio.com/depot/OPLopen-parts-library-catalog-c-136_138/#302010056
302010094 | CC0603JRNPO9BN221 | SMD CAP Ceramic 220pF-50V-5%-NPO; | Capacitor | C0603 | YAGEO |  | 0.02 | 100 | 2 | 0.2 |  | http://www.seeedstudio.com/depot/OPLopen-parts-library-catalog-c-136_138/#302010094
302010150 | CC0805JRNPO9BN270 | SMD CAP Ceramic 27pF-50V-5%-NPO | Capacitor | 0805 | YAGEO |  | 0.03 | 50 | 2 | 0.2 |  | http://www.seeedstudio.com/depot/OPLopen-parts-library-catalog-c-136_138/#302010150
302010162 | CC0805JRNPO9BN180 | SMD CAP Ceramic 18pF-50V-5%-NPO | Capacitor | 0805 | YAGEO |  | 0.01 | 100 | 2 | 0.2 |  | http://www.seeedstudio.com/depot/OPLopen-parts-library-catalog-c-136_138/#302010162
302010083 | CC0603JRNPO9BN180 | SMD CAP Ceramic 18pF-50V-5%-NPO; | Capacitor | 0603 | YAGEO |  | 0.01 | 100 | 2 | 0.2 |  | http://www.seeedstudio.com/depot/OPLopen-parts-library-catalog-c-136_138/#302010083
302010082 | CC0603JRNPO9BN150 | SMD CAP Ceramic 15pF-50V-5%-NPO;0603 | Capacitor | 0603 | YAGEO |  | 0.01 | 100 | 2 | 0.2 |  | http://www.seeedstudio.com/depot/OPLopen-parts-library-catalog-c-136_138/#302010082
302010102 | CC0603CRNPO9BN2R2 | SMD CAP Ceramic 2.2pF-50V-0.25pF-NPO | Capacitor | 0603 | YAGEO |  | 0.01 | 100 | 2 | 0.2 |  | http://www.seeedstudio.com/depot/OPLopen-parts-library-catalog-c-136_138/#302010102
302010046 | GRM1555C1H1R8BA01D | SMD CAP Ceramic 1.8pF-50V-0.1pF-NPO | Capacitor | 0402 | Murata |  | 0.01 | 100 | 2 | 0.2 |  | http://www.seeedstudio.com/depot/OPLopen-parts-library-catalog-c-136_138/#302010046
320020015 | P125-1102A0BS116A2 | DIP Blue Male Header VERT | Connector | 1*2P-2.54-2.54-11.6/3.0mm | YXCON |  | 0.1 | 20 | 2 | 0.2 |  | http://www.seeedstudio.com/depot/OPLopen-parts-library-catalog-c-136_138/#320020015
320020038 | P125-1103A0BS116A1 | DIP White Male Header VERT; | Connector | 1*3P-2.54-2.54-11.6/3.0mm | YXCON |  | 0.12 | 20 | 3 | 0.3 |  | http://www.seeedstudio.com/depot/OPLopen-parts-library-catalog-c-136_138/#320020038
320020003 | P125-1203A0BS116A1 | DIP Blue Male Header VERT; | Connector | 2*3P-2.54-2.54-11.6/3.0mm | YXCON |  | 0.15 | 20 | 6 | 0.6 |  | http://www.seeedstudio.com/depot/OPLopen-parts-library-catalog-c-136_138/#320020003
320020005 | P125-1106A0BS116A1 | DIP Blue Male Header VERT | Connector | 1*6P-2.54-2.54-11.6/3.0mm | YXCON |  | 0.1 | 20 | 6 | 0.6 |  | http://www.seeedstudio.com/depot/OPLopen-parts-library-catalog-c-136_138/#320020005
320020022 | P125-1106A0BS116A2 | DIP White Male Header VERT; | Connector | 1*6P-2.54-2.54-11.6/3.0mm | YXCON |  | 0.1 | 20 | 6 | 0.6 |  | http://www.seeedstudio.com/depot/OPLopen-parts-library-catalog-c-136_138/#320020022
320020024 | P125-1106B0BA2 | SMD Blue Male Header R/A; | Connector | 1*6P-2.54-2.54-9.3/6.0mm-2 | YXCON |  | 0.1 | 20 | 6 | 0.6 |  | http://www.seeedstudio.com/depot/OPLopen-parts-library-catalog-c-136_138/#320020024
320020031 | P125-1106B0BA1 | SMD Black Male Header R/A; | Connector | 1*6P-2.54-2.54-9.3/6.0mm-2 | YXCON |  | 0.1 | 20 | 6 | 0.6 |  | http://www.seeedstudio.com/depot/OPLopen-parts-library-catalog-c-136_138/#320020031
320020070 | P125-1106A0BR138A2 | DIP Black Male Header R/A; | Connector | 1*6P-2.54-2.54-6.0mm-90D-2 | YXCON |  | 0.1 | 20 | 6 | 0.6 |  | http://www.seeedstudio.com/depot/OPLopen-parts-library-catalog-c-136_138/#320020070
320020004 | P125-1108A0BS116A1 | DIP Blue Male Header VERT | Connector | 1*8P-2.54-2.54-11.6/3.0mm | YXCON |  | 0.1 | 20 | 8 | 0.8 |  | http://www.seeedstudio.com/depot/OPLopen-parts-library-catalog-c-136_138/#320020004
320020021 | P125-1108A0BS116A2 | DIP White Male Header VERT; | Connector | 1*8P-2.54-2.54-11.6/3.0mm | YXCON |  | 0.1 | 20 | 8 | 0.8 |  | http://www.seeedstudio.com/depot/OPLopen-parts-library-catalog-c-136_138/#320020021
320020023 | P125-1108B0BA2 | SMD Blue Male Header R/A; | Connector | 1*8P-2.54-2.54-9.3/6.0mm-2 | YXCON |  | 0.12 | 20 | 8 | 0.8 |  | http://www.seeedstudio.com/depot/OPLopen-parts-library-catalog-c-136_138/#320020023
320020018 | P220-1110A0BS087A1 | DIP White Male Header VERT; | Connector | 1*10P-2.0-2.0-8.7/2.8mm | YXCON |  | 0.2 | 10 | 10 | 1 |  | http://www.seeedstudio.com/depot/OPLopen-parts-library-catalog-c-136_138/#320020018
320020074 | P125-1110A0BR138A1 | DIP Black Male Header R/A; | Connector | 1*10P-2.54-2.54-6.0mm-90D-1 | YXCON |  | 0.12 | 20 | 10 | 1 |  | http://www.seeedstudio.com/depot/OPLopen-parts-library-catalog-c-136_138/#320020074
320020089 | P220-1140A0BS087A1 | DIP White Male Header VERT; | Connector | 1*40P-2.0-2.0-8.7-2.8mm | YXCON |  | 0.25 | 5 | 40 | 4 |  | http://www.seeedstudio.com/depot/OPLopen-parts-library-catalog-c-136_138/#320020089
320020032 | P125-1140B0BA1 | SMD Black Male Header R/A; | Connector | 1*40P-2.0-2.0-4.0mm-2 | YXCON |  | 0.4 | 5 | 40 | 4 |  | http://www.seeedstudio.com/depot/OPLopen-parts-library-catalog-c-136_138/#320020032
320020013 | P125-1140A0BR138A2 | DIP Black Short Male Header R/A; | Connector | 1*40P-2.54-2.54-6.0mm-90D-1 | YXCON |  | 0.4 | 5 | 40 | 4 |  | http://www.seeedstudio.com/depot/OPLopen-parts-library-catalog-c-136_138/#320020013
320030023 | F185-1102A1BSYA1 | DIP Black Female Header VERT; | Connector | 1*2P-2.54-8.5mm | YXCON |  | 0.15 | 10 | 2 | 0.2 |  | http://www.seeedstudio.com/depot/OPLopen-parts-library-catalog-c-136_138/#320030023
320120007 | GSL009-5.0-02P-12 | DIP Female Blue; | Connector | 2P-5.0 | SENGER |  | 0.5 | 10 | 2 | 0.2 |  | http://www.seeedstudio.com/depot/OPLopen-parts-library-catalog-c-136_138/#320120007
320030100 | F185-1103A1BRYA1 | DIP Black Female Header; | Connector | 1*3P-2.54-8.5-90D | YXCON |  | 0.1 | 20 | 3 | 0.3 |  | http://www.seeedstudio.com/depot/OPLopen-parts-library-catalog-c-136_138/#320030100
320030035 | F185-1203A1BMYA1 | SMD Blue Female Header VERT | Connector | 2*3P-2.54-8.5mm | YXCON |  | 0.27 | 10 | 6 | 0.6 |  | http://www.seeedstudio.com/depot/OPLopen-parts-library-catalog-c-136_138/#320030035
320030011 | F185-1203A1BSYA1 | DIP Black Female Header VERT | Connector | 2*3P-2.54-8.5mm | YXCON |  | 0.2 | 10 | 6 | 0.6 |  | http://www.seeedstudio.com/depot/OPLopen-parts-library-catalog-c-136_138/#320030011
320030004 | F185-1106A1BSYA1 | DIP Blue Female Header VERT | Connector | 1*6P-2.54-8.5mm | YXCON |  | 0.2 | 10 | 6 | 0.6 |  | http://www.seeedstudio.com/depot/OPLopen-parts-library-catalog-c-136_138/#320030004
320030063 | F185-1106A1BSYA4 | DIP White Female Header | Connector | 1X6P-2.54-8.5 | YXCON |  | 0.2 | 10 | 6 | 0.6 |  | http://www.seeedstudio.com/depot/OPLopen-parts-library-catalog-c-136_138/#3460540P1
320030014 | F185-1106A1BRYA1 | DIP Black Female Header R/A; | Connector | 1*6P-2.54-8.5mm-90D | YXCON |  | 0.15 | 10 | 6 | 0.6 |  | http://www.seeedstudio.com/depot/OPLopen-parts-library-catalog-c-136_138/#320030014
320030003 | F185-1108A1BSYA1 | DIP Blue Female Header VERT | Connector | 1*8P-2.54-8.5mm | YXCON |  | 0.25 | 10 | 8 | 0.8 |  | http://www.seeedstudio.com/depot/OPLopen-parts-library-catalog-c-136_138/#320030003
320030064 | F185-1108A1BSYC1 | DIP White Female Header | Connector | 1X8P-2.54-8.5 | YXCON |  | 0.24 | 10 | 8 | 0.8 |  | http://www.seeedstudio.com/depot/OPLopen-parts-library-catalog-c-136_138/#3460550P1
320030076 | F185-AA08A2BRYA1 | DIP Black Female Header R/A; | Connector | 1*8P-2.54-8.5mm-90D | YXCON |  | 0.2 | 10 | 8 | 0.8 |  | http://www.seeedstudio.com/depot/OPLopen-parts-library-catalog-c-136_138/#320030076
320030020 | F243-1110A1BSUA2 | DIP White Female Header VERT; | Connector | 1*10P-2.0-4.3mm | YXCON |  | 0.27 | 10 | 10 | 1 |  | http://www.seeedstudio.com/depot/OPLopen-parts-library-catalog-c-136_138/#320030020
320030062 | F243-1110A1BSUC1 | DIP Blue Female Header | Connector | 1X10P-2.0-4.3 | YXCON |  | 0.25 | 10 | 10 | 1 |  | http://www.seeedstudio.com/depot/OPLopen-parts-library-catalog-c-136_138/#3460510P1
320030053 | F185-1110A1BRYA1 | DIP Black Female Header R/A | Connector | 1*10P-2.54-8.5mm-90D | YXCON |  | 0.2 | 10 | 10 | 1 |  | http://www.seeedstudio.com/depot/OPLopen-parts-library-catalog-c-136_138/#320030053
320070014 |  | DIP IC Socket; | Connector | 2*8P-2.54mm | NSTECH |  | 0.1 | 20 | 16 | 1.6 |  | http://www.seeedstudio.com/depot/OPLopen-parts-library-catalog-c-136_138/#320070014
320070007 |  | DIP IC Socket; | Connector | 2*9P-2.54mm | NSTECH |  | 0.15 | 10 | 18 | 1.8 |  | http://www.seeedstudio.com/depot/OPLopen-parts-library-catalog-c-136_138/#320070007
320170000 |  | SMD Battery Cell Holder Plastic | Connector | CR1220-15.06*13.00*H4.1mm |  |  | 0.35 | 10 | 4 | 0.4 |  | http://www.seeedstudio.com/depot/OPLopen-parts-library-catalog-c-136_138/#320170000
320110017 | DR-NP-04 Male | SMD Male DB9 Connector; | Connector | DSUB9+2P-2.77-90D-MALE | BEST |  | 0.2 | 10 | 11 | 1.1 |  | http://www.seeedstudio.com/depot/OPLopen-parts-library-catalog-c-136_138/#320110017
320090002 | VSHO-TF08-5501 | SMD SD Card Holder; | Connector | 8P-SMD-COVER | VSHOTECH |  | 0.25 | 10 | 8 | 0.8 |  | http://www.seeedstudio.com/depot/OPLopen-parts-library-catalog-c-136_138/#320090002
320170003 |  | DIP Battery Cell Holder; CR2032 | Connector | Metal CR2032-D20*H6.3mm | KEYUE |  | 0.06 | 20 | 4 | 0.4 |  | http://www.seeedstudio.com/depot/OPLopen-parts-library-catalog-c-136_138/#320170003
320100001 | ST-SIM-004B | SMD SIM Holder | Connector | 6P-L16.4*W16.3*H1.8mm | suntech |  | 0.27 | 10 | 6 | 0.6 |  | http://www.seeedstudio.com/depot/OPLopen-parts-library-catalog-c-136_138/#320100001
320010029 | VSHO-21-3301 | SMD TF+SIM-VSHO-21-3301; | Connector | 16P-L17.4*W16.5*H2.7mm | KQWI |  | 0.7 | 5 | 16 | 1.6 |  | http://www.seeedstudio.com/depot/OPLopen-parts-library-catalog-c-136_138/#320010029
320990008 | ST-HD-010G | Bare HDMI Male Connector; | Connector | White-3P | SUNTECH |  | 0.4 | 5 | 3 | 0.3 |  | http://www.seeedstudio.com/depot/OPLopen-parts-library-catalog-c-136_138/#320990008
320140010 | RJ45-MJ6-BX11-RVS1T073 | RJ45-MJ6-BX11-RVS1T073 | Connector | 6P-18.15*22.5*11.35 | HELING |  | 1.5 | 2 | 6 | 0.6 |  | http://www.seeedstudio.com/depot/OPLopen-parts-library-catalog-c-136_138/#320140010
304090054 | 504BC | DIP LED Transparent-Blue; | LED | Radial-2P-2.54-5mm | Chengguangxing |  | 0.068 | 30 | 2 | 0.2 |  | http://www.seeedstudio.com/depot/OPLopen-parts-library-catalog-c-136_138/#304090054
304090051 | UO504WC | DIP LED Transparent-Orange; | LED | Radial-2P-2.54-5mm | Chengguangxing |  | 0.068 | 30 | 2 | 0.2 |  | http://www.seeedstudio.com/depot/OPLopen-parts-library-catalog-c-136_138/#304090051
304090053 | 30SVC4A | DIP LED Clear-Purple; | LED | Radial-2P-2.54-3mm | Chengguangxing |  | 0.068 | 30 | 2 | 0.2 |  | http://www.seeedstudio.com/depot/OPLopen-parts-library-catalog-c-136_138/#304090053
304090056 | FZR50RGB00T-C | DIP LED RGB Common Anode; | LED | Radial-4P-2.0-5.0mm | CHENGGUANGXING |  | 0.35 | 10 | 2 | 0.2 |  | http://www.seeedstudio.com/depot/OPLopen-parts-library-catalog-c-136_138/#304090056
304090049 | 5050RGB | SMD RGB Hi-Light | Diode | 6P-L5.0*W5.0*H1.5mm | CHENGGUANGXING |  | 0.28 | 10 | 6 | 0.6 |  | http://www.seeedstudio.com/depot/OPLopen-parts-library-catalog-c-136_138/#304090049
304060003 | CESD3V3AP | SMD Diode ESD 3.3V-225mW; | Diode | SOT-23 | JCET |  | 0.08 | 25 | 2 | 0.2 |  | http://www.seeedstudio.com/depot/OPLopen-parts-library-catalog-c-136_138/#304060003
304020016 | BAT54C-215 | SMD Diode Schottky 30V-200mA | Diode | SOT-23 | NXP |  | 0.02 | 50 | 3 | 0.3 |  | http://www.seeedstudio.com/depot/OPLopen-parts-library-catalog-c-136_138/#304020016
307010010 | SMD1210R075SF | SMD PPTC 750mA-6V | Fuse | 1210 | Darong |  | 0.15 | 20 | 2 | 0.2 |  | http://www.seeedstudio.com/depot/OPLopen-parts-library-catalog-c-136_138/#307010010
307010007 | SMD1812R500SF | SMD PPTC-500mA-15V | Fuse | 1812 | TIANRUI |  | 0.12 | 20 | 2 | 0.2 |  | http://www.seeedstudio.com/depot/OPLopen-parts-library-catalog-c-136_138/#0900390P1
310010023 | ATMEGA8A-AU | IC MCU 8Bit 8KB ISP Flash 512B EEPROM 1KB SRAM 16MHz 2.7v-5.5v | IC | TQFP-32 | Atmel |  | 1.8 | 2 | 8 | 0.8 |  | http://www.seeedstudio.com/depot/OPLopen-parts-library-catalog-c-136_138/#310010023
310030006 | LM317EMP | SMD PMIC;LDO;Vin 40V;Adj;1A;Without En;1-Ch | IC | SOT-223 | TI |  | 1 | 2 | 5 | 0.5 |  | http://www.seeedstudio.com/depot/OPLopen-parts-library-catalog-c-136_138/#310030006
310050019 | SN74LVC1G125DCKR | SMD IC Logic | IC | SC-70-5 | TI |  | 0.1 | 20 | 2 | 0.2 |  | http://www.seeedstudio.com/depot/OPLopen-parts-library-catalog-c-136_138/#310050019
310040002 | TM1636 | DIP IC Driver; | IC | DIP-18 | TITAN |  | 0.25 | 10 | 18 | 1.8 |  | http://www.seeedstudio.com/depot/OPLopen-parts-library-catalog-c-136_138/#310040002
310040021 | RT9167A-33PB | SMD IC Driver; | IC | SOT23-5 | RichTek |  | 0.25 | 10 | 4 | 0.4 |  | http://www.seeedstudio.com/depot/OPLopen-parts-library-catalog-c-136_138/#310040021
310020019 | LMV324IDR | SMD IC Amplifier; IC OPAMP GP R-R 1MHZ QUAD | IC | 14-SOIC | Texas Instruments |  | 0.22 | 10 | 14 | 1.4 |  | http://www.seeedstudio.com/depot/OPLopen-parts-library-catalog-c-136_138/#1100030P1
310070024 | MCP2551-I/SN | SMD IC Interface | IC | 8-SOIC | Microchip |  | 0.8 | 3 | 3 | 0.3 |  | http://www.seeedstudio.com/depot/OPLopen-parts-library-catalog-c-136_138/#310070024
310070025 | MCP2515T-I/SO | SMD IC Interface; | IC | 18-SOIC | Microchip |  | 1 | 3 | 6 | 0.6 |  | http://www.seeedstudio.com/depot/OPLopen-parts-library-catalog-c-136_138/#310070025
310110010 | DS1307ZN | IC RTC SERIAL 512K IND | IC | 8-SOIC | Maxim Integrated |  | 1.3 | 2 | 8 | 0.8 |  | http://www.seeedstudio.com/depot/OPLopen-parts-library-catalog-c-136_138/#1900100P1
310110008 | DS1337S+ | SMD IC Clock/Timing | IC | SOIC-8 | Maxim Integrated |  | 1 | 3 | 8 | 0.8 |  | http://www.seeedstudio.com/depot/OPLopen-parts-library-catalog-c-136_138/#310110008
303010015 | SPD3D16-4R7M | SMD Power Inductor 4.7uH-20%-750mA | Inductor | SMD-2P-3.9X3.9X2.0H | CODACA |  | 0.4 | 5 | 2 | 0.2 |  | http://www.seeedstudio.com/depot/OPLopen-parts-library-catalog-c-136_138/#0210410P1
308020000 | LY190-128064 | OLED-128*64;27P-0.6-L26.7*W19.26*H1.3mm | Display | 128*64;27P-0.6-L26.7*W19.26*H1.3mm | Liyuan |  | 5 | 1 | 0 | 0 |  | http://www.seeedstudio.com/depot/OPLopen-parts-library-catalog-c-136_138/#308020000
301010076 | RC0402JR-071R5L | SMD RES 1.5R-5%-1/16W | Resistor | 0402 | YAGEO |  | 0.01 | 100 | 2 | 0.2 |  | http://www.seeedstudio.com/depot/OPLopen-parts-library-catalog-c-136_138/#301010076
301010231 | RC0603JR-0715RL | SMD RES 15R-5%-1/10W;0603 | Resistor | 0603 | YAGEO |  | 0.01 | 100 | 2 | 0.2 |  | http://www.seeedstudio.com/depot/OPLopen-parts-library-catalog-c-136_138/#301010231
301010326 | RC0805JR-0768RL | SMD RES 68R-5%-1/8W | Resistor | 0805 | YAGEO |  | 0.01 | 100 | 2 | 0.2 |  | http://www.seeedstudio.com/depot/OPLopen-parts-library-catalog-c-136_138/#301010326
301010085 | RC0603JR-0768RL | SMD RES 68R-5%-1/10W | Resistor | 0603 | YAGEO |  | 0.025 | 50 | 2 | 0.2 |  | http://www.seeedstudio.com/depot/OPLopen-parts-library-catalog-c-136_138/#301010085
301010294 | RC0603JR-0775RL | SMD RES 75R-5%-1/10W | Resistor | 0603 | YAGEO |  | 0.01 | 100 | 2 | 0.2 |  | http://www.seeedstudio.com/depot/OPLopen-parts-library-catalog-c-136_138/#0010220P1
301010351 | RC0805JR-07120RL | SMD RES 120R-5%-1/8W | Resistor | 0805 | YAGEO |  | 0.01 | 100 | 2 | 0.2 |  | http://www.seeedstudio.com/depot/OPLopen-parts-library-catalog-c-136_138/#301010351
301010320 | RC0805JR-07390RL | SMD RES 390R-5%-1/8W | Resistor | 0805 | YAGEO |  | 0.01 | 100 | 2 | 0.2 |  | http://www.seeedstudio.com/depot/OPLopen-parts-library-catalog-c-136_138/#301010320
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
