marukitano/BEP3.0/BEP33/BEP33_2panel_test.dxf

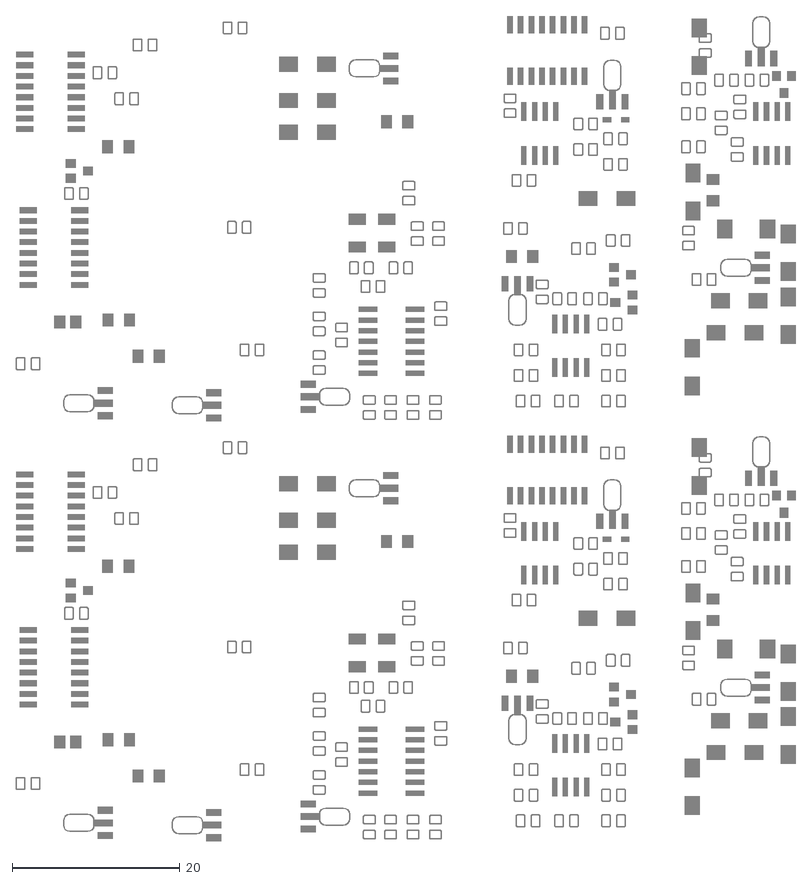
[picture p49: CAD file, 2026-10-06]
BEP33/BEP33_2panel_test.dxf
92.9 x 98.3
