marukitano/BEP3.0/Brotbox original/Ganganzeige/Ganganzeige_nutzen_maske.dxf

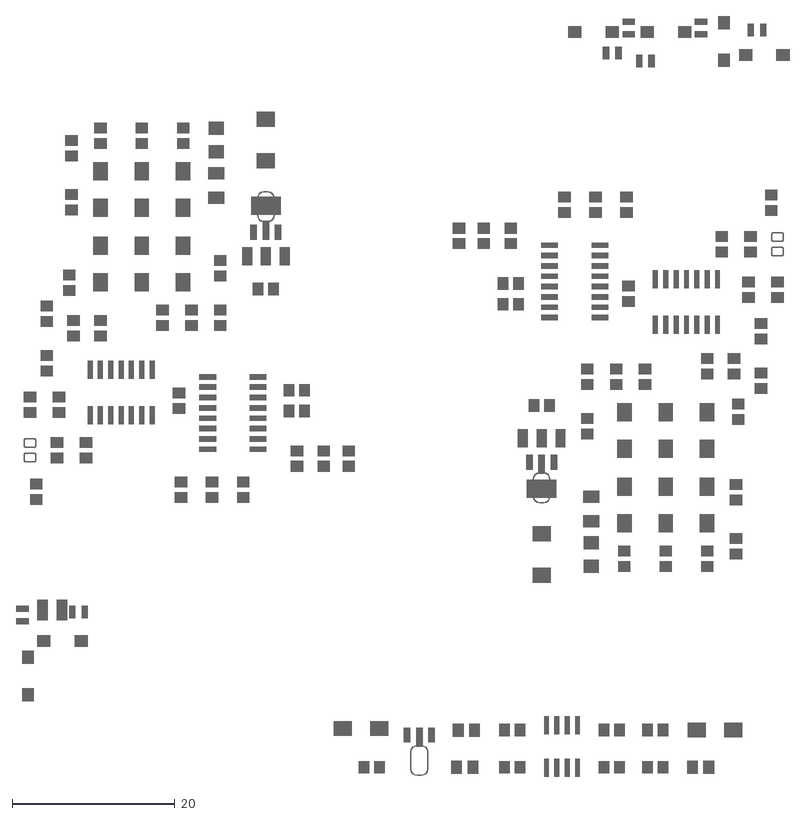
[picture p50: CAD file, 2026-10-06]
Brotbox original/Ganganzeige/Ganganzeige_nutzen_maske.dxf
94.9 x 93.4
