marukitano/BEP3.0/BEP3/BEP3_RPM_BAR.dxf

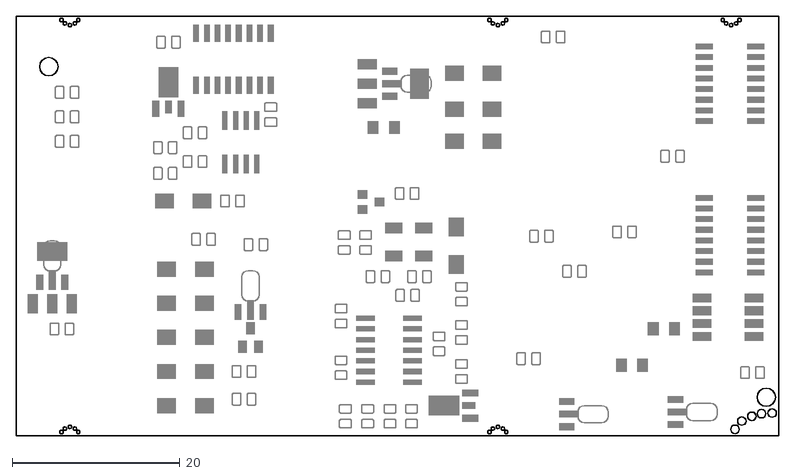
[picture p53: CAD file, 2026-10-06]
BEP3/BEP3_RPM_BAR.dxf
90.9 x 50.0
