marukitano/BEP3.0/BEP33/Ganganzeige_maske_bearb .dxf

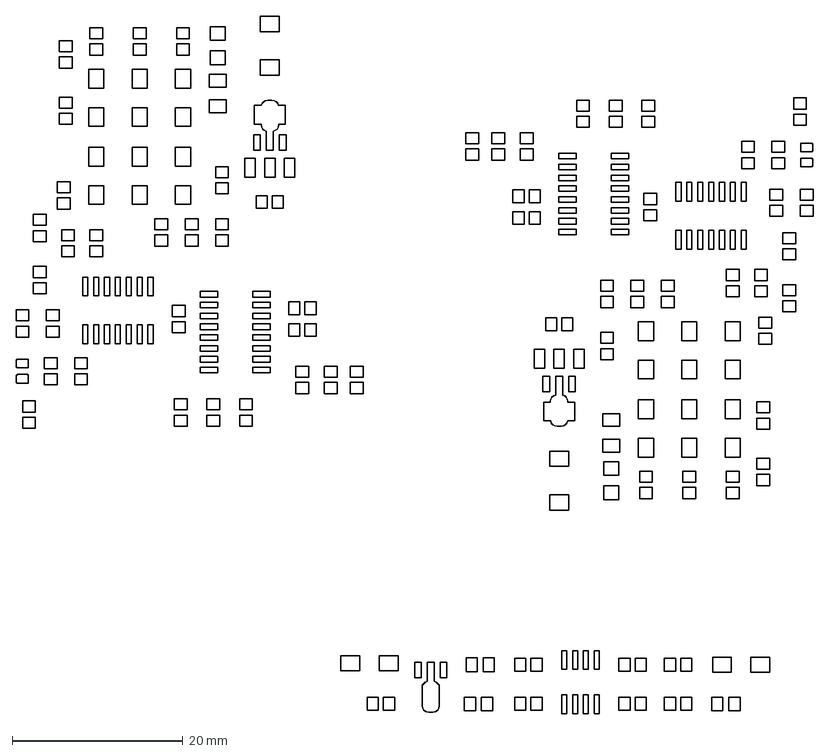
[picture p54: CAD file, 2026-10-06]
BEP33/Ganganzeige_maske_bearb .dxf
93.3 x 81.6 mm
