marukitano/BEP3.0/Brotbox original/Ganganzeige/Ganganzeige_nutzen_maske_bearb.dxf

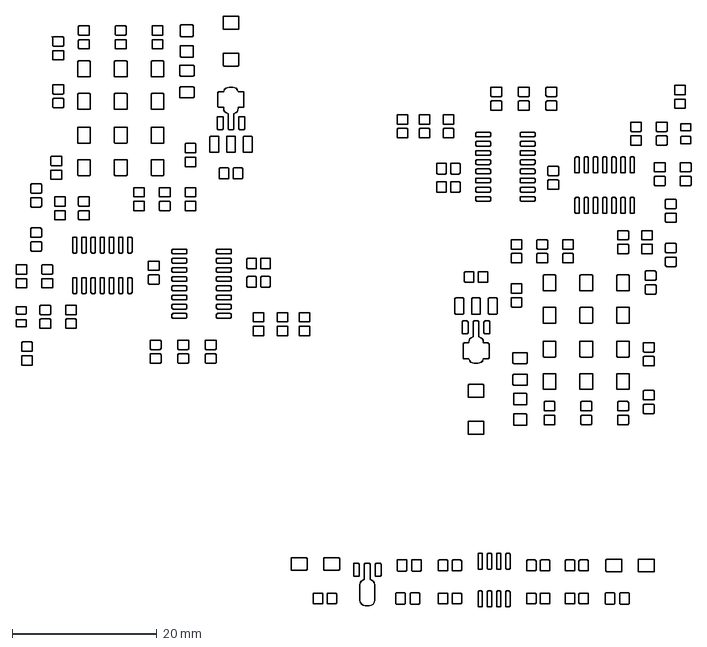
[picture p55: CAD file, 2026-10-06]
Brotbox original/Ganganzeige/Ganganzeige_nutzen_maske_bearb.dxf
93.3 x 81.6 mm
