marukitano/BEP3.0/Nixie1_kicad/Ganganzeige-F_Cu.dxf

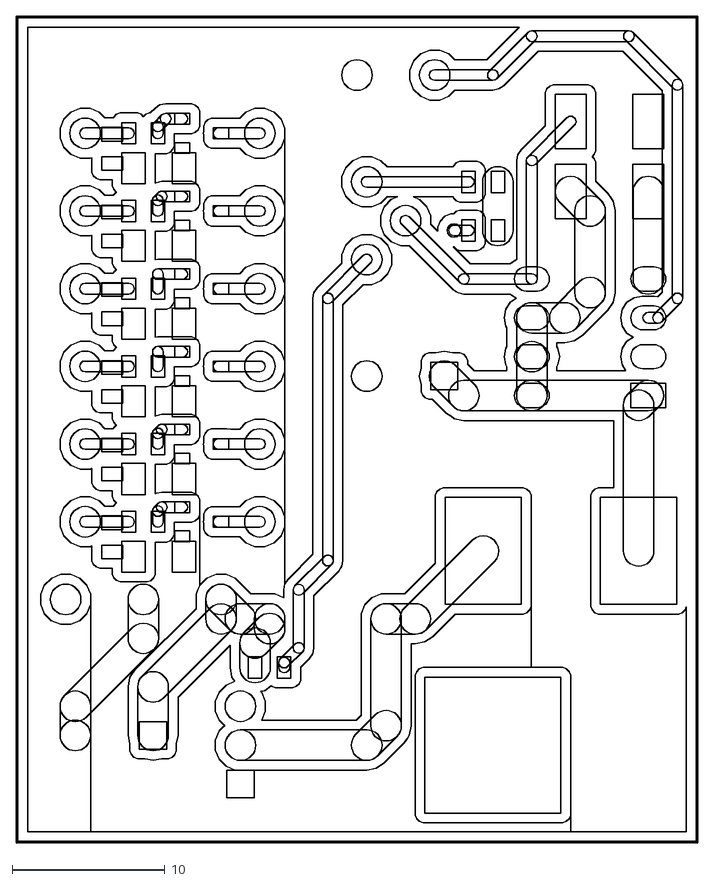
[picture p56: CAD file, 2026-10-06]
Nixie1_kicad/Ganganzeige-F_Cu.dxf
44.6 x 54.1
