marukitano/BEP3.0/BEP3 Test-Interface/BEP3_Test_Interface3.dxf

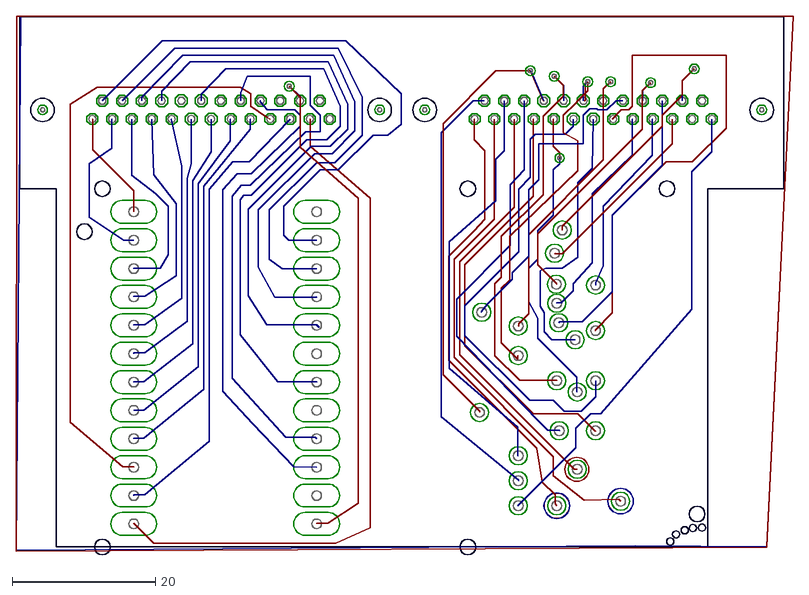
[picture p57: CAD file, 2026-10-06]
BEP3 Test-Interface/BEP3_Test_Interface3.dxf
108.4 x 75.2
