marukitano/BEP3.0/BEP33/BEP33_2panel_test_plus Ganganzeige_maske_bearb.dxf

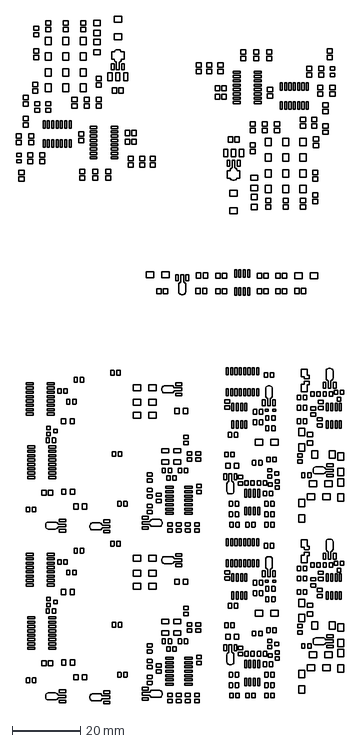
[picture p58: CAD file, 2026-10-06]
BEP33/BEP33_2panel_test_plus Ganganzeige_maske_bearb.dxf
95.8 x 201.2 mm
