marukitano/BEP3.0/BEP2 final/dxf/BMW_final_Bohrlöcher.dxf

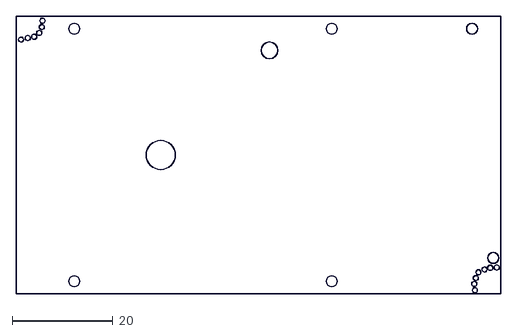
[picture p59: CAD file, 2026-10-06]
BEP2 final/dxf/BMW_final_Bohrlöcher.dxf
96.0 x 55.0
