marukitano/BEP3.0/BEP2 final/dxf/BMW_final_ohneLInienbreite.dxf

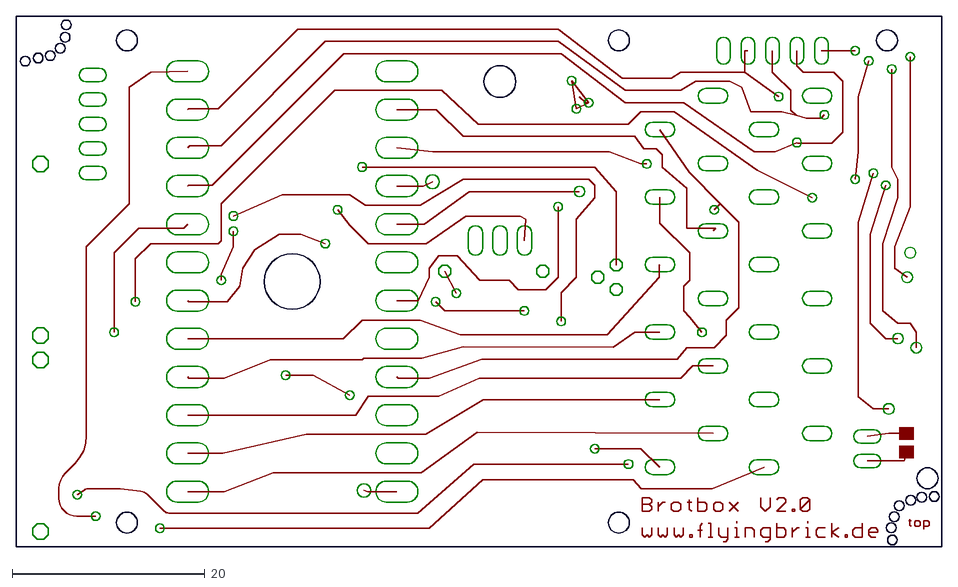
[picture p61: CAD file, 2026-10-06]
BEP2 final/dxf/BMW_final_ohneLInienbreite.dxf
96.0 x 55.0
