marukitano/BEP3.0/BEP2 final/dxf/BMW_final_bottom_mitLinienbreite.dxf

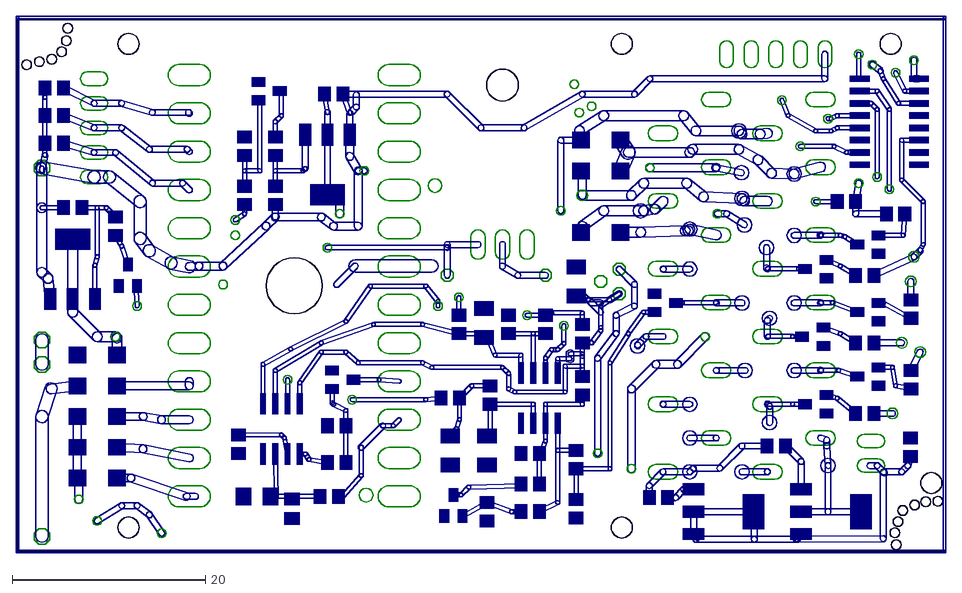
[picture p62: CAD file, 2026-10-06]
BEP2 final/dxf/BMW_final_bottom_mitLinienbreite.dxf
96.1 x 55.5
