marukitano/BEP3.0/BEP2 final/dxf/BMW_final_vias.dxf

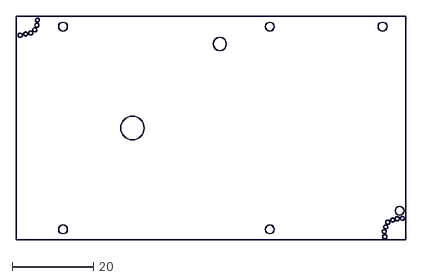
[picture p63: CAD file, 2026-10-06]
BEP2 final/dxf/BMW_final_vias.dxf
96.0 x 55.0
