marukitano/BEP3.0/BEP2 final/dxf/BMW_final_mitLinienbreite.dxf

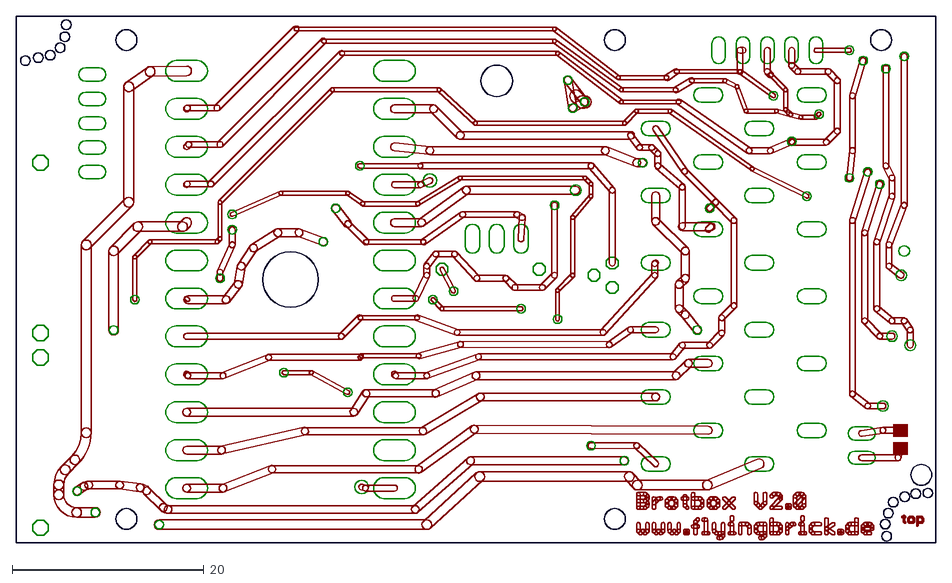
[picture p65: CAD file, 2026-10-06]
BEP2 final/dxf/BMW_final_mitLinienbreite.dxf
96.0 x 55.0
