marukitano/BEP3.0/BEP2 final/dxf/BMW_final_pads.dxf

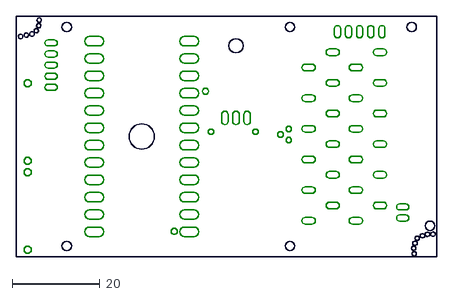
[picture p66: CAD file, 2026-10-06]
BEP2 final/dxf/BMW_final_pads.dxf
96.0 x 55.0
