marukitano/BEP3.0/BEP2 final/dxf/BMW_final_bottom_MittelpunktederBauteile.dxf

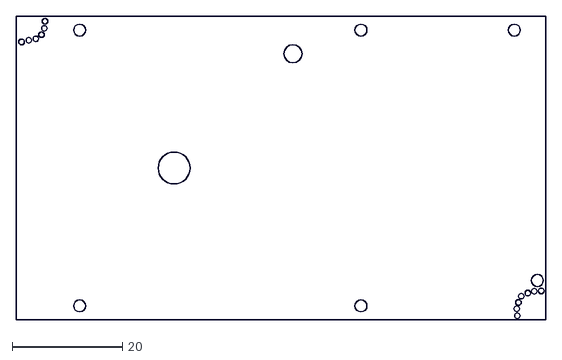
[picture p67: CAD file, 2026-10-06]
BEP2 final/dxf/BMW_final_bottom_MittelpunktederBauteile.dxf
96.0 x 55.0
