marukitano/BEP3.0/BEP32/BEP32 how to order stencil with seeedstudio.PNG

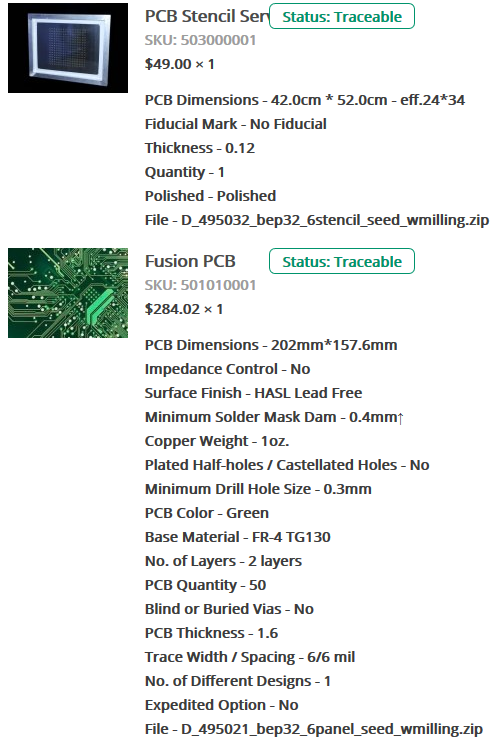
BEP32/BEP32 how to order stencil with seeedstudio.PNG
