marukitano/BEP3.0/BEP33/Bestellung Bep33 bei seedstudio how to.PNG

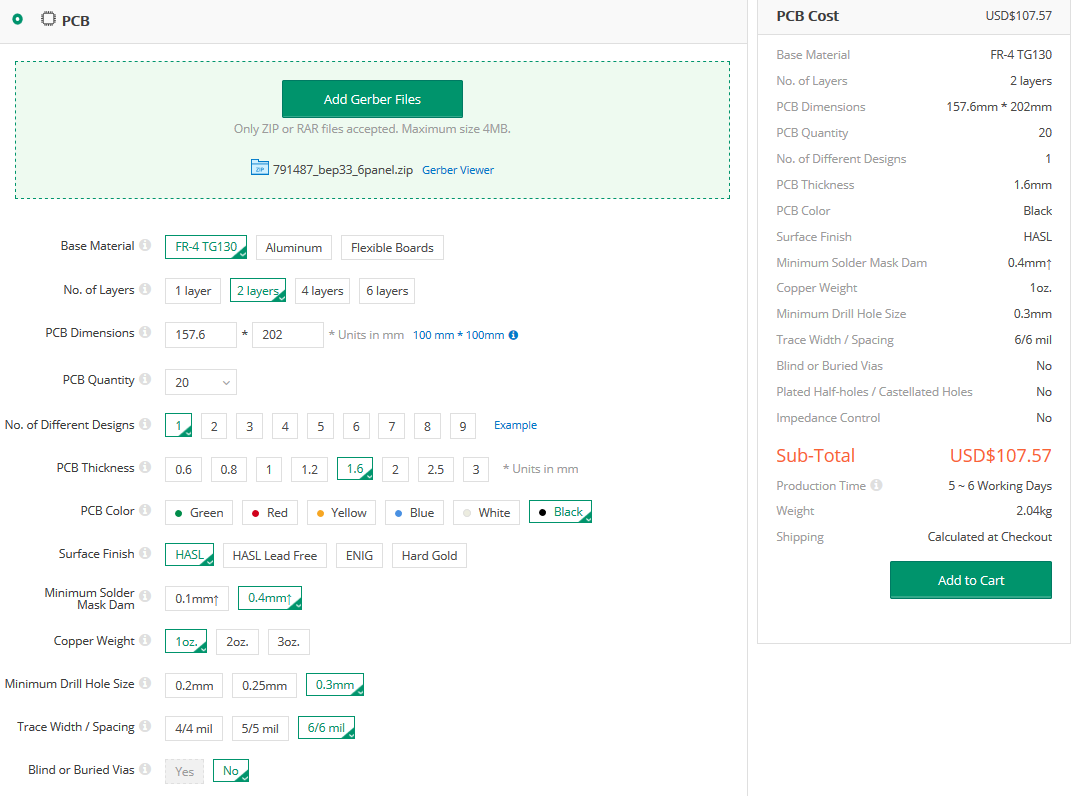
BEP33/Bestellung Bep33 bei seedstudio how to.PNG
