marukitano/BEP3.0/BEP33/Seedstudio how to order stencil.PNG

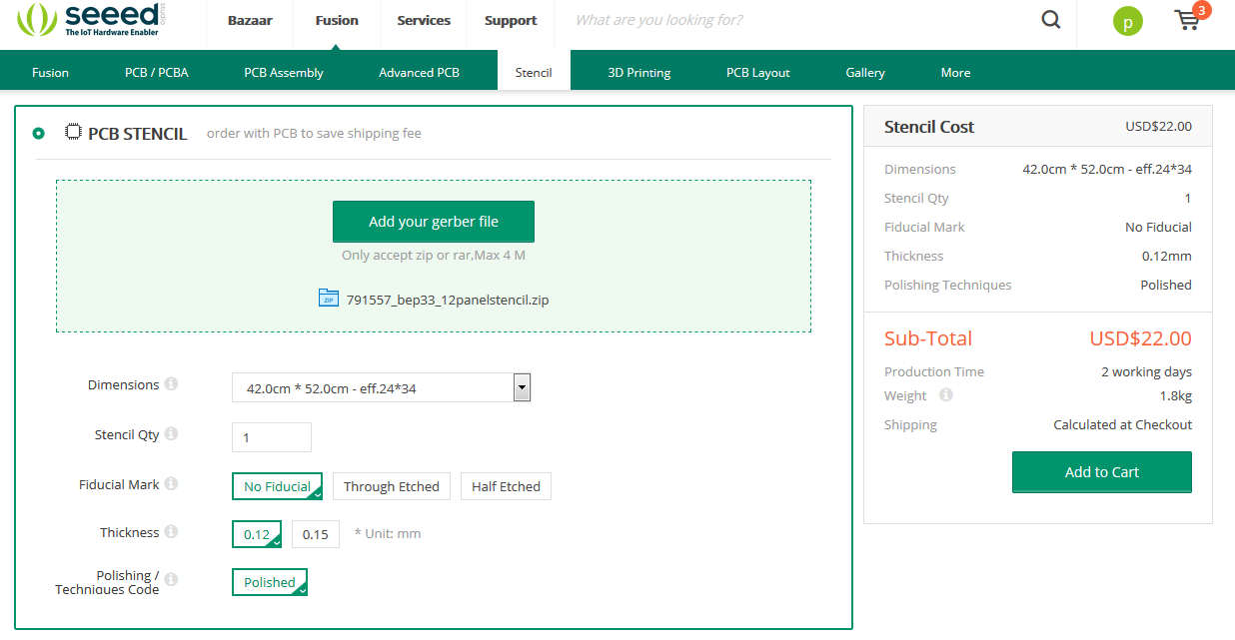
BEP33/Seedstudio how to order stencil.PNG
