marukitano/BEP3.0/Brotbox original/Tachoverstärker/Screenshot_Eagle Setup.png

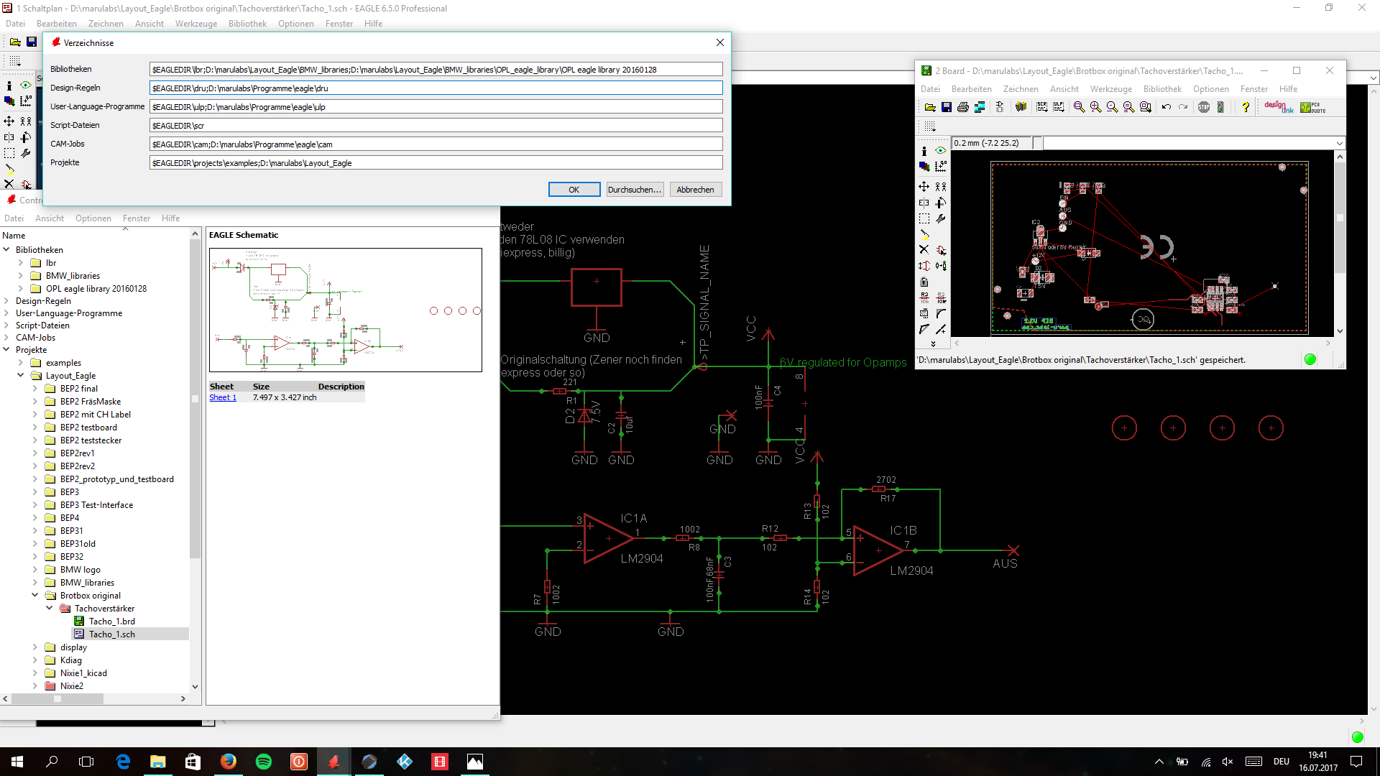
Brotbox original/Tachoverstärker/Screenshot_Eagle Setup.png
