marukitano/BEP3.0/BEP2_prototyp_und_testboard/Main und Testboard übereinandergelegt.png

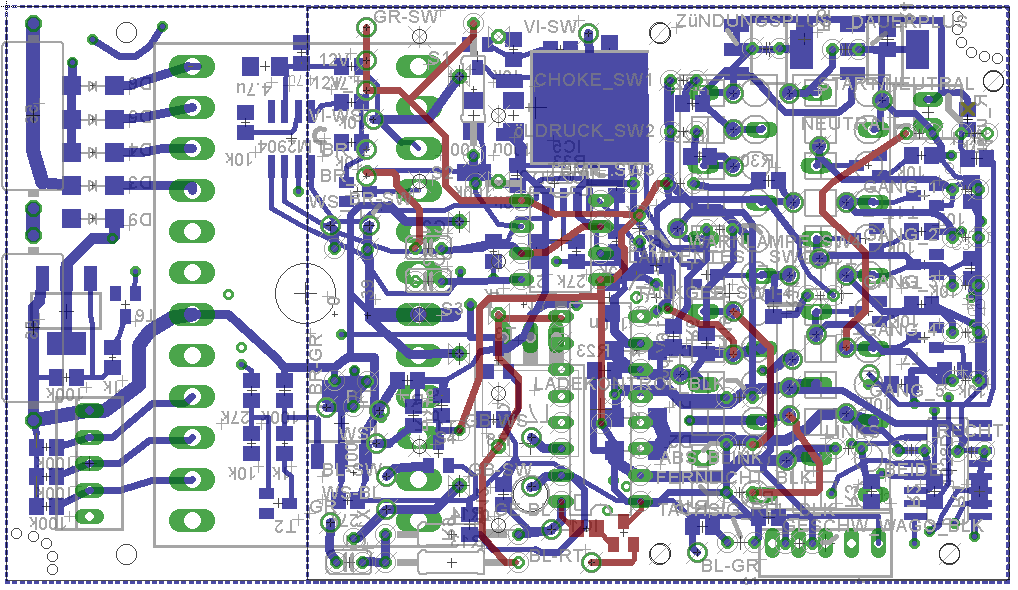
BEP2_prototyp_und_testboard/Main und Testboard übereinandergelegt.png
