marukitano/BEP3.0/BEP3 Test-Interface/Interface.png

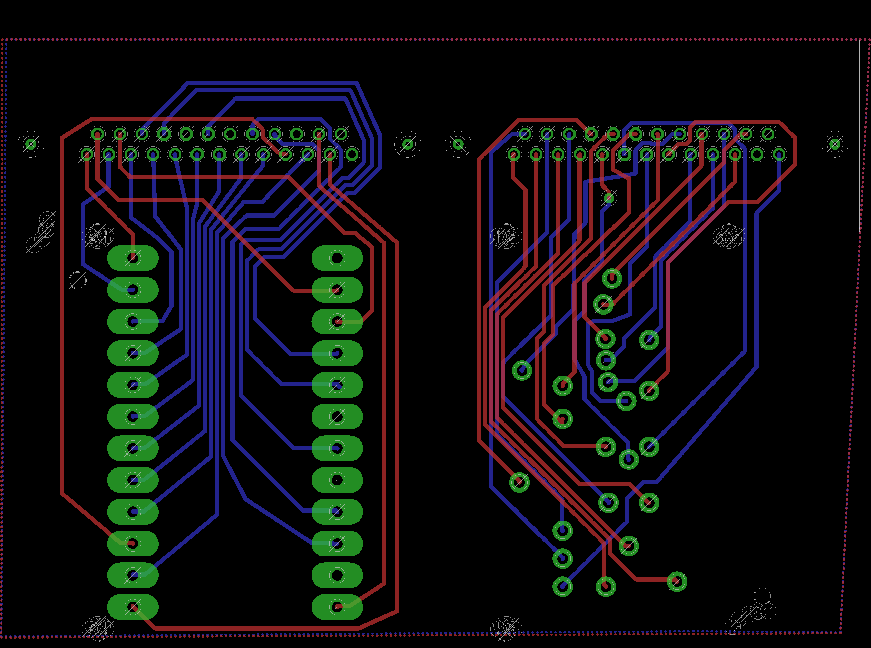
BEP3 Test-Interface/Interface.png
