marukitano/BEP3.0/BEP3 Test-Interface/LPC2148neu/LPC2148_lowside.jpg

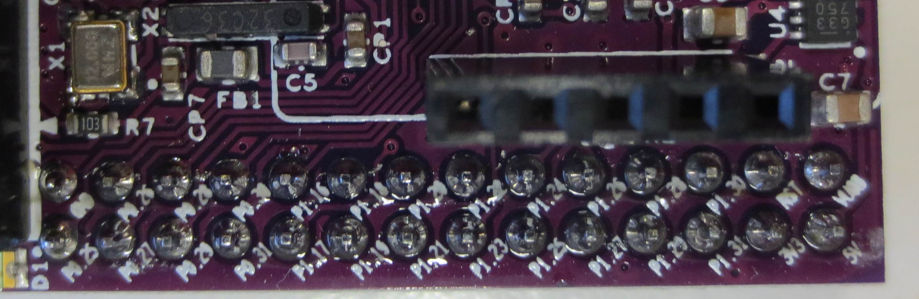
BEP3 Test-Interface/LPC2148neu/LPC2148_lowside.jpg
