marukitano/BEP3.0/BEP33/BEP33_2panel_test_plus Ganganzeige_maske_bearb linie 0.5mm.png

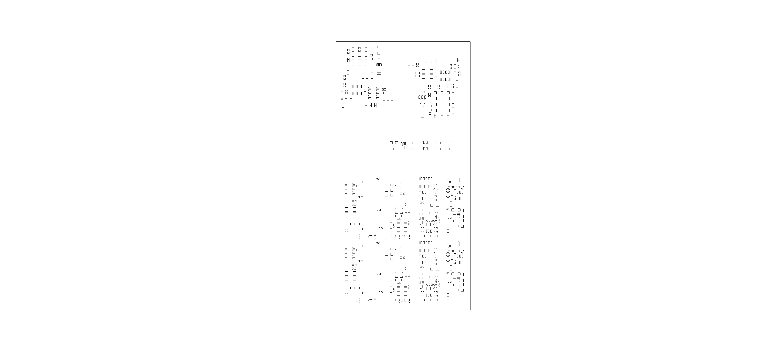
BEP33/BEP33_2panel_test_plus Ganganzeige_maske_bearb linie 0.5mm.png
