marukitano/BEP3.0/BEP31/BEP31_Schema.pdf

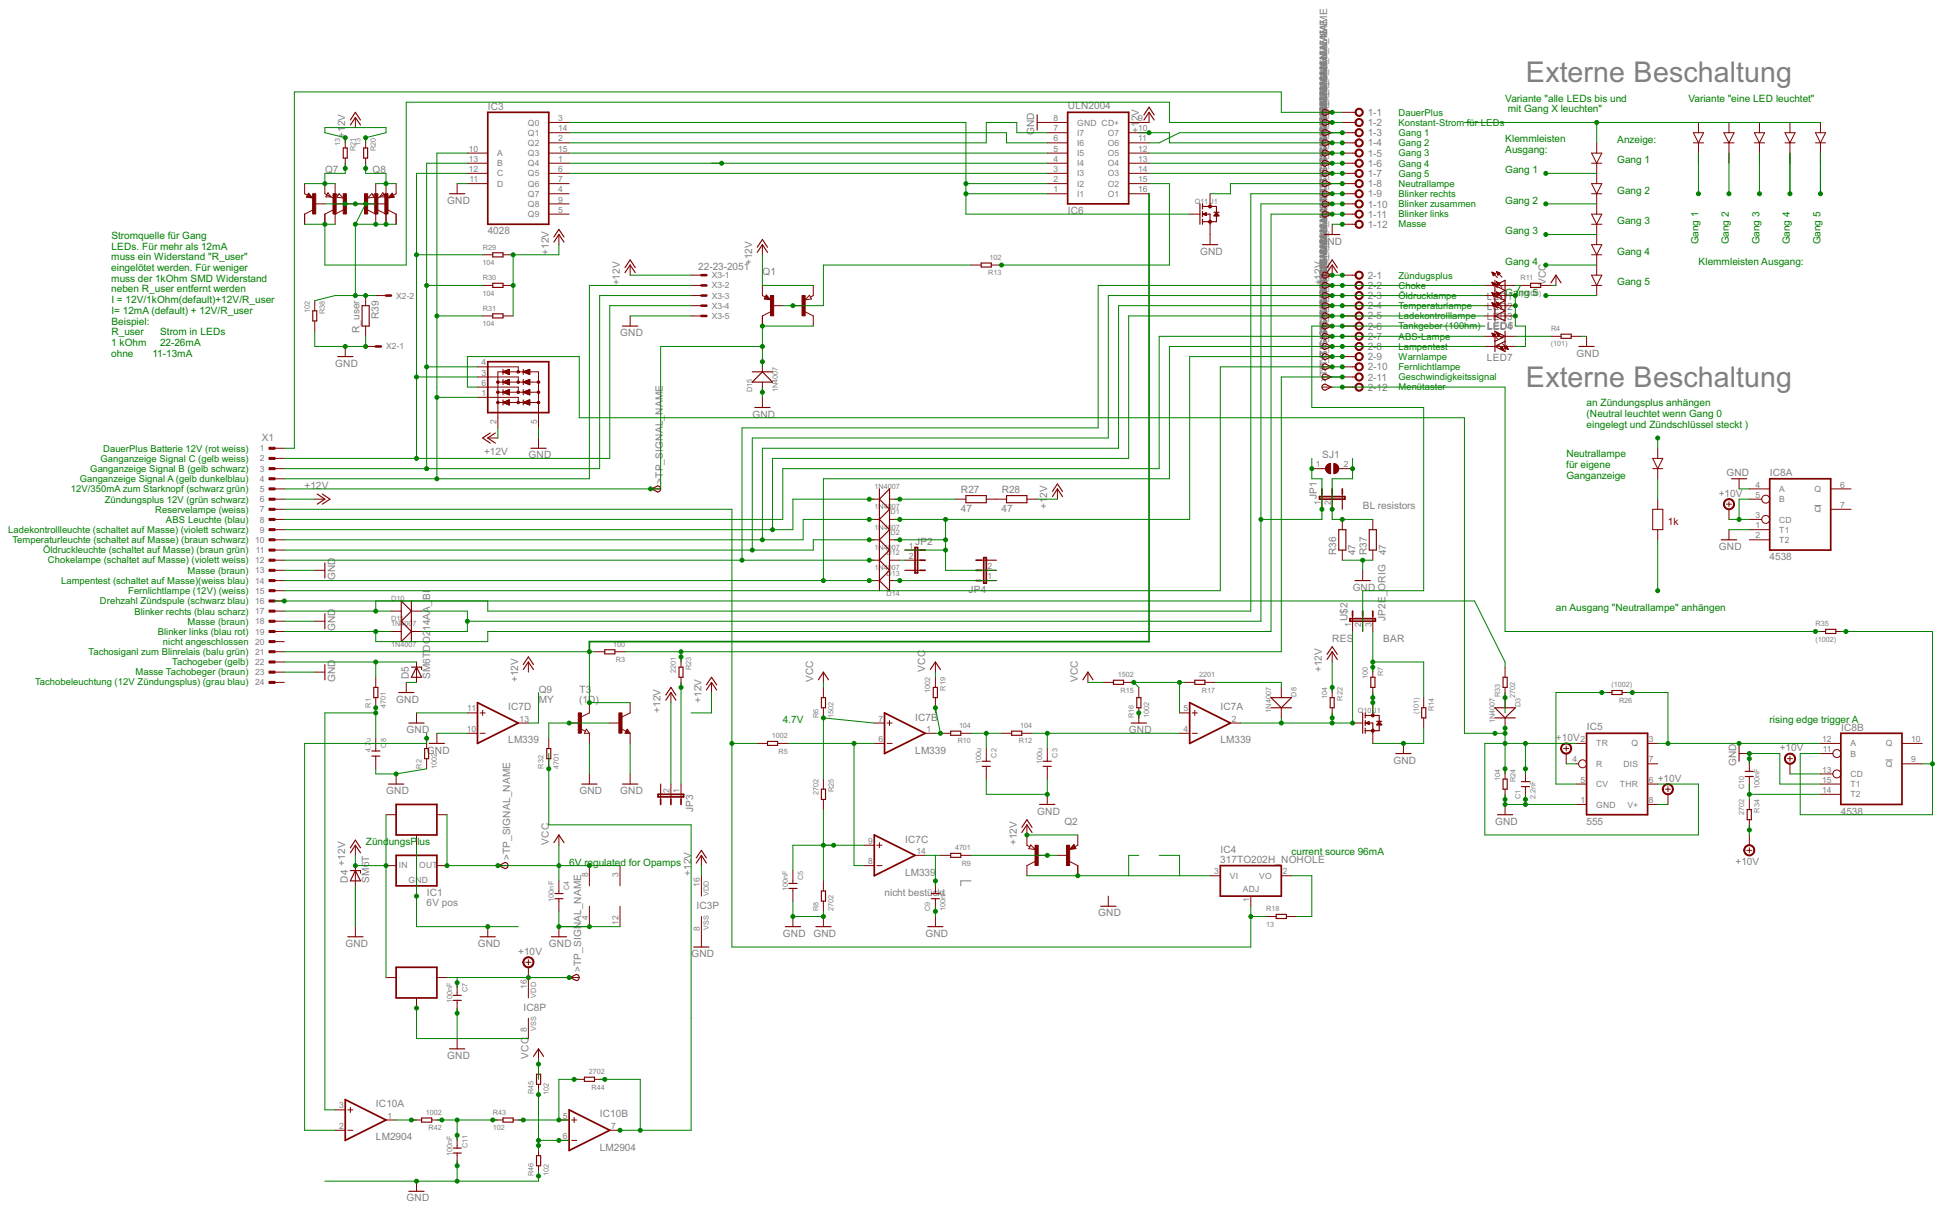
[picture p79: page 1]

DauerPlus Konstant-Strom für LEDs Gang 1 Gang 2 Gang 3 Gang 4 Gang 5 Neutrallampe Blinker rechts Blinker zusammen Blinker links Masse

Stromquelle für Gang
LEDs. Für mehr als 12mA muss ein Widerstand "R_user" eingelötet werden. Für weniger muss der 1kOhm SMD Widerstand

Zündugsplus Choke Öldrucklampe Temperaturlampe

LED1

2-4 LED2 2-5

Ladekontrolllampe Tankgeber (100hm) ABS-Lampe

Lampentest Warnlampe Fernlichtlampe Geschwindigkeitssignal Menütaster

an Zündungsplus anhängen
(Neutral leuchtet wenn Gang 0
eingelegt und Zündschlüssel steckt )

an Ausgang "Neutrallampe" anhängen
