marukitano/BEP3.0/BEP32/BEP32_Schaltplan.pdf

Gear Decoder | Transistor Driver Array

# WAGO Klemmleiste

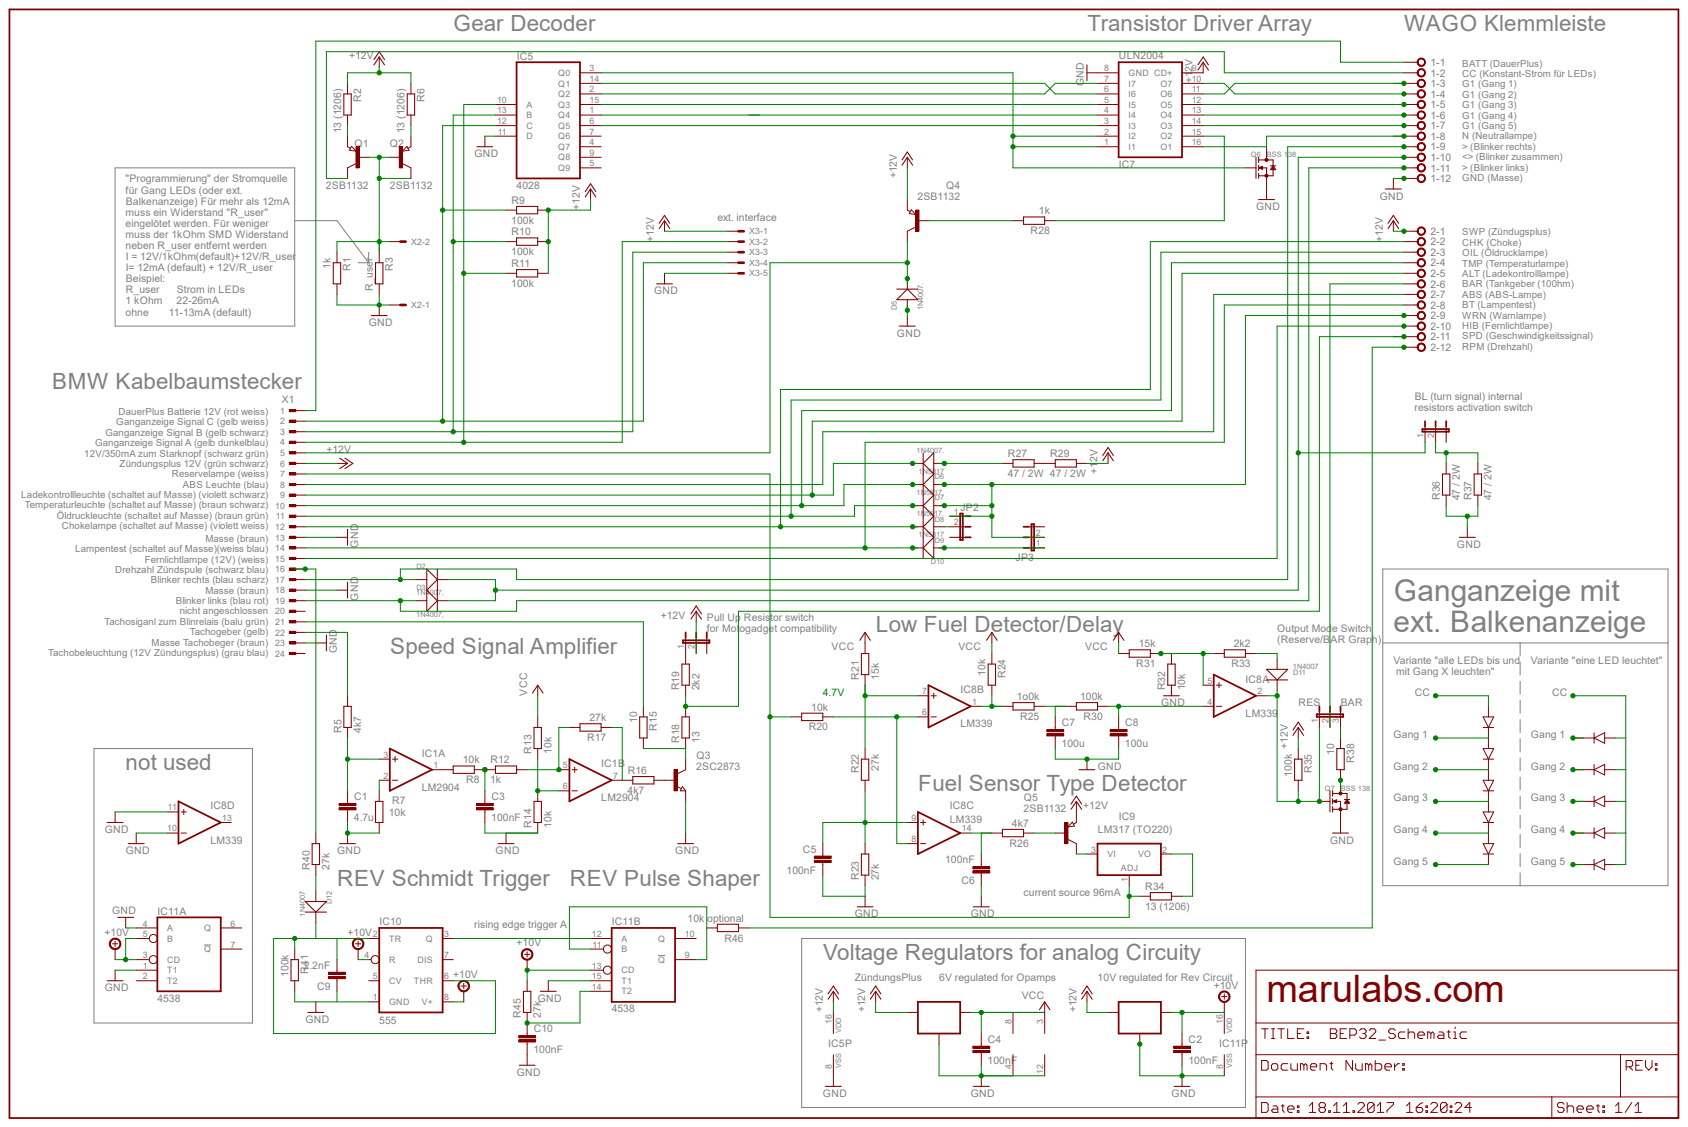
[picture p80: page 1]

10 D | | | I4 4
12 B | | | I3 3
11 C | | | I2 2

"Programmierung" der Stromquelle
für Gang LEDs (oder ext.
Balkenanzeige) Für mehr als 12mA
muss ein Widerstand "R_user"
eingelötet werden. Für weniger
muss der 1kOhm SMD Widerstand
neben R_user entfernt werden
I = 12V/1kOhm(default)+12V/R_user
I= 12mA (default) + 12V/R_user
Beispiel:

BL (turn signal) internal
resistors activation switch

DauerPlus Batterie 12V (rot weiss)
Ganganzeige Signal C (gelb weiss)
Ganganzeige Signal B (gelb schwarz)
Ganganzeige Signal A (gelb dunkelblau)
12V/350mA zum Starknopf (schwarz grün)

Ladekontrollleuchte (schaltet auf Masse) (violett schwarz)
Temperaturleuchte (schaltet auf Masse) (braun schwarz) Öldruckleuchte (schaltet auf Masse) (braun grün)

Chokelampe (schaltet auf Masse) (violett weiss)

Lampentest (schaltet auf Masse)(weiss blau)

Fernlichtlampe (12V) (weiss)
Drehzahl Zündspule (schwarz blau)

Blinker rechts (blau scharz)
Blinker links (blau rot)
nicht angeschlossen
Tachogeber (gelb)

Pull Up Resistor switch
for Motogadget compatibility

Tachosiganl zum Blinrelais (balu grün)

Tachobeleuchtung (12V Zündungsplus) (grau blau)

Variante "alle LEDs bis und Variante "eine LED leuchtet"
mit Gang X leuchten"

Fuel Sensor Type Detector

GND
REV Schmidt Trigger REV Pulse Shaper

Voltage Regulators for analog Circuity

10V regulated for Rev Circuit
