marukitano/BEP3.0/BEP4/BEP4.0 Schaltplan.pdf

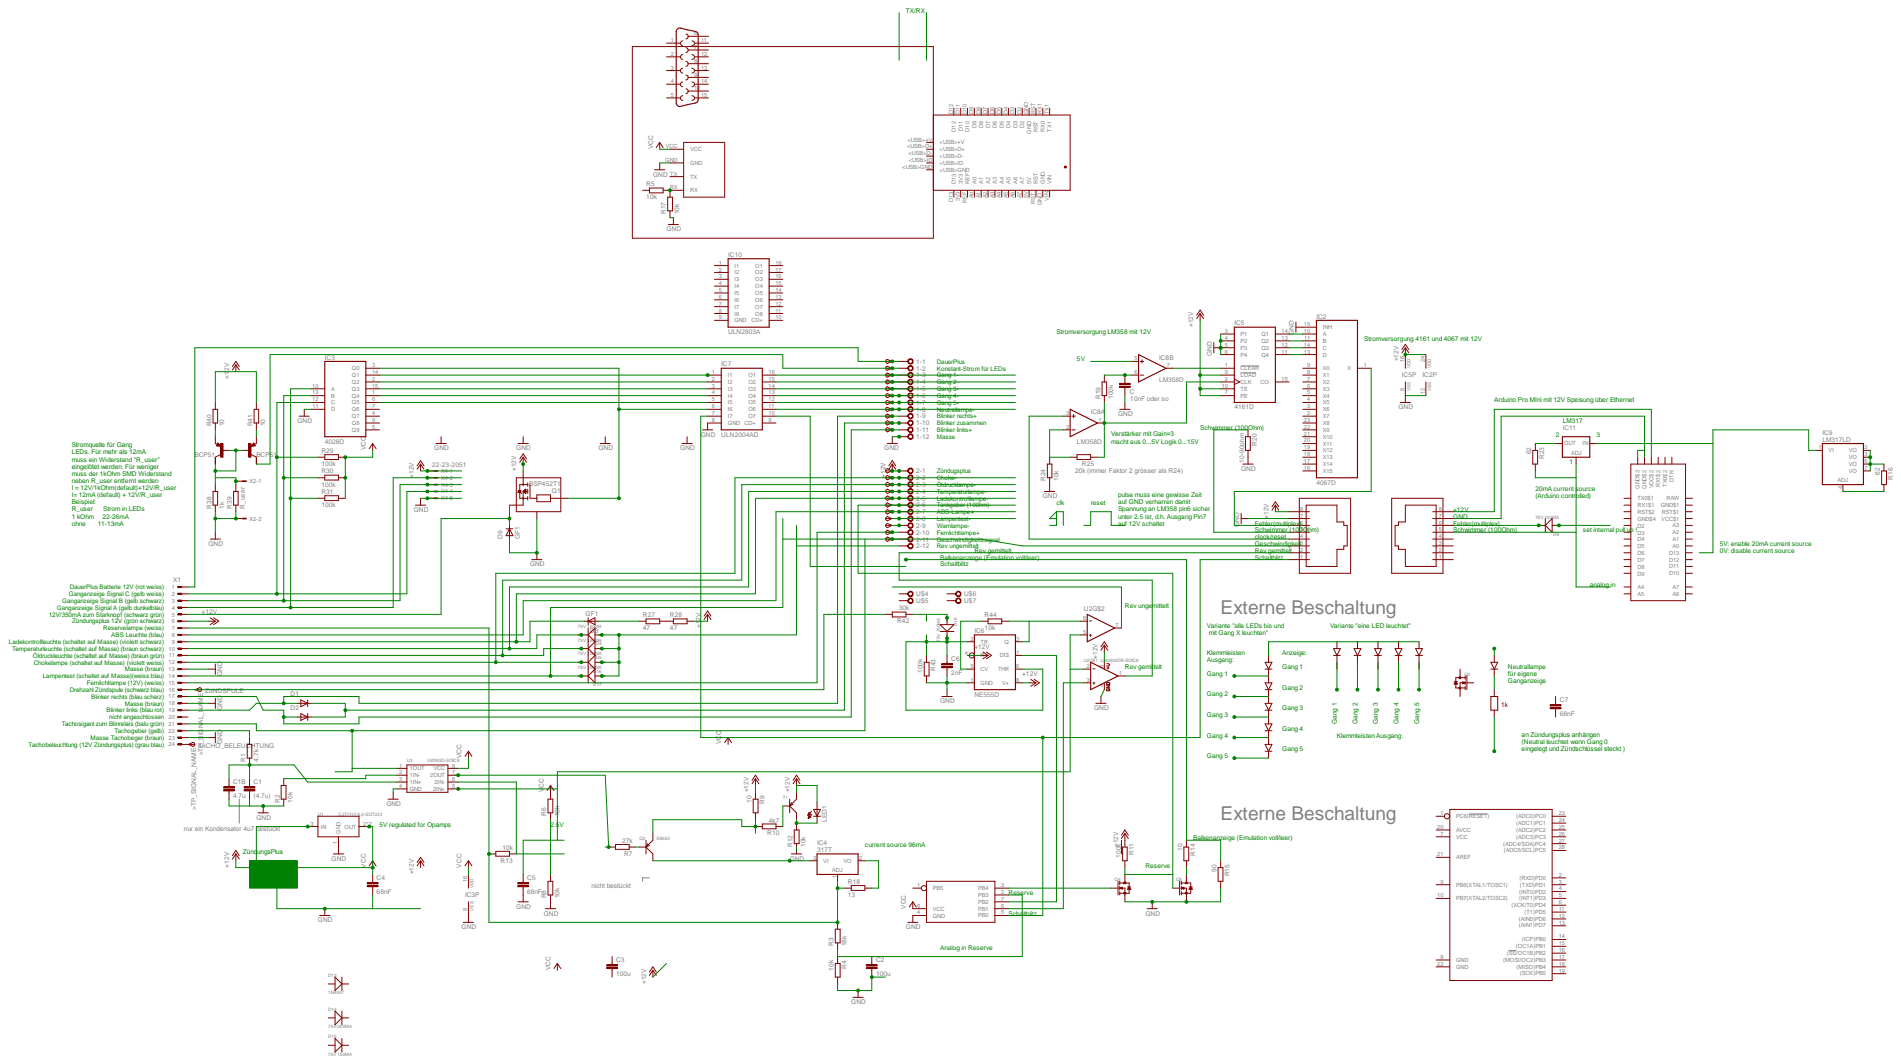
[picture p81: page 1]

<USB>ID
<USB>GND

Konstant-Strom für LEDs

Arduino Pro MIni mit 12V Speisung über Ethernet

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

10k20k (immer Faktor 2 grösser als R24)

pulse muss eine gewisse Zeit
auf GND verharren damit
Spannung an LM358 pin6 sicher
unter 2.5 ist, d.h. Ausgang Pin7
auf 12V schaltet

set internal pull up !

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

Ladekontrollleuchte (schaltet auf Masse) (violett schwarz)
Temperaturleuchte (schaltet auf Masse) (braun schwarz)

Öldruckleuchte (schaltet auf Masse) (braun grün)
Chokelampe (schaltet auf Masse) (violett weiss)

Lampentest (schaltet auf Masse)(weiss blau)

Fernlichtlampe (12V) (weiss)
Drehzahl Zündspule (schwarz blau)
Blinker rechts (blau scharz)

Masse (braun)
Blinker links (blau rot)
nicht angeschlossen

Tachosiganl zum Blinrelais (balu grün)

Tachobeleuchtung (12V Zündungsplus) (grau blau)

(Neutral leuchtet wenn Gang 0
eingelegt und Zündschlüssel steckt )

nur ein Kondensator 4u7 bestückt

Balkenanzeige (Emulation voll/leer)
