marukitano/BEP3.0/Adapter.pdf

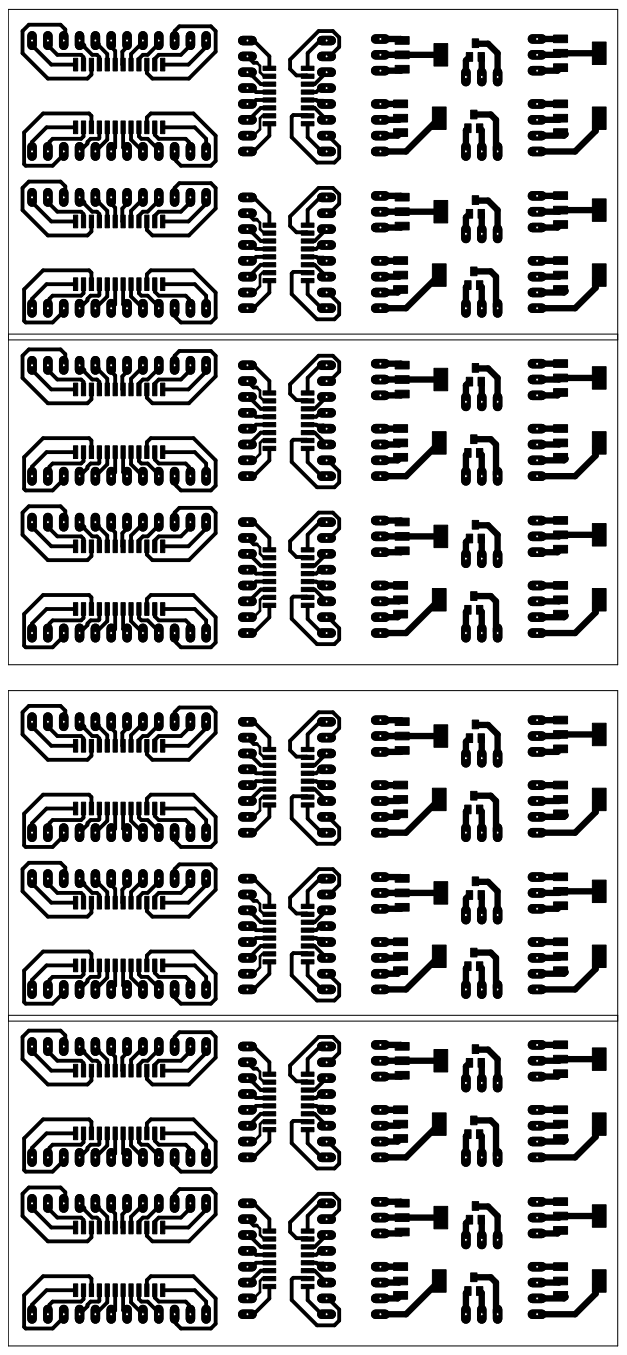
[picture p91: page 1]
