marukitano/BEP3.0/BEP2 final/BMW_alle Boards.pdf

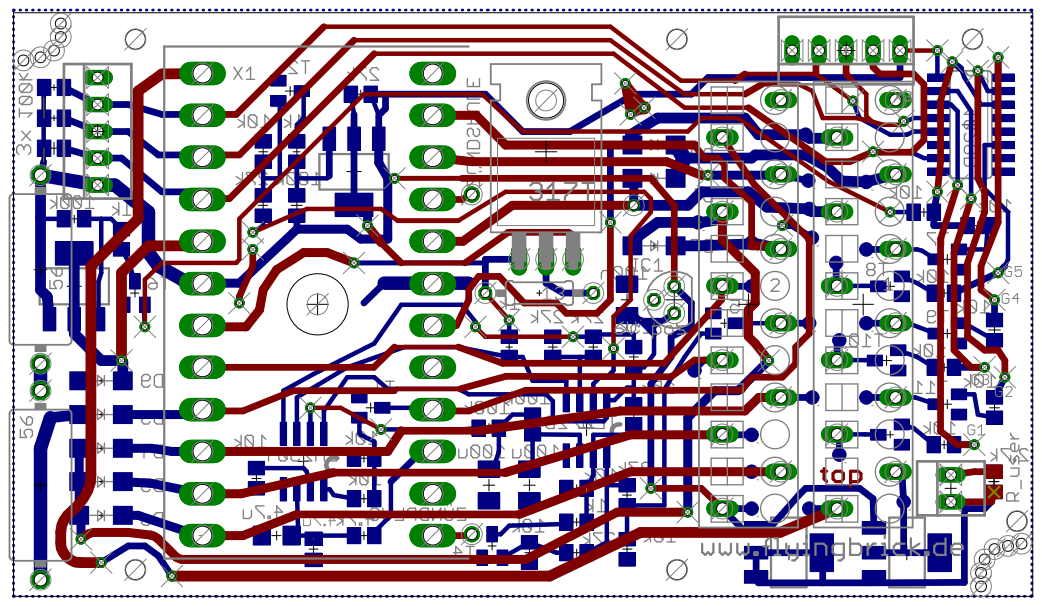
[picture p92: page 1]

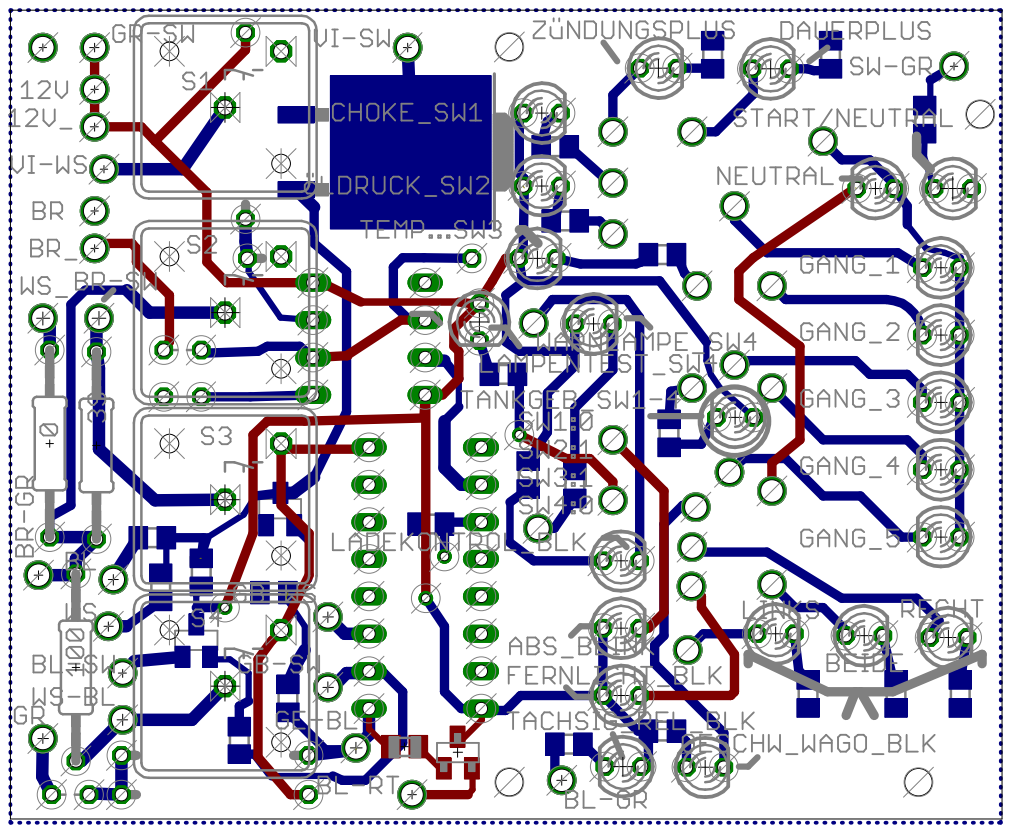
[picture p93: page 2]

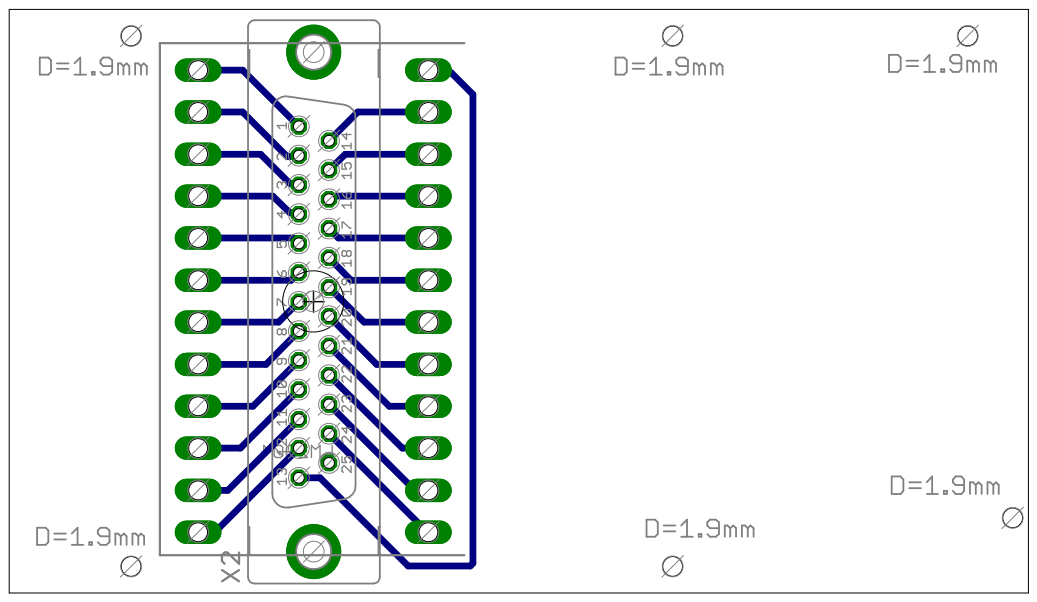
[picture p94: page 3]
