marukitano/BEP3.0/BEP2 final/BMW_final_front and back.pdf

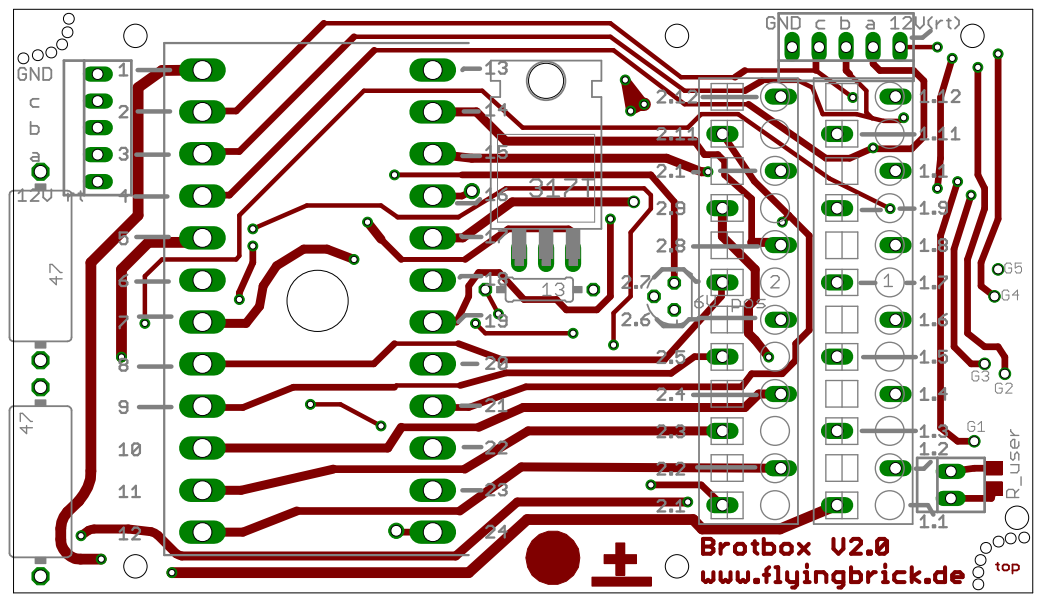
[picture p95: page 1]

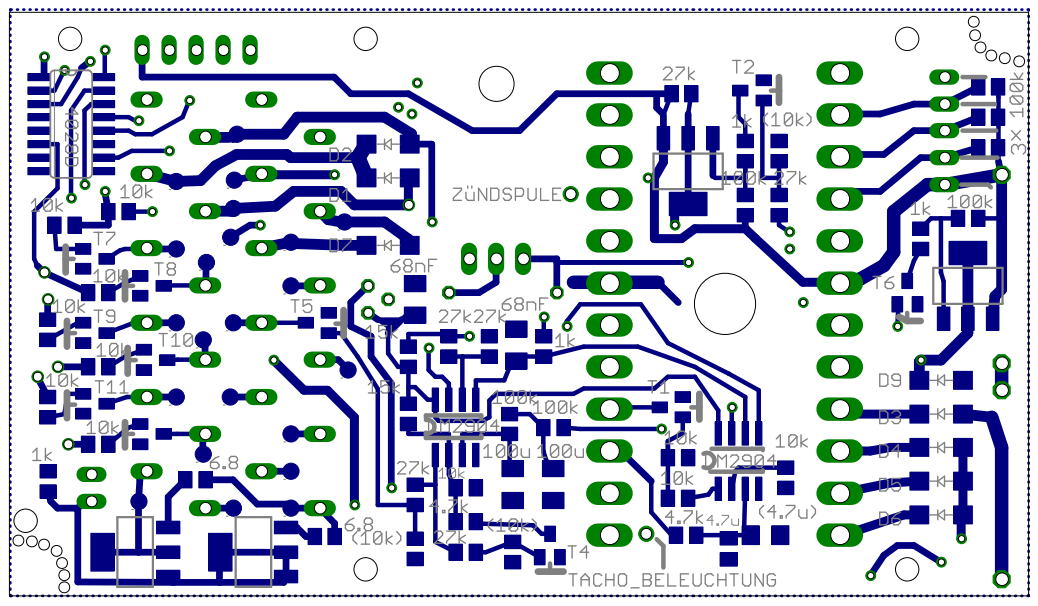
[picture p96: page 2]
