marukitano/BEP3.0/BEP2 final/BMW_Schema_final.pdf

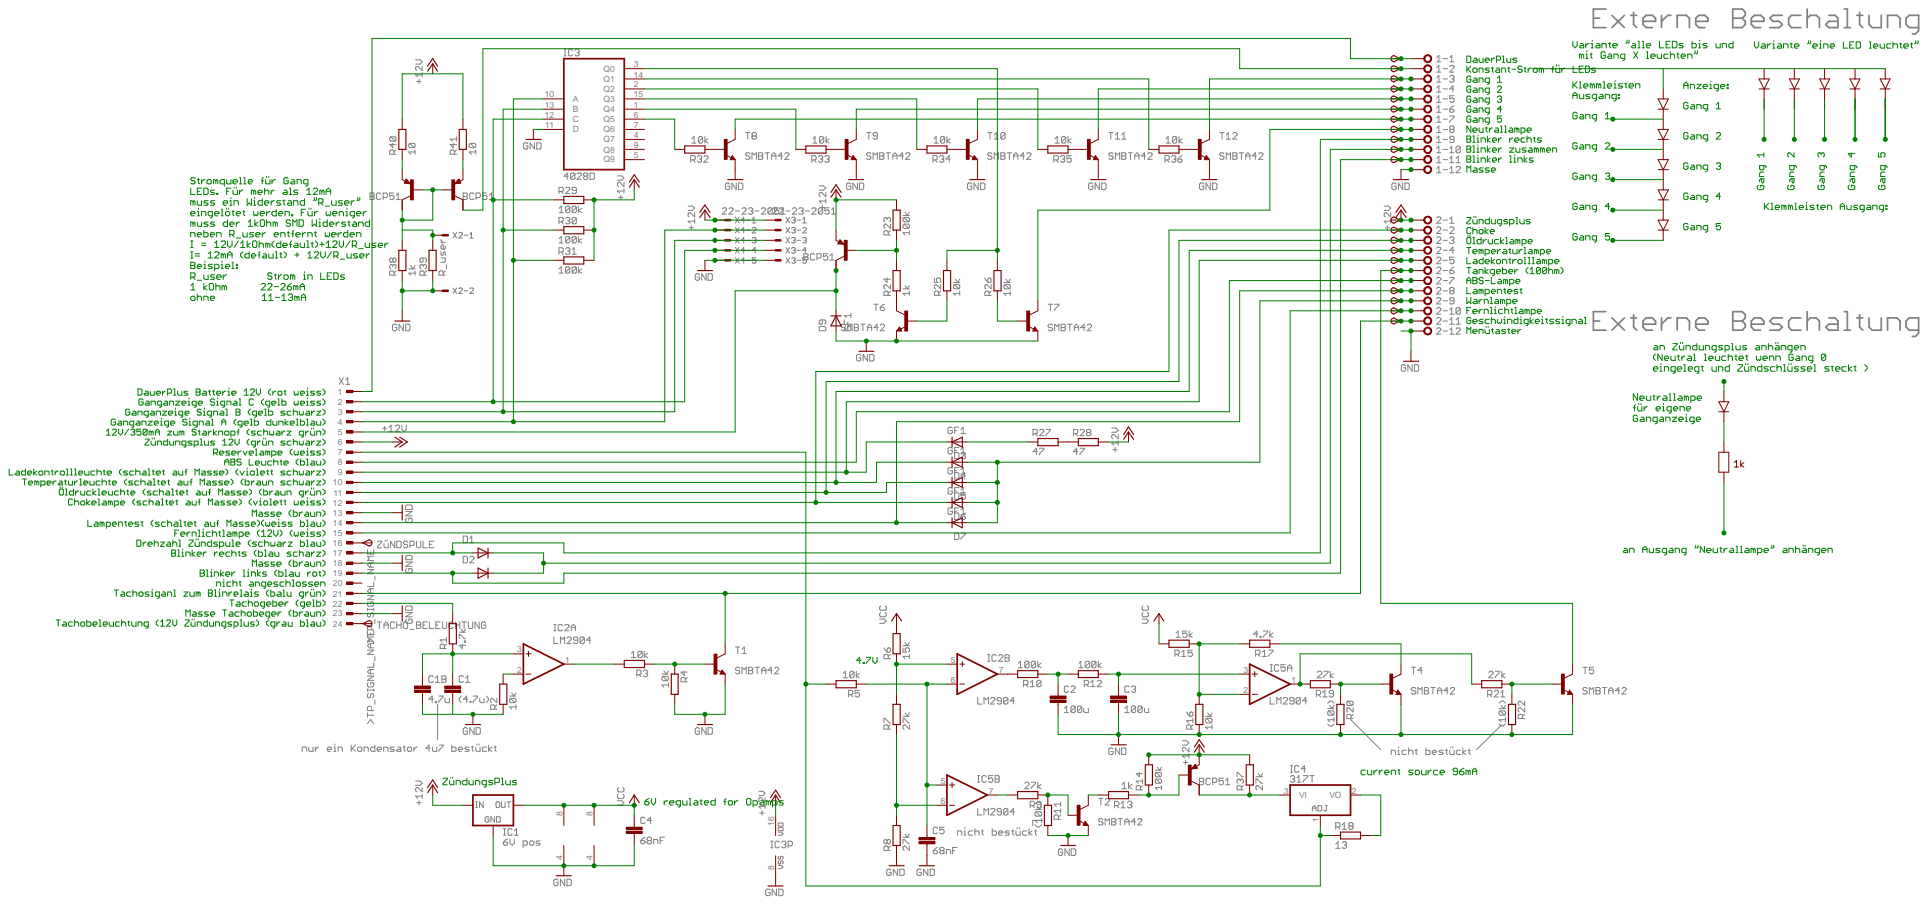
[picture p97: page 1]
