marukitano/BEP3.0/display/BEPdisp/BEPdisp1.pdf

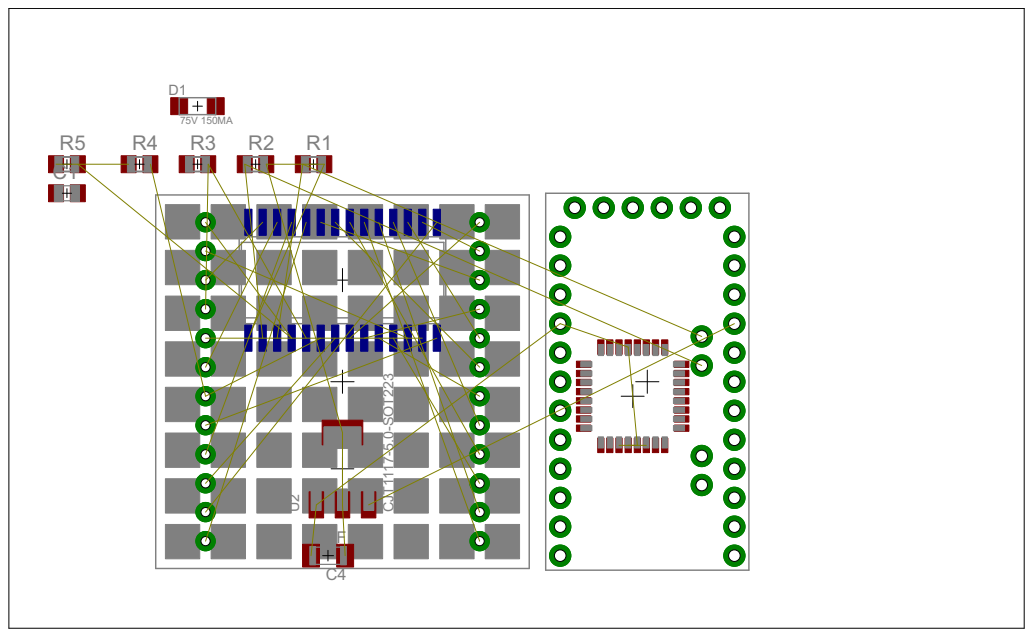
[picture p98: page 1]
